moorescloud/holiday-hardware/Holiday ECO 001.pdf

ECO 001 for MooresCloud Holiday r2 PCBA

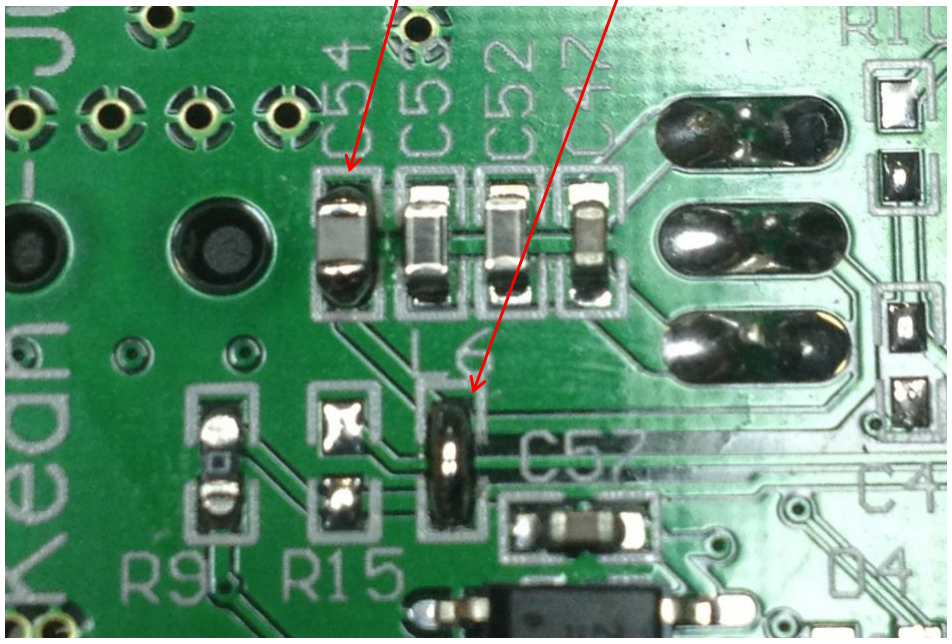
[picture p1: figure]

Prepared by Kean Electronics | Revision 1 | 1 of 2

### Kean Electronics

IT Consulting and embedded systems design
Unit 29, 29 Leighton Place, Hornsby PO Box 3316, Asquith NSW 2077 P: 02 9482 5007 M: 0414 245 326 E: kean@kean.com.au

## MooresCloud Holiday Engineering Change Order ECO 001 for Holiday r2 PCB

18th October 2013

To meet EMC radiated emissions requirements, the following three changes should be made to each Holiday Controller revision 2 PCBA

1) Populate C54 with 680pF 50V NP0 ceramic capacitor (0603 size, although 0805 fits as shown in photo below)
2) Remove L6 and short the pads with solder (or a 0R resistor, 0603 size)

PTO for third change

ECO 001 for MooresCloud Holiday r2 PCBA

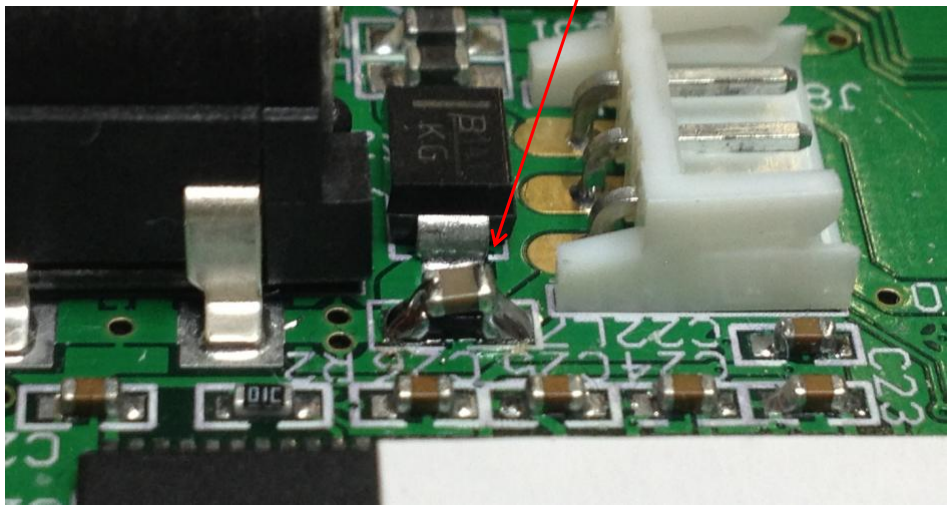
[picture p2: figure]

Prepared by Kean Electronics | Revision 1 | 2 of 2
3) Add C58 a 1uF 50V X7R ceramic capacitor (0805 size) across L7

Parts required:

C54 = Yageo CC0603JRNPO9BN681 DigiKey part: 311-1425-1-ND

C58 = Taiyo Yuden UMK212B7105KG-T DigiKey part: 587-2910-1-ND

Substitutions can be made with equivalent parts, but only on confirmation with MooresCloud technical staff.
