moorescloud/holiday-hardware/Holiday ECO 002.pdf

ECO 002 for MooresCloud Globe r2b PCBA

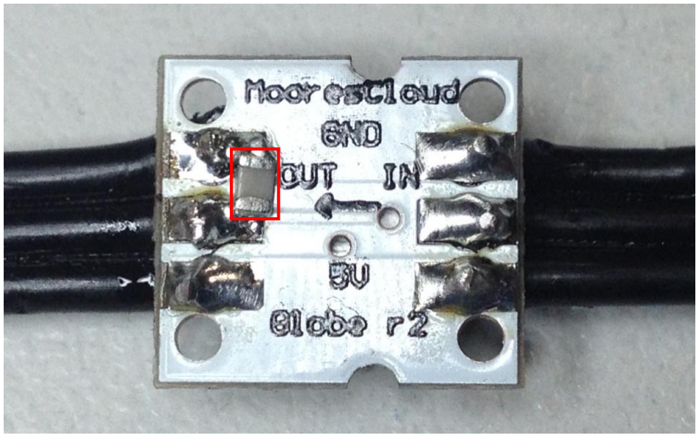
[picture p3: figure]

Prepared by Kean Electronics | Revision 1 | 1 of 2

### Kean Electronics

IT Consulting and embedded systems design
Unit 29, 29 Leighton Place, Hornsby PO Box 3316, Asquith NSW 2077 P: 02 9482 5007 M: 0414 245 326 E: kean@kean.com.au

## MooresCloud Holiday Engineering Change Order ECO 002 for Globe r2b PCBA

18th October 2013

To meet EMC radiated emissions requirements, the following change should be made to each Globe PCBA in a Holiday LED string:

1) Add C2 a 470pF 50V NP0/C0G ceramic capacitor (0805 size, 2.0x1.25mm, 0.8mm thick) between GND and DOUT solder pads on the bottom side of the PCB. The capacitor should be kept flat to ensure the PCBA still fits within the globe housing

(sufficient clearance is available). It can be mounted close to the PCB edge, or close to the OUT label.

Recommended position:

ECO 002 for MooresCloud Globe r2b PCBA

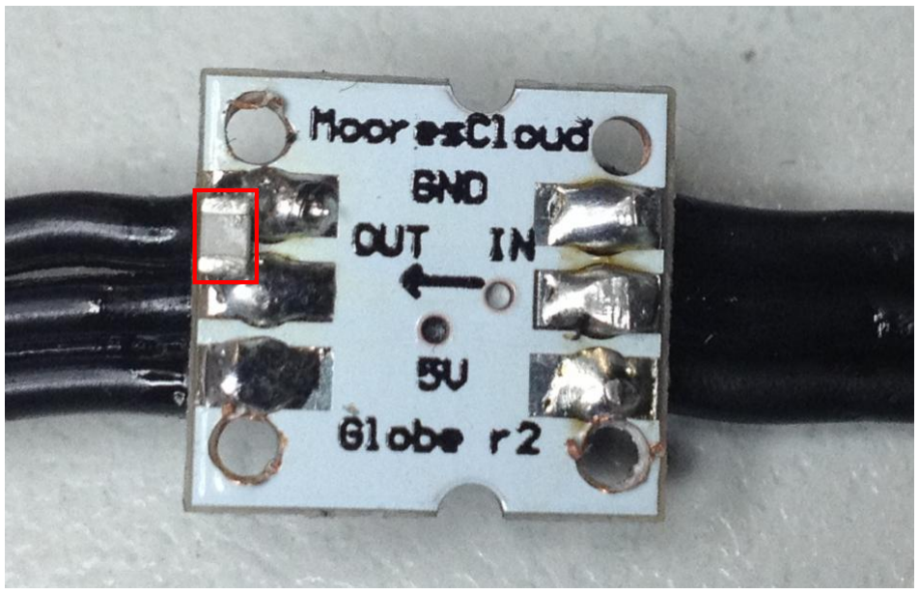
[picture p4: figure]

Prepared by Kean Electronics | Revision 1 | 2 of 2

Alternate position:

Parts required:

C2 = AVX 08055A471JAT2A DigiKey: 478-1324-2-ND

Substitutions can be made with equivalent parts, but only on confirmation with MooresCloud technical staff.
