moorescloud/holiday-hardware/Holiday r2 Schematic.PDF

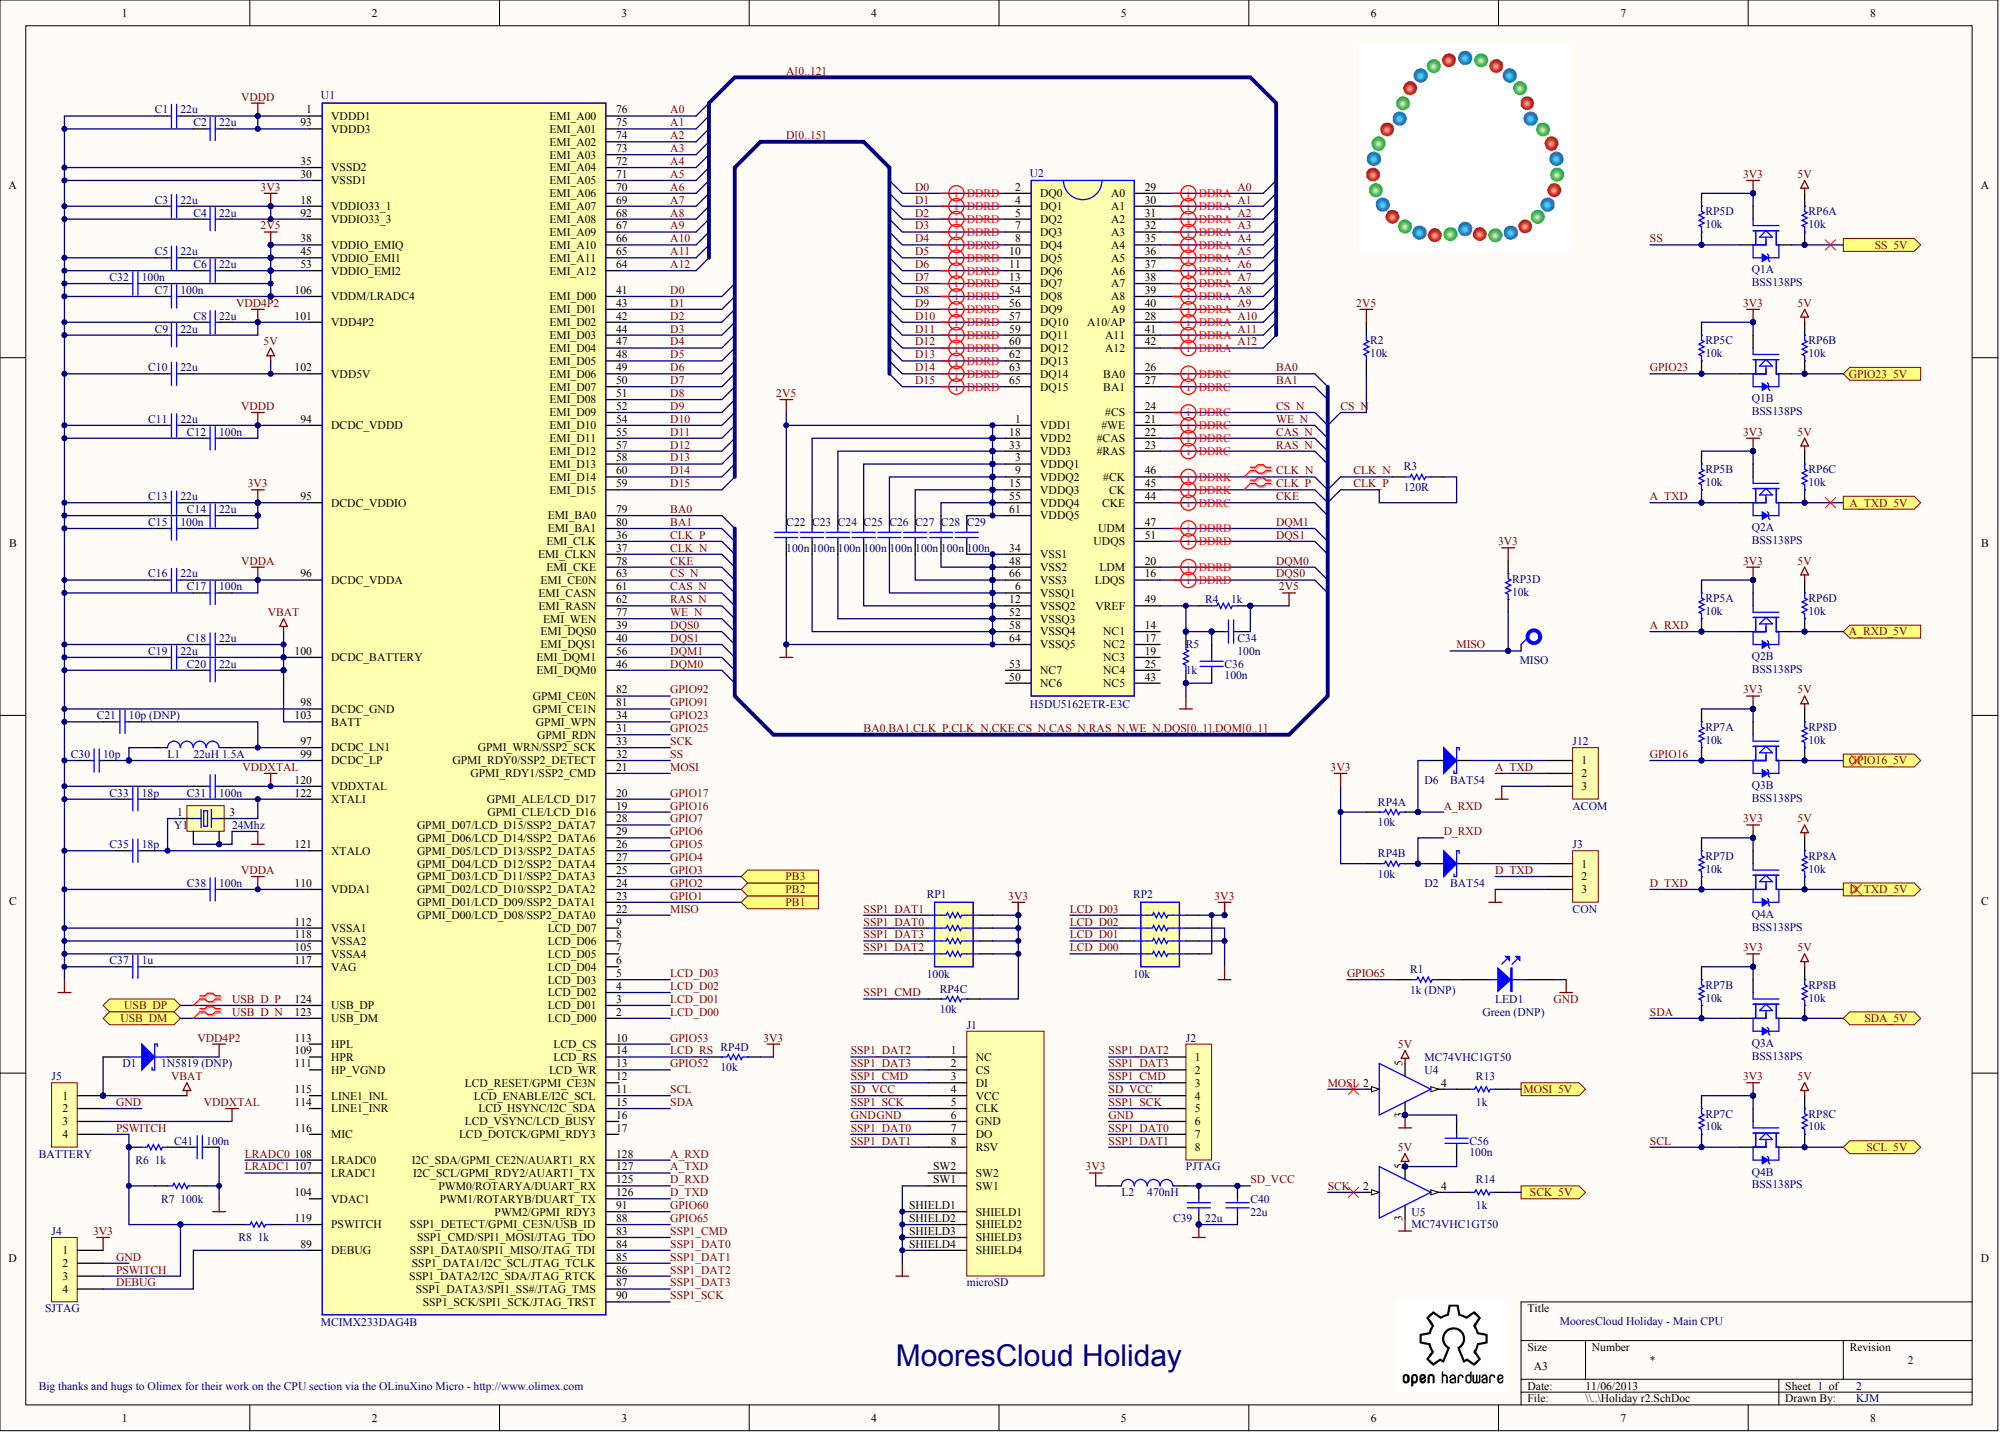
[picture p26: page 1]

i DDRD i DDRD i DDRD i DDRD i DDRD i DDRD i DDRD i DDRD i DDRD i DDRD i DDRD i DDRD i DDRD i DDRD i DDRD

i DDRA i DDRK i DDRK
i DDRA i DDRA i DDRA i DDRA i DDRA i DDRA i DDRA i DDRA i DDRA i DDRA i DDRA i DDRA i DDRD i DDRD i DDRD i DDRD

i DDRC i DDRC i DDRC i DDRC i DDRC i DDRC i DDRC

VDDQ3 15 | CLK_P
VDDQ4 55

VSS2 48
VSS3 66

VSSQ2 12

VSSQ4 58

SHIELD1
SHIELD2
SHIELD3

MooresCloud Holiday - Main CPU

Big thanks and hugs to Olimex for their work on the CPU section via the OLinuXino Micro - http://w

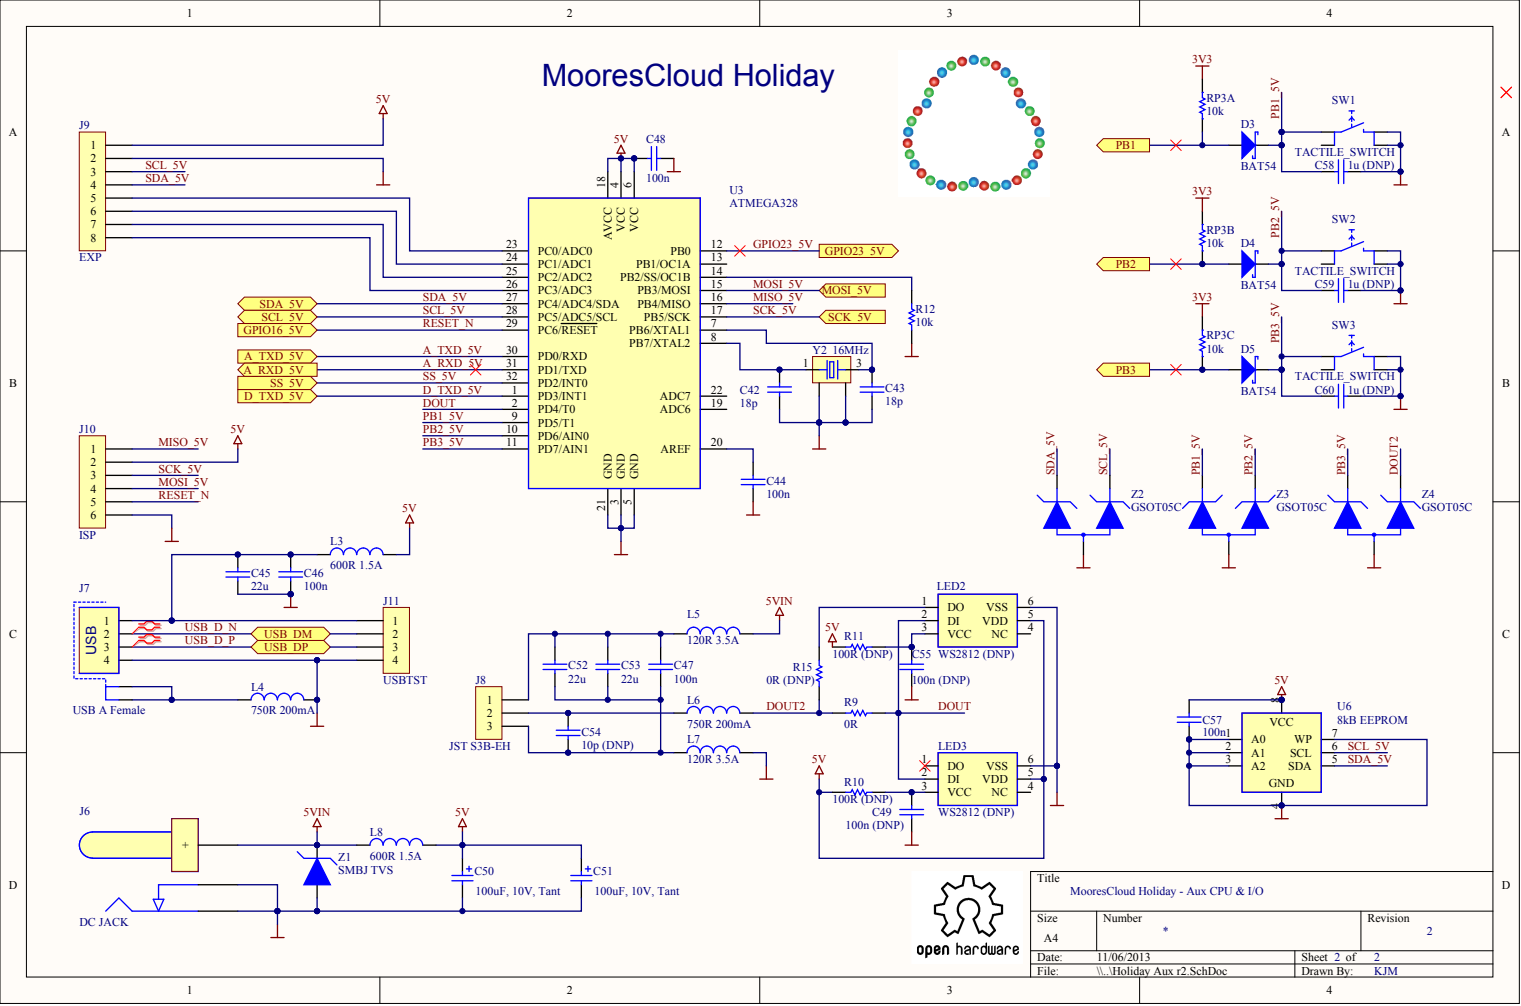
[picture p27: page 2]

PC2/ADC2 25
PC3/ADC3 26 | MOSI_5V

PD0/RXD 30 | 8

Y2 16MHz 1

MooresCloud Holiday - Aux CPU & I/O
