moorescloud/holiday-hardware/Holiday r1.pdf

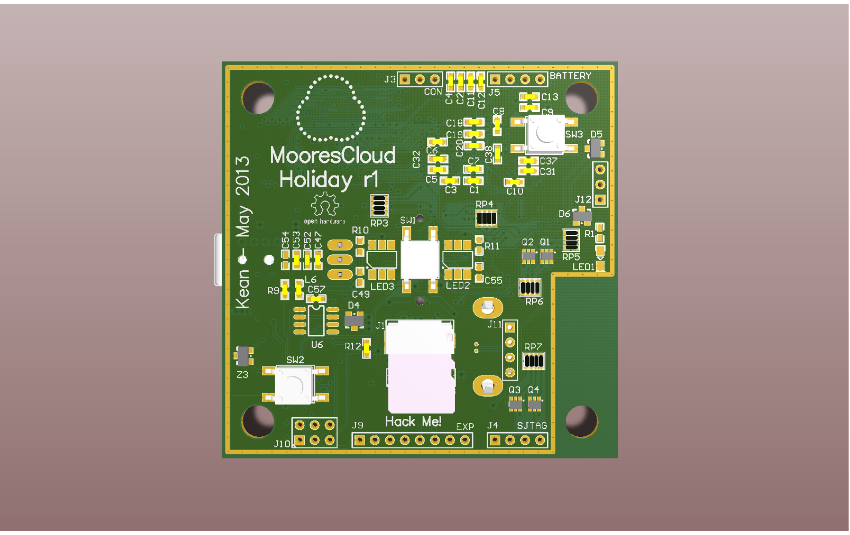
[picture p28: page 1]

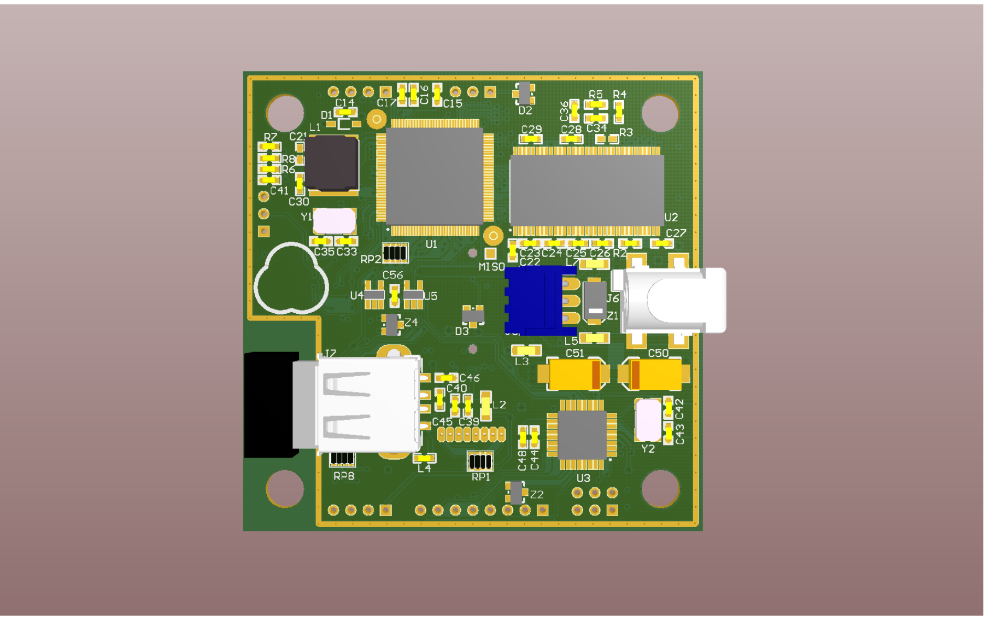
[picture p29: page 2]

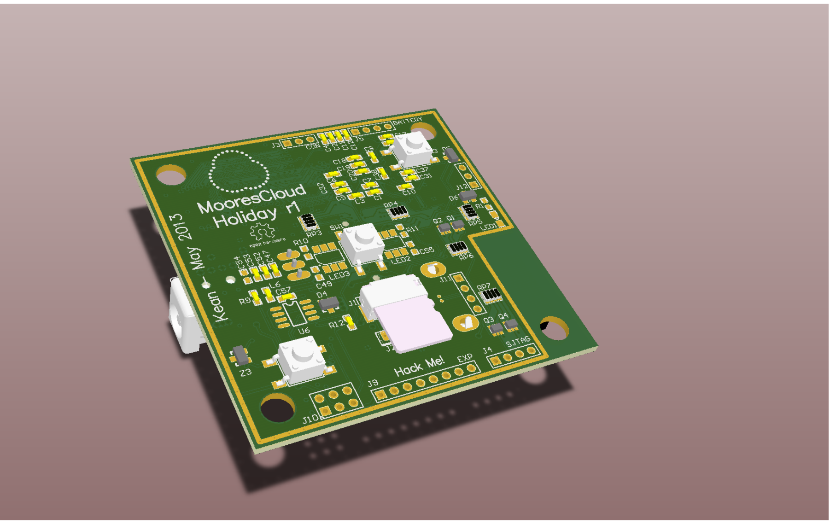
[picture p30: page 3]

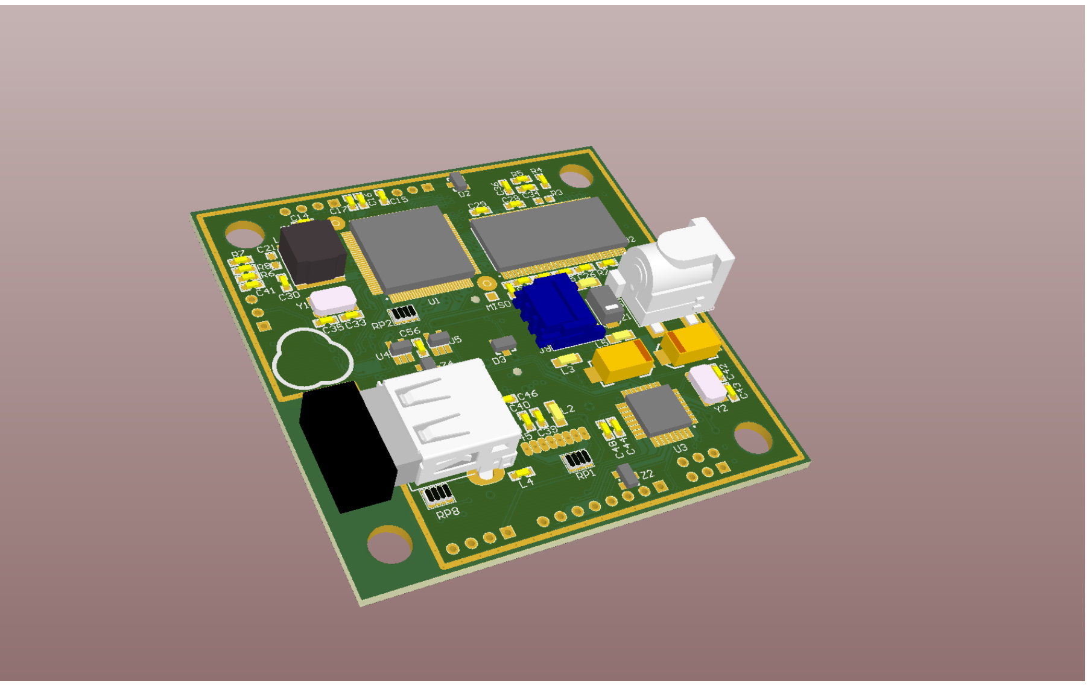
[picture p31: page 4]

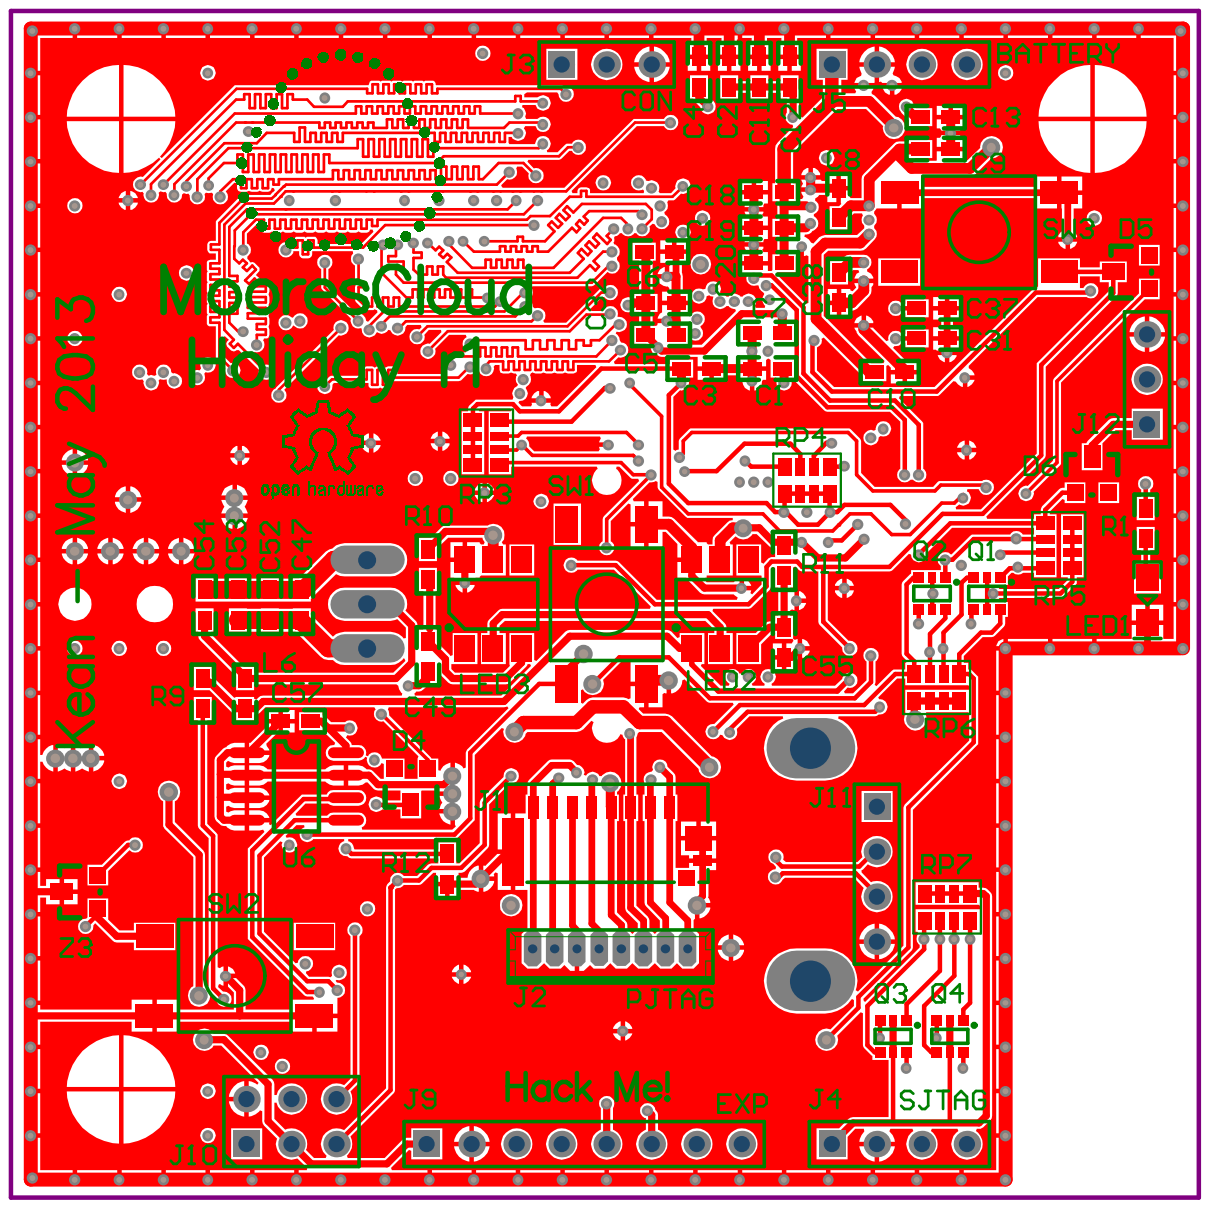
[picture p32: page 5]

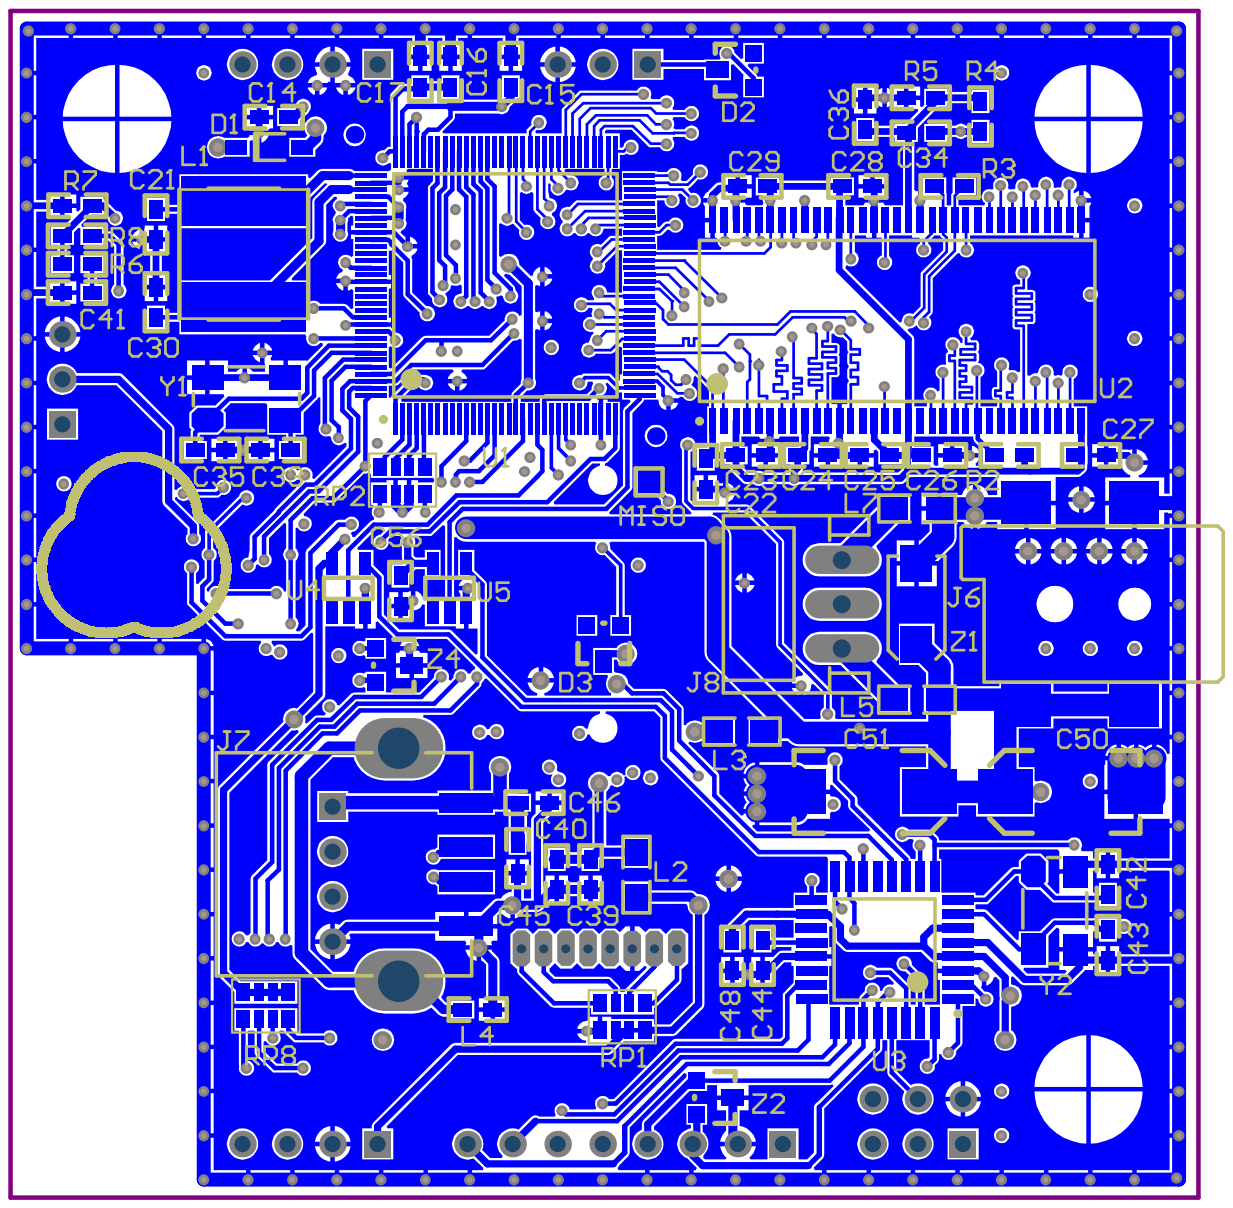
[picture p33: page 6]

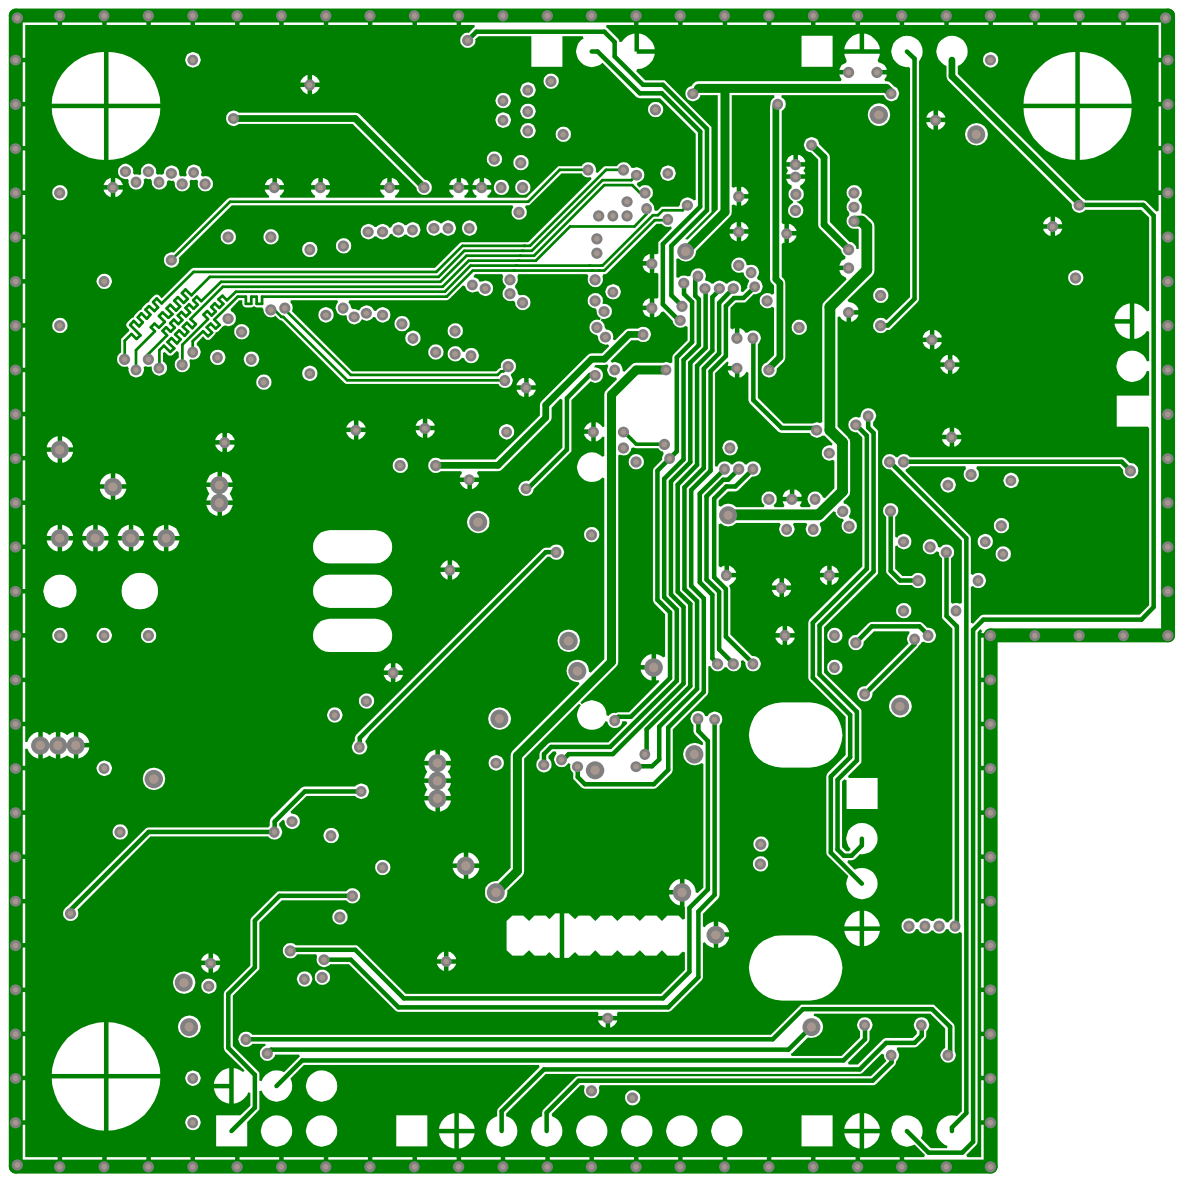
[picture p34: page 7]

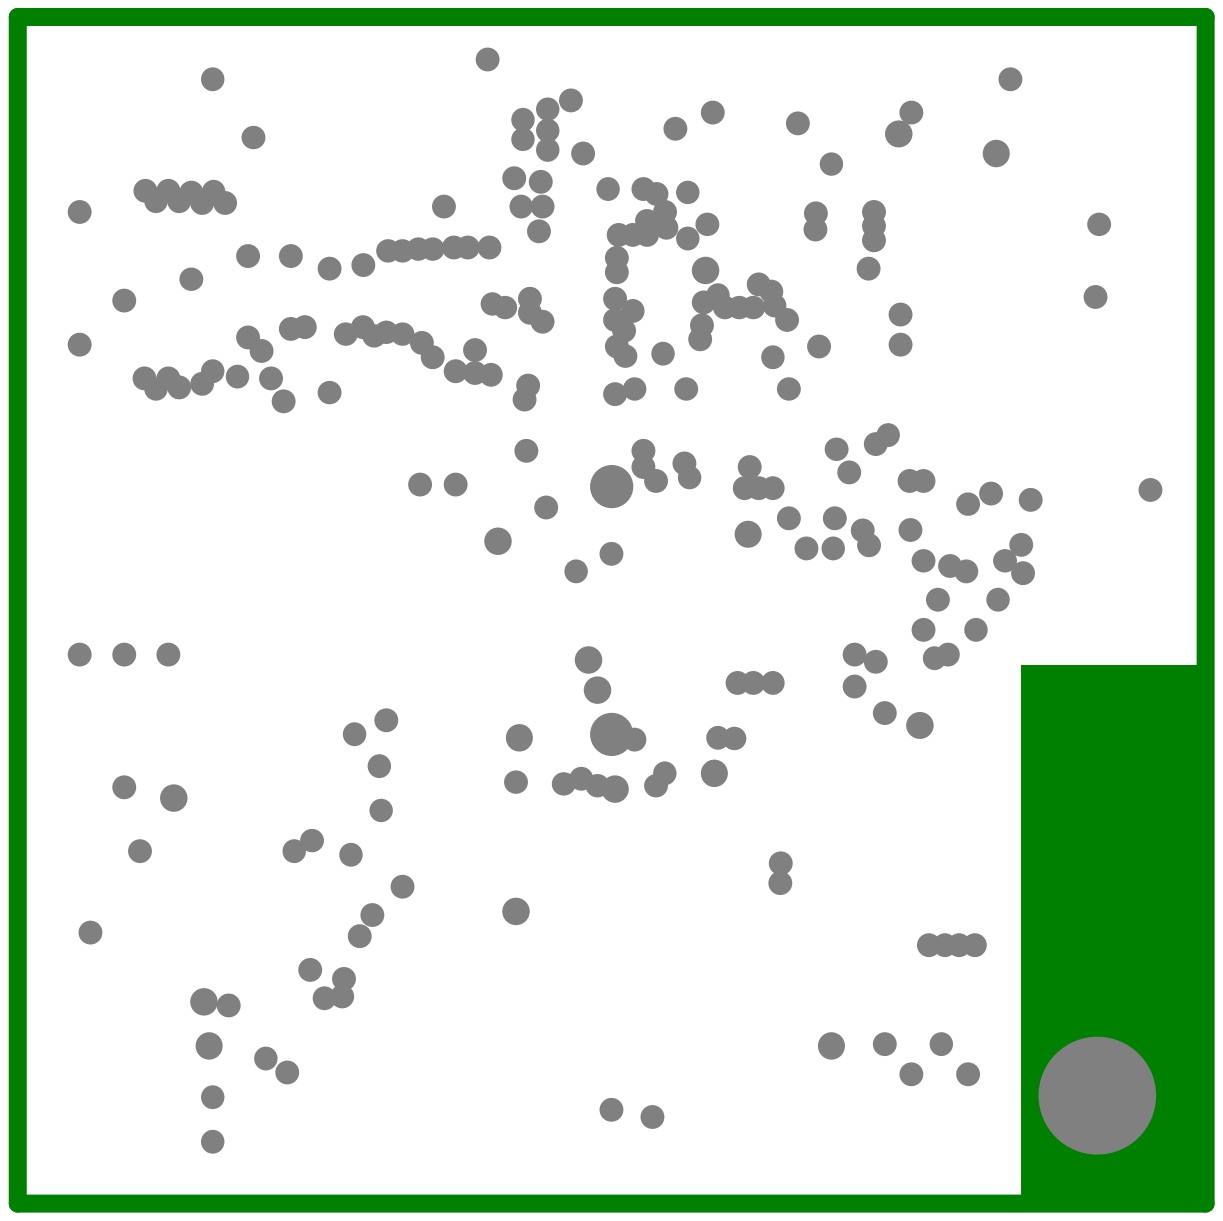
[picture p35: page 8]

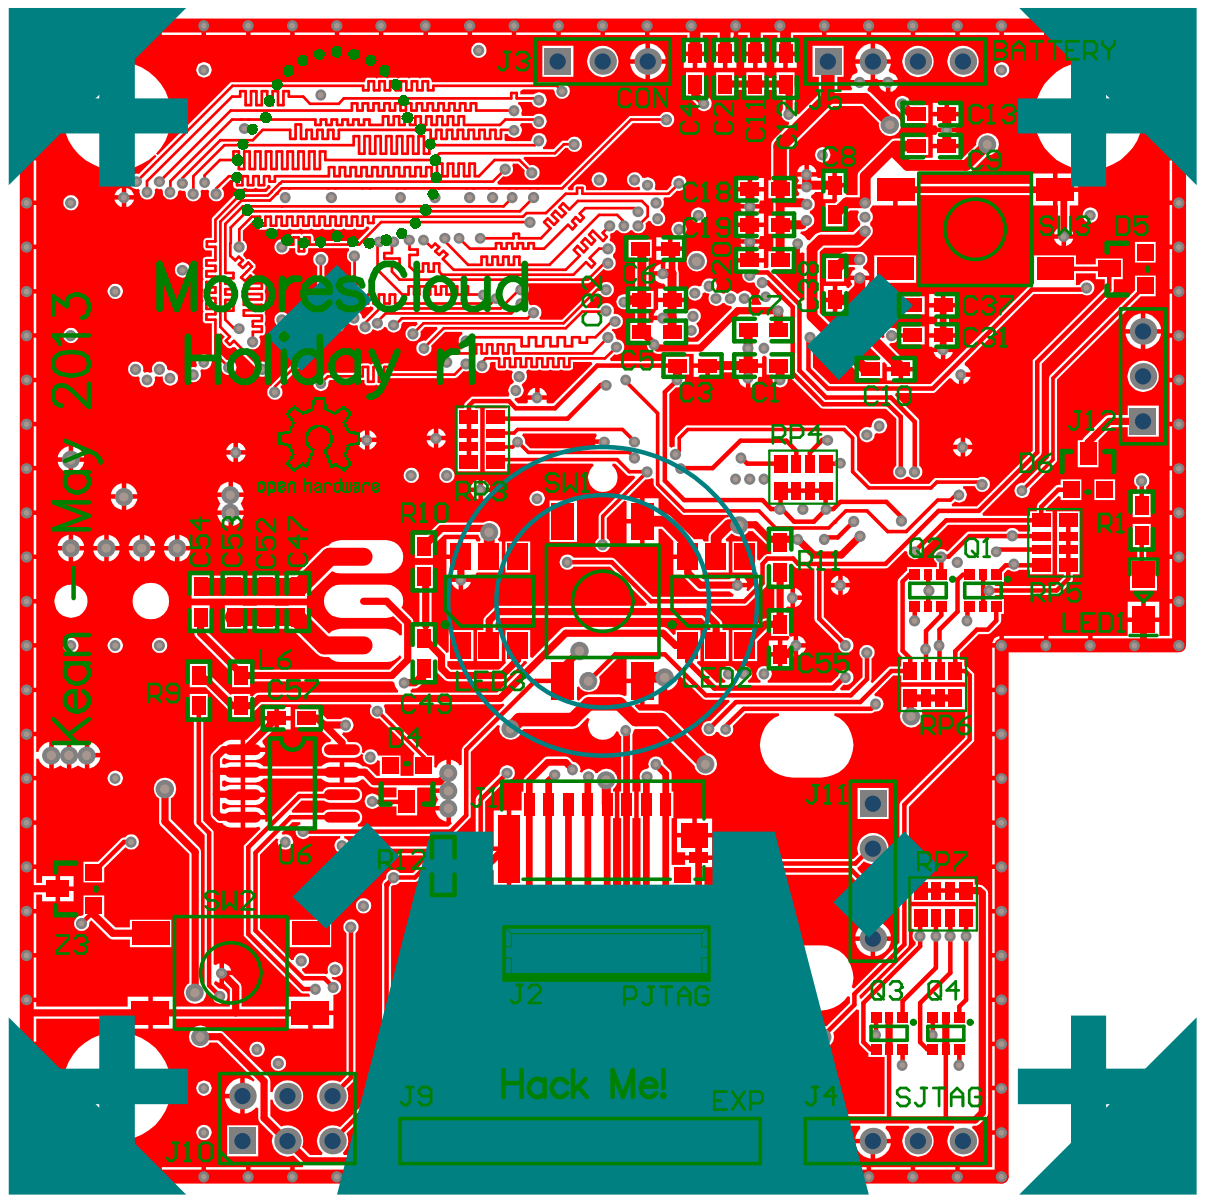
[picture p36: page 9]

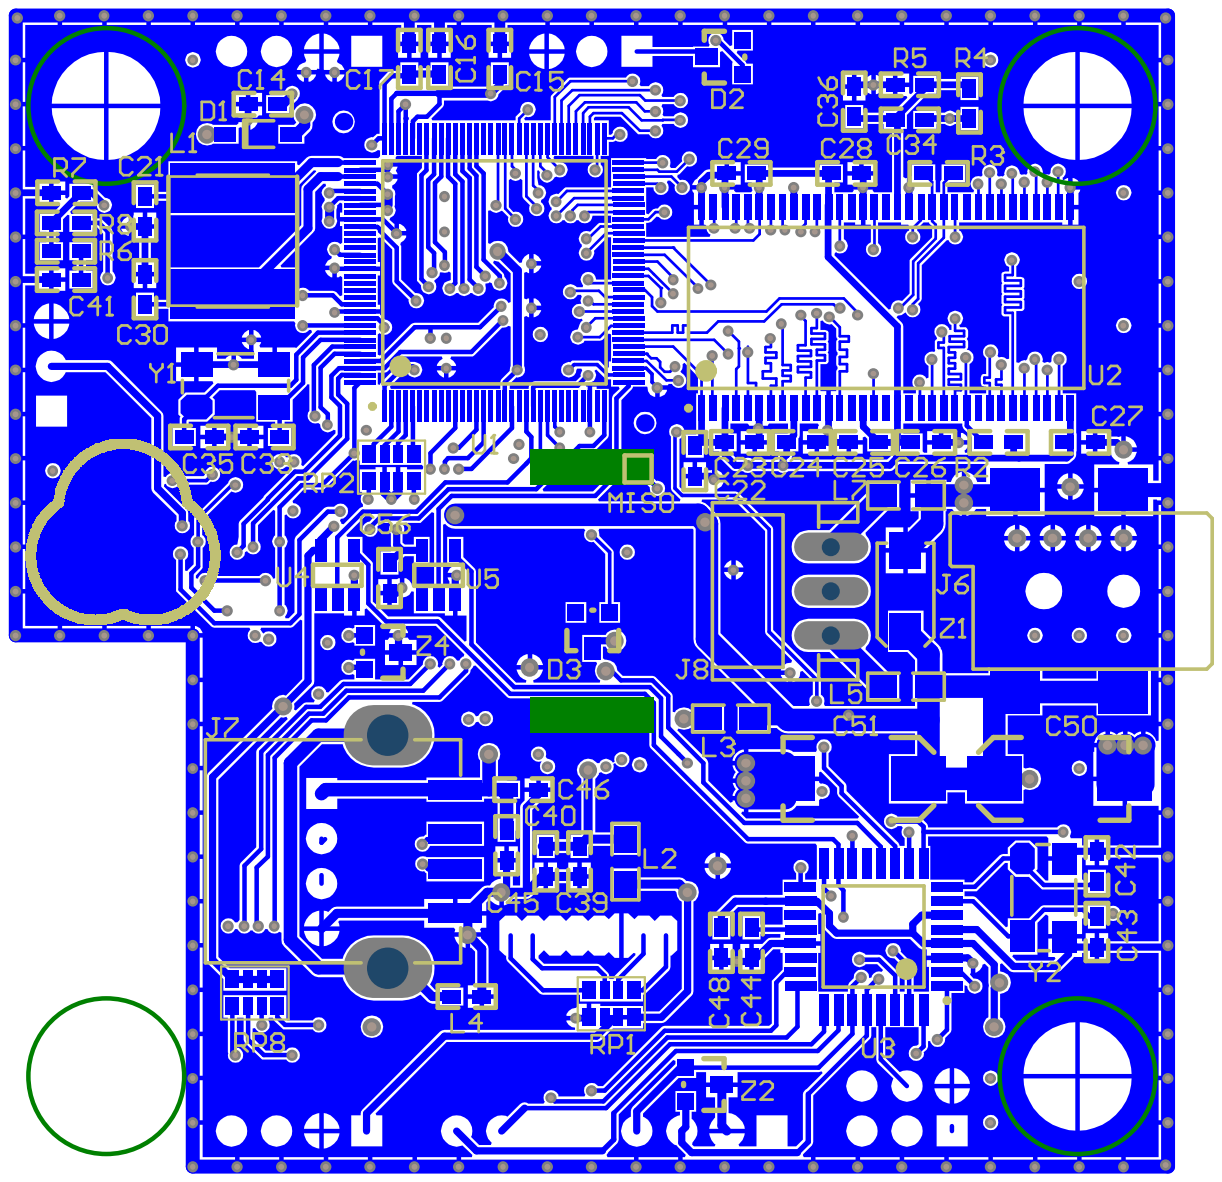
[picture p37: page 10]

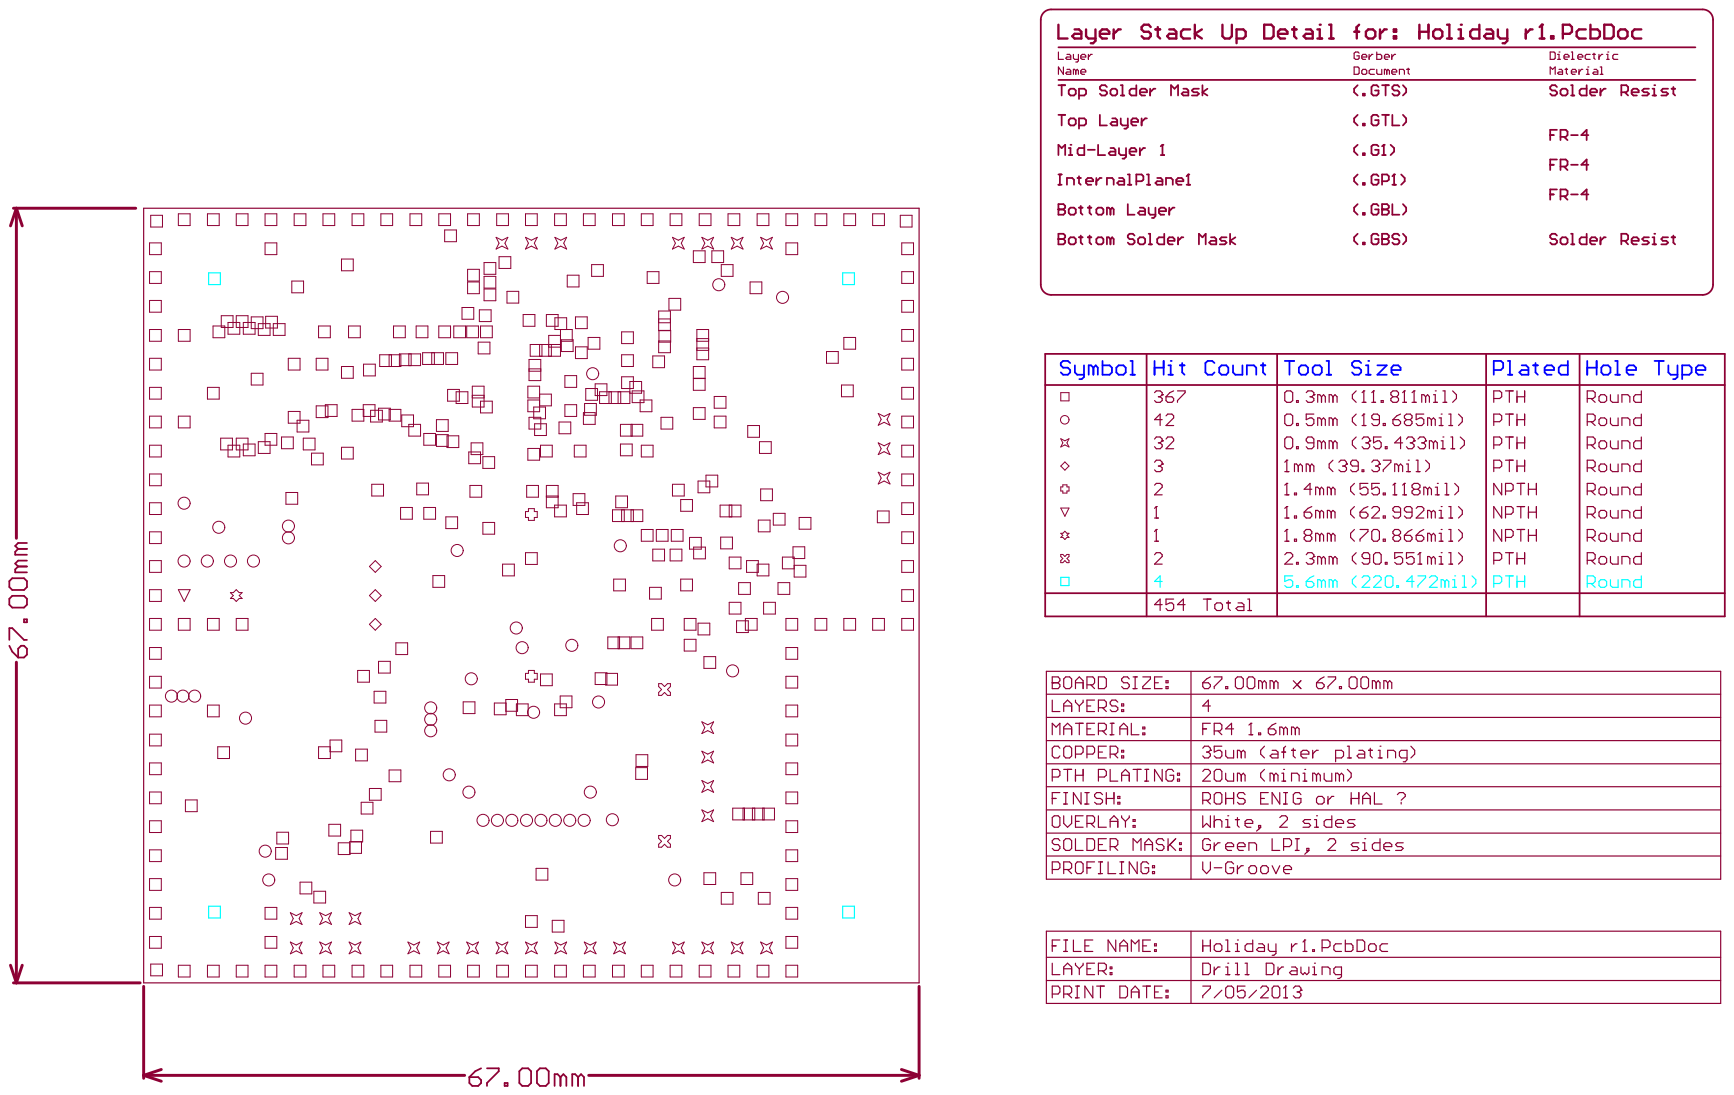
[picture p38: page 11]
