moorescloud/holiday-hardware/MooresGlobe r1 Panel.PDF

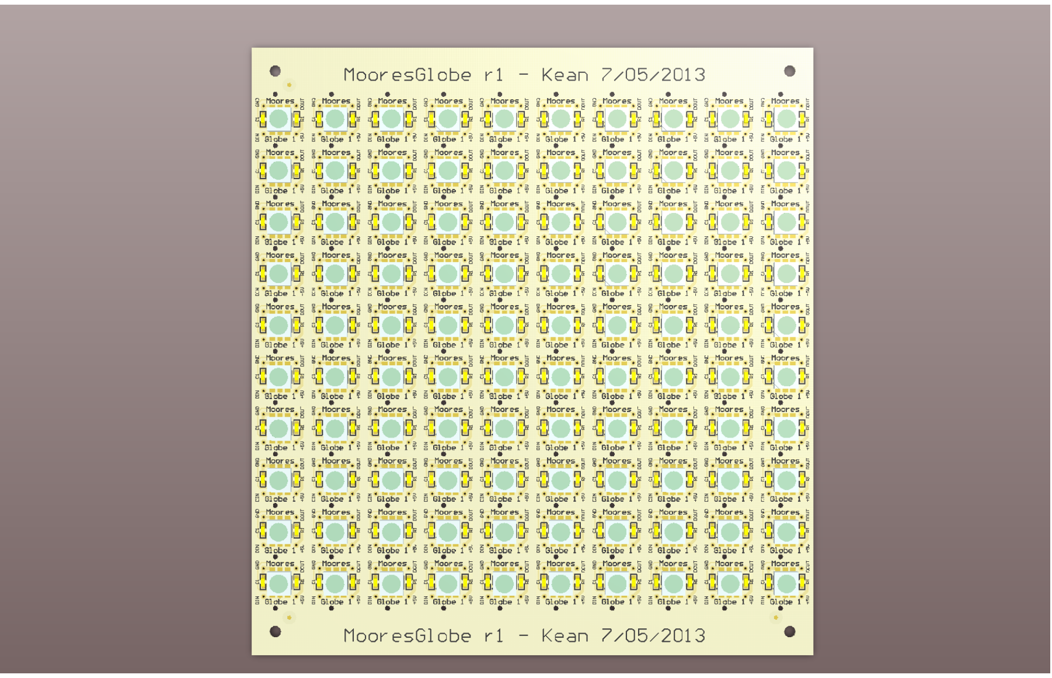
[picture p39: page 1]

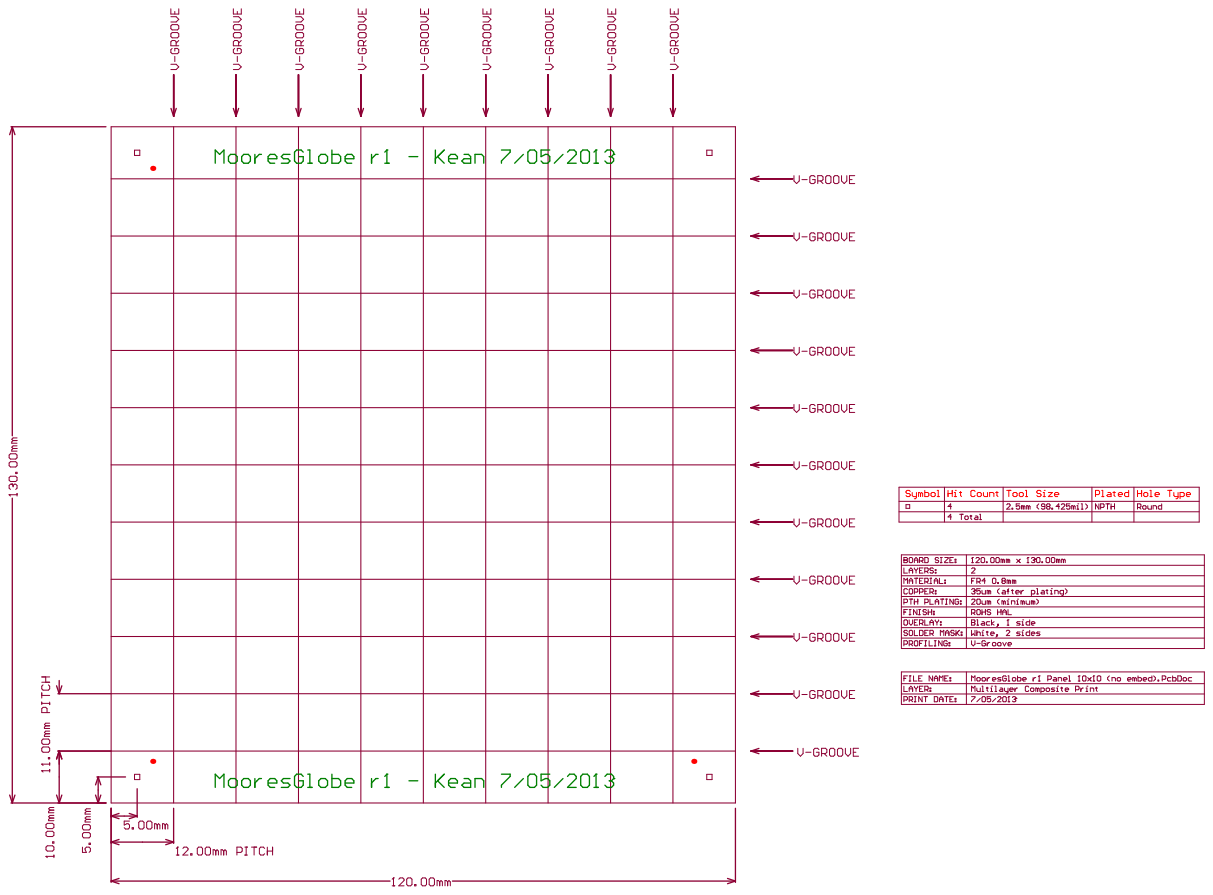
[picture p40: page 2]
