moorescloud/holiday-hardware/MooresGlobe r1.PDF

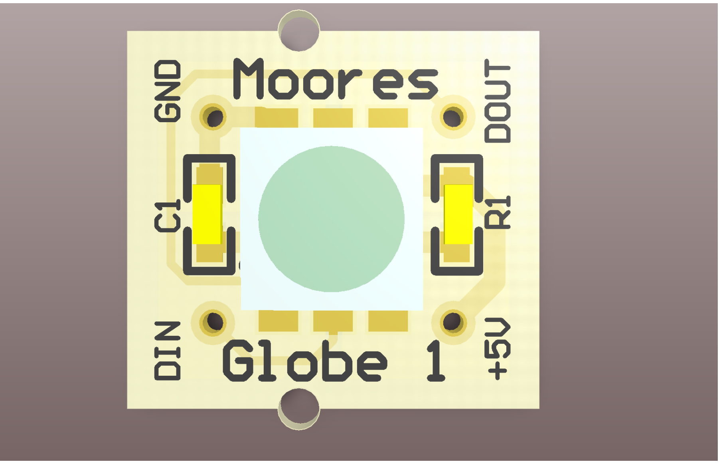
[picture p41: page 1]

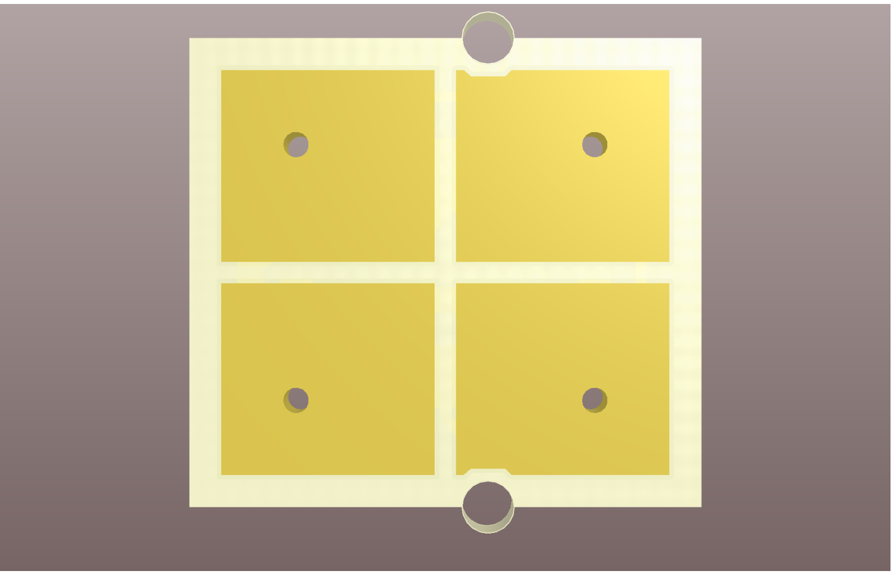
[picture p42: page 2]

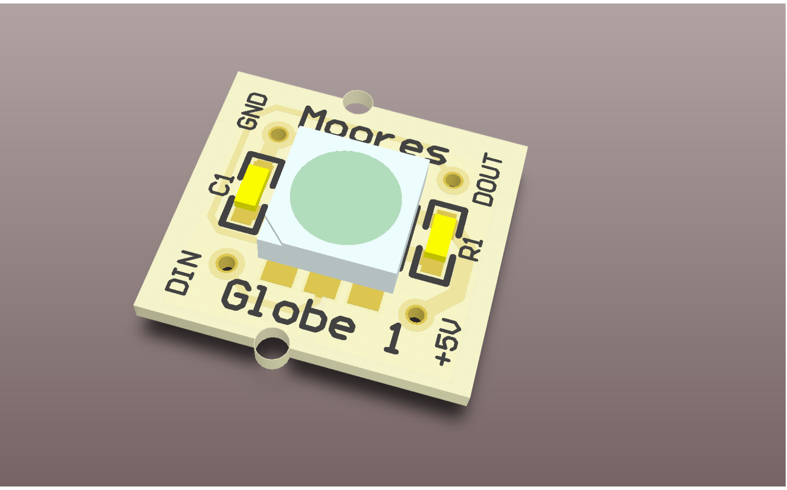
[picture p43: page 3]

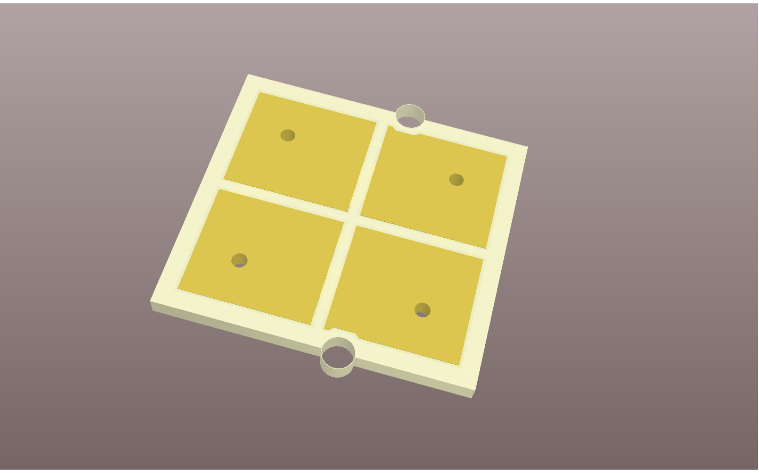
[picture p44: page 4]

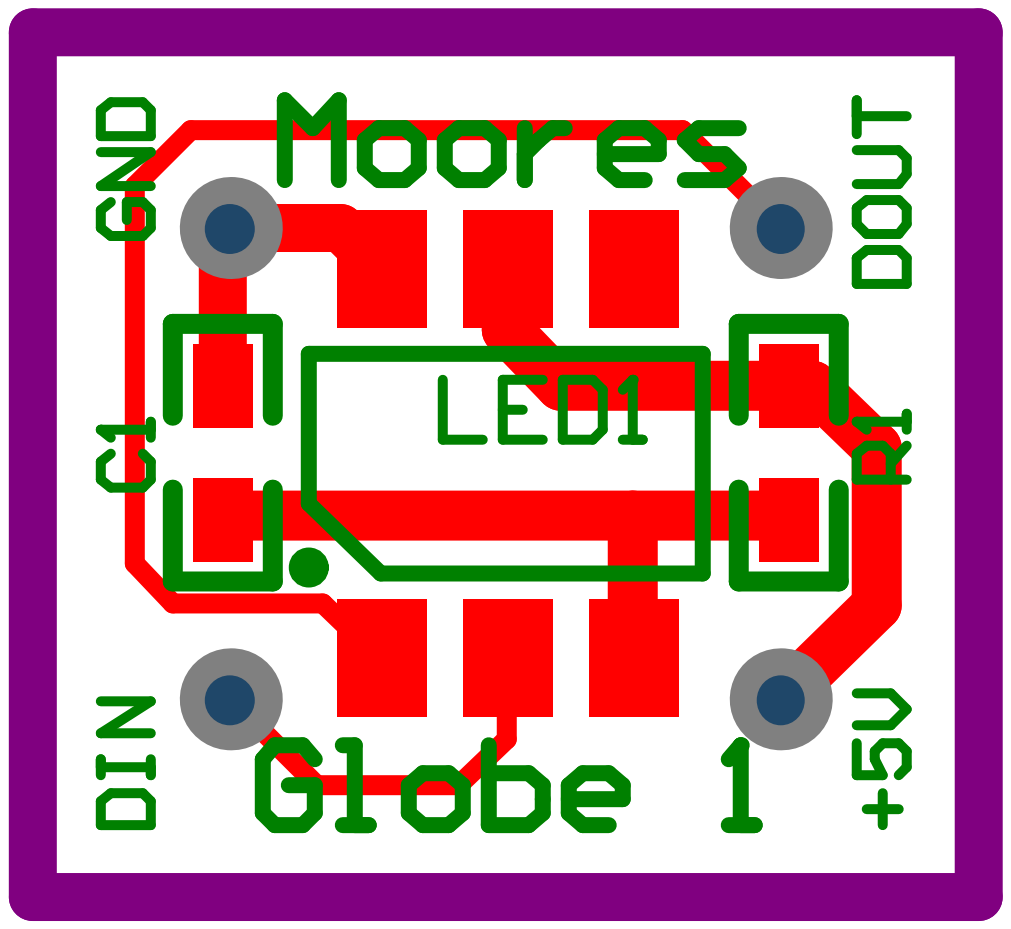
[picture p45: page 5]

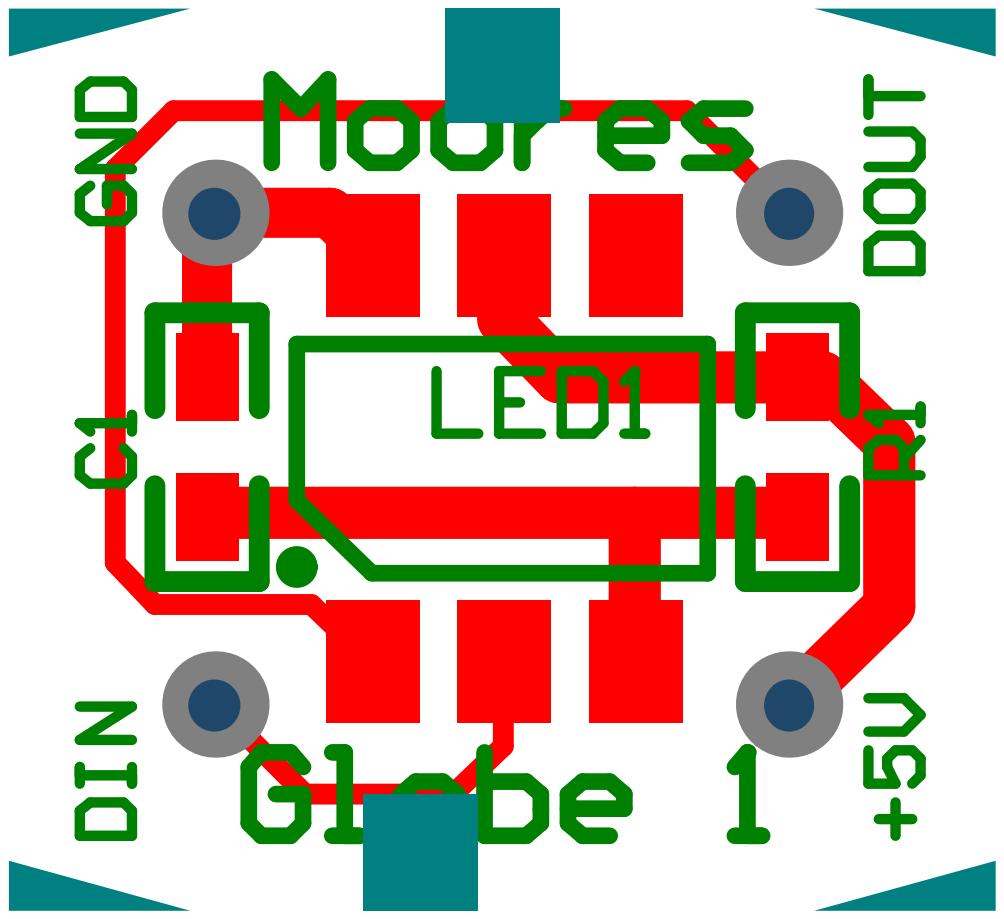
[picture p46: page 7]

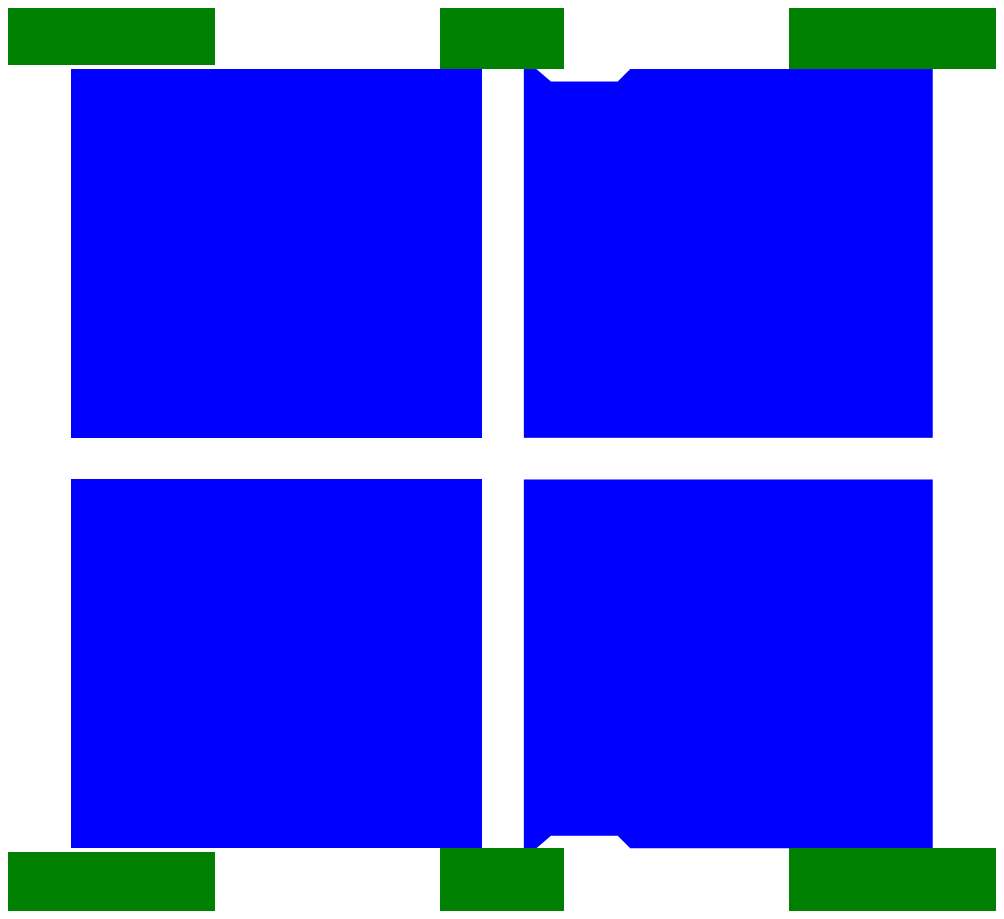
[picture p47: page 8]

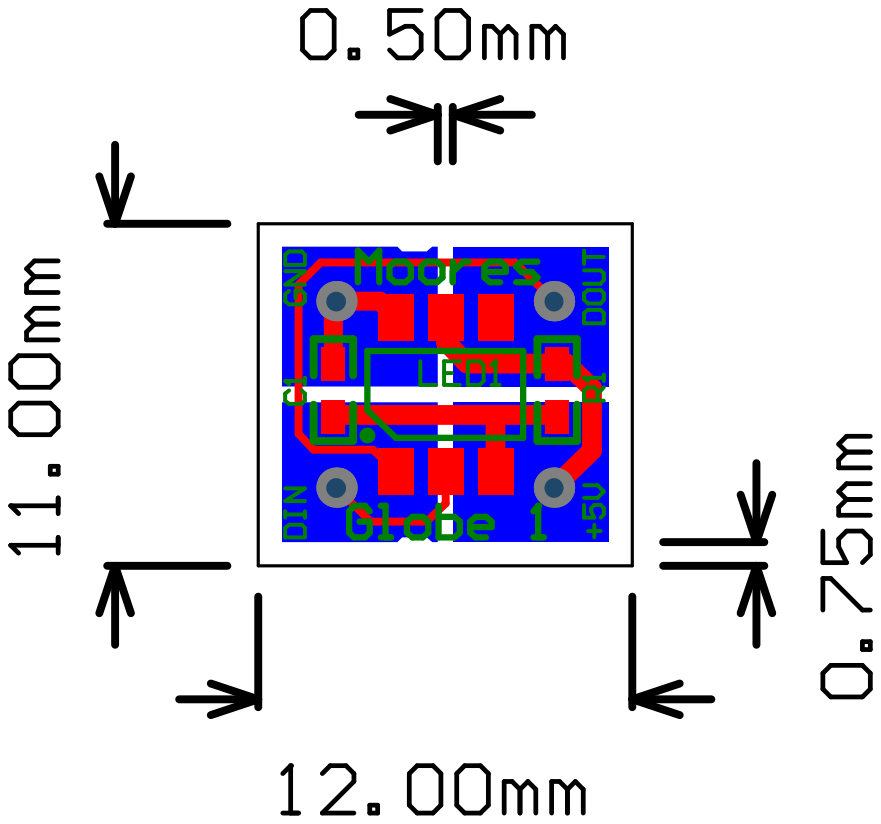
[picture p48: page 9]

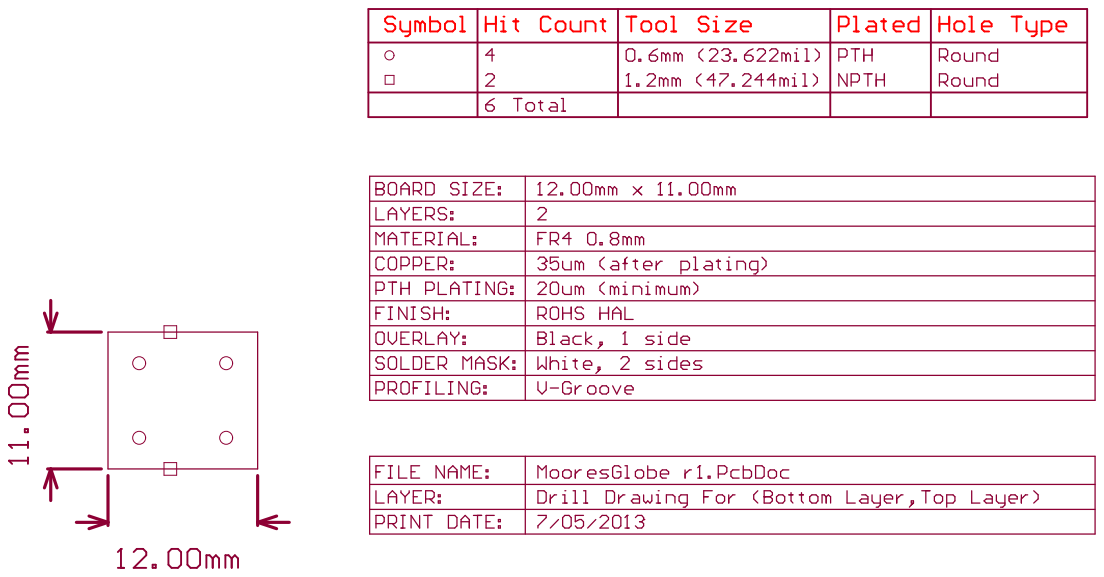
[picture p49: page 10]
