moorescloud/holiday-hardware/MooresGlobe r1S Panel.PDF

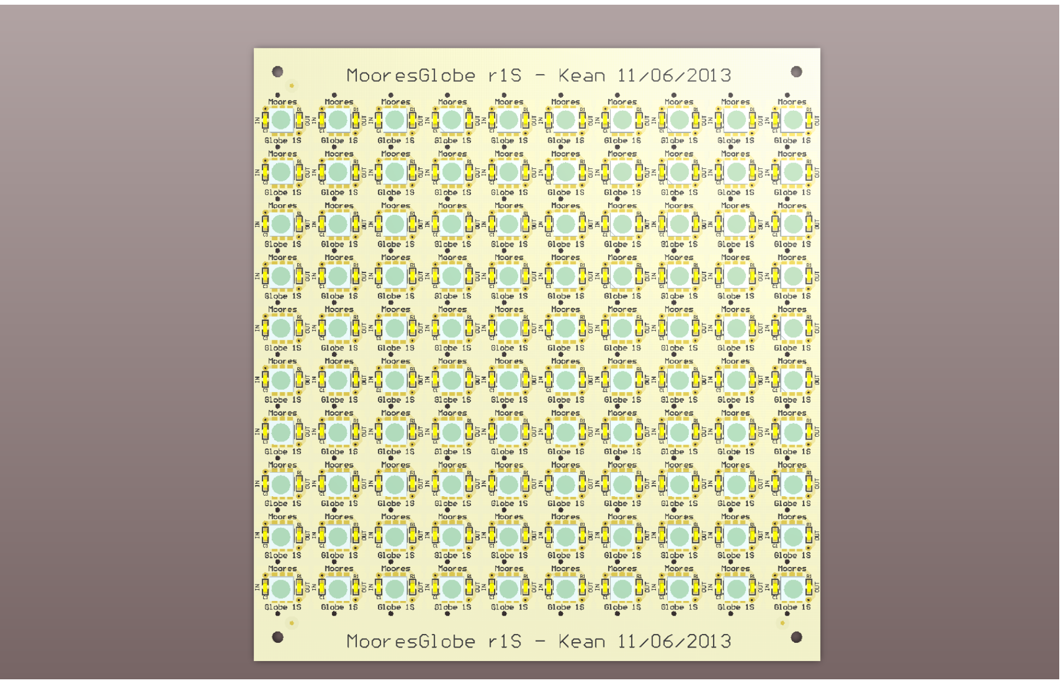
[picture p50: page 1]

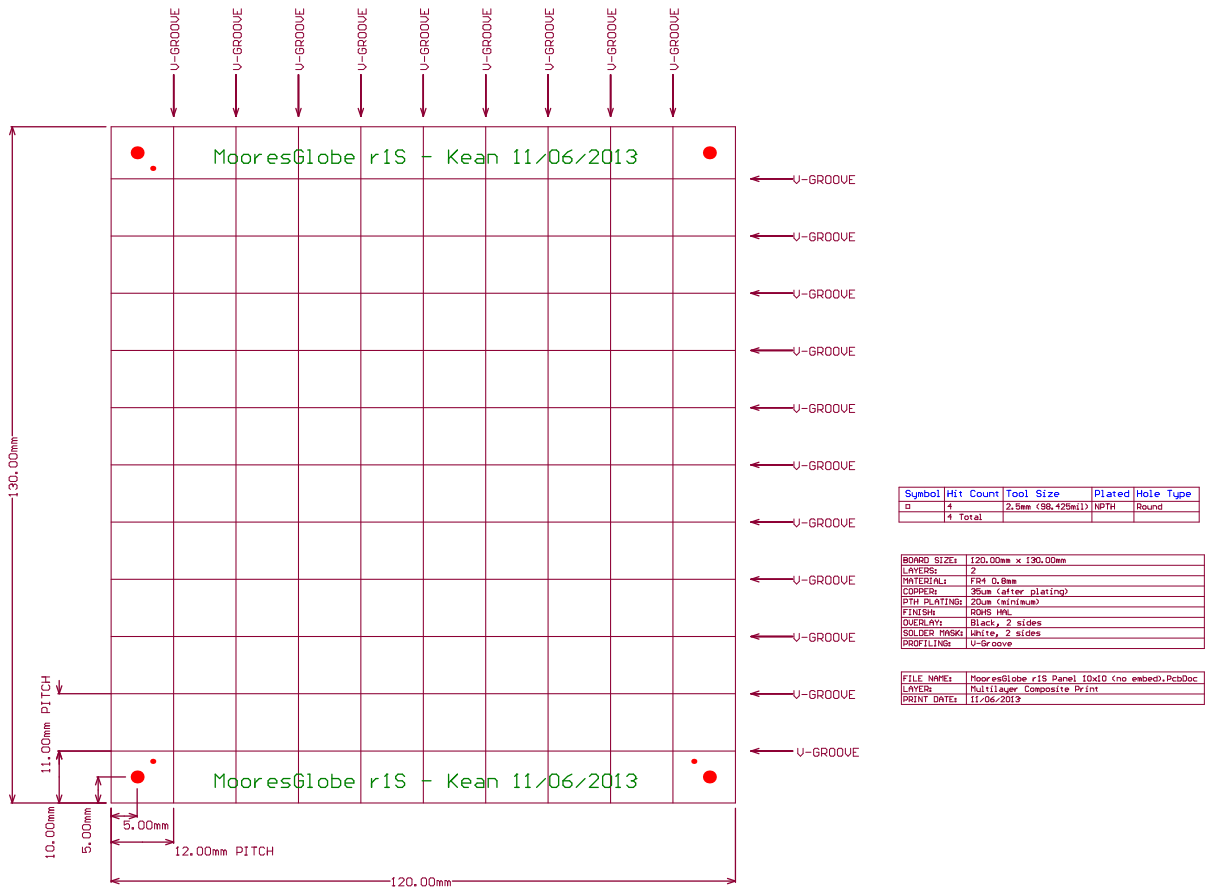
[picture p51: page 2]
