moorescloud/holiday-hardware/MooresGlobe r2 Panel.PDF

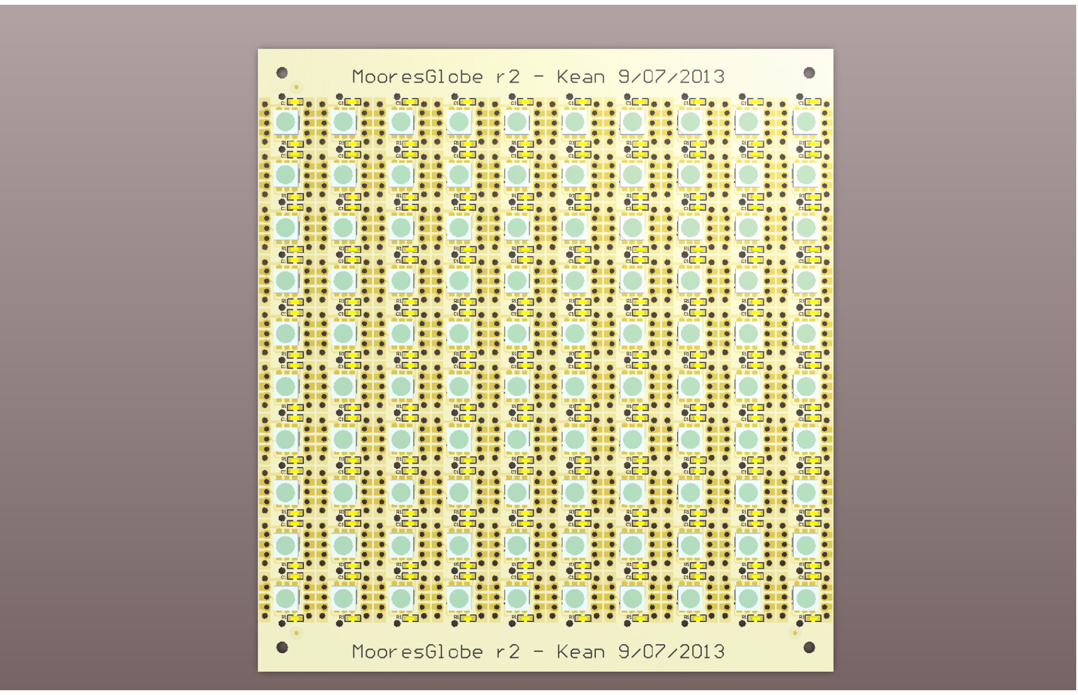
[picture p62: page 1]

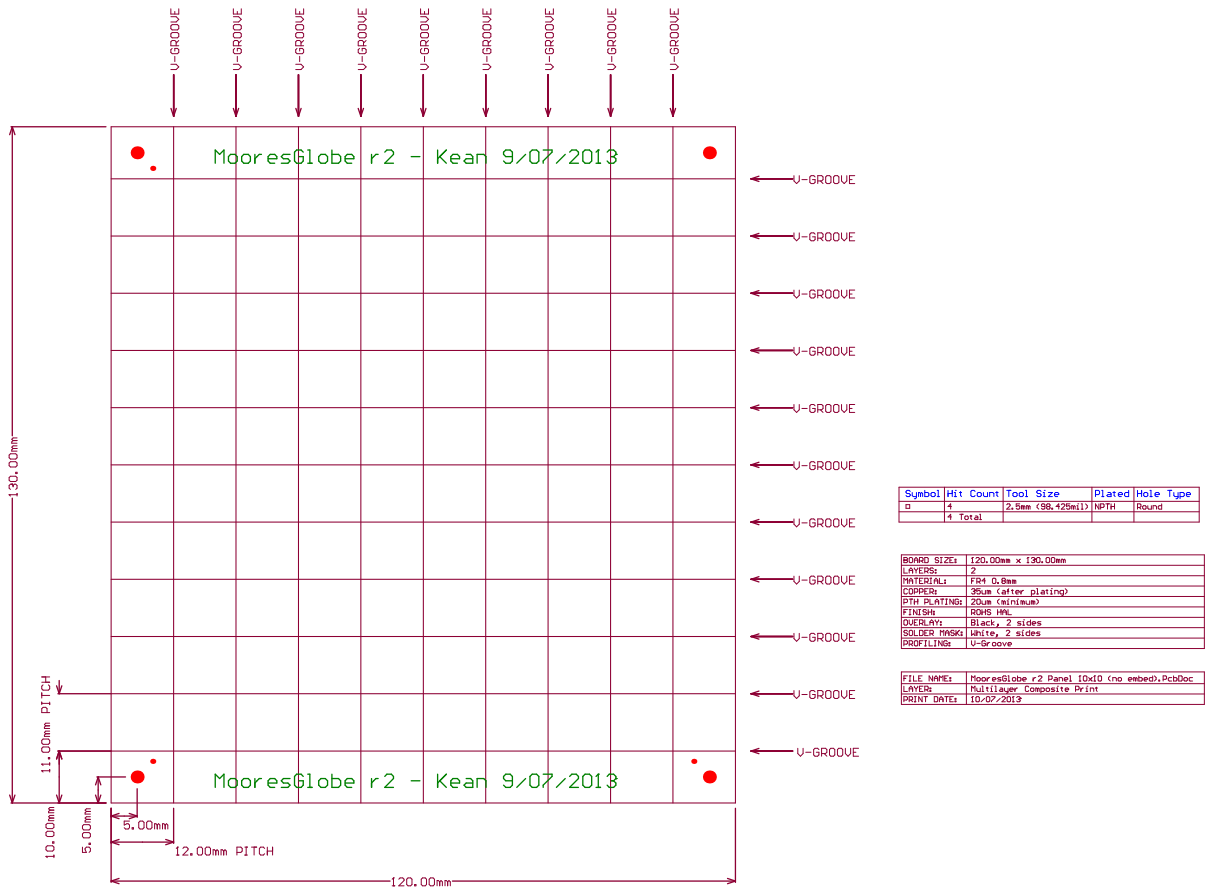
[picture p63: page 2]
