moorescloud/holiday-hardware/MooresGlobe r2.PDF

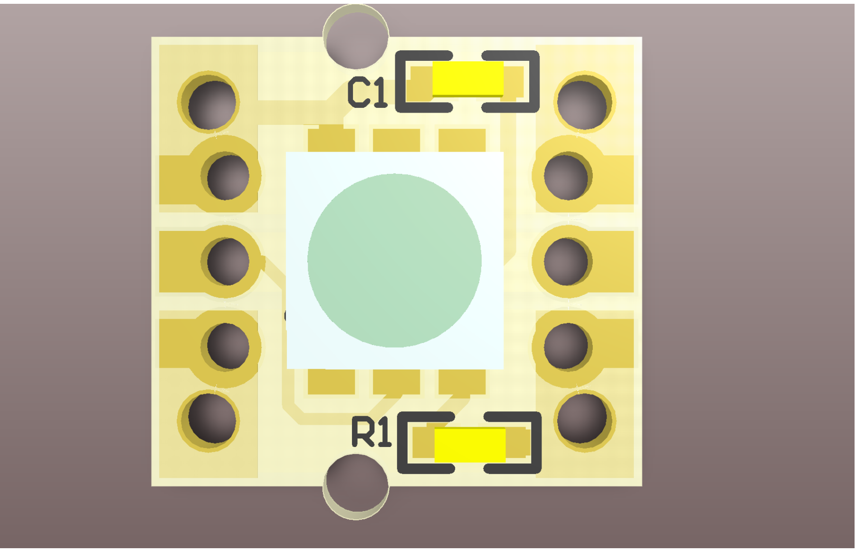
[picture p64: page 1]

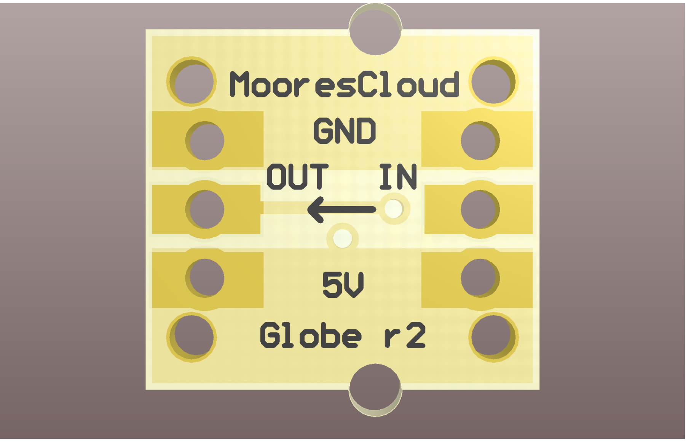
[picture p65: page 2]

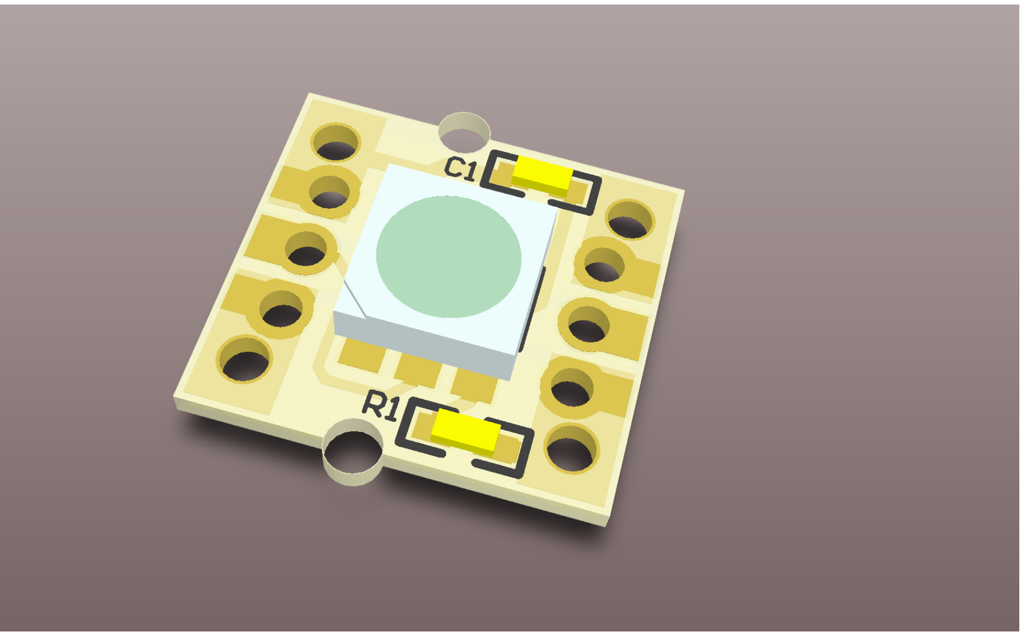
[picture p66: page 3]

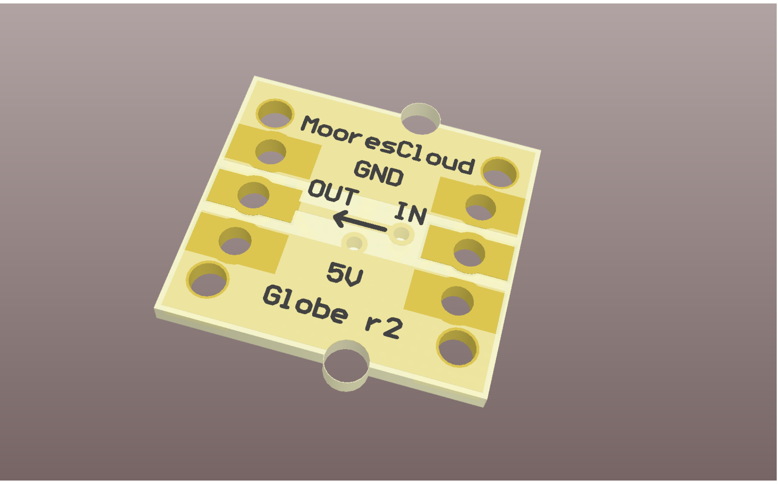
[picture p67: page 4]

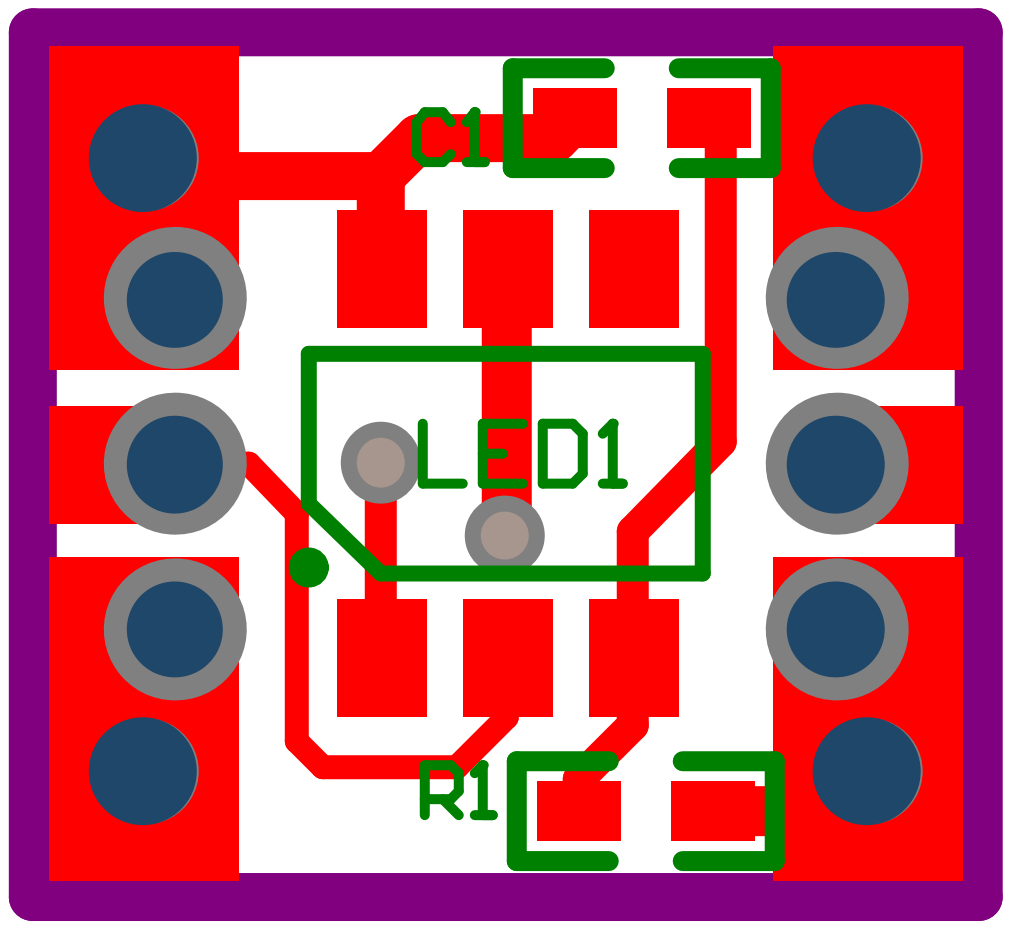
[picture p68: page 5]

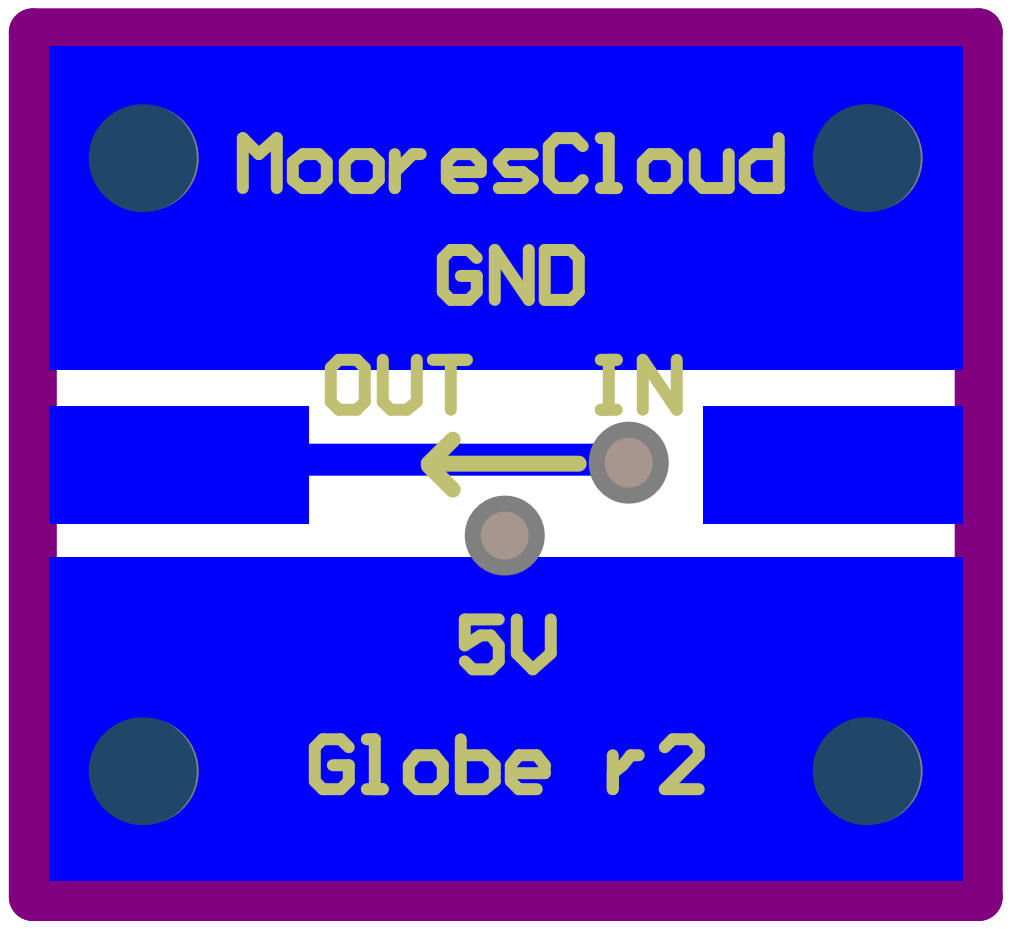
[picture p69: page 6]

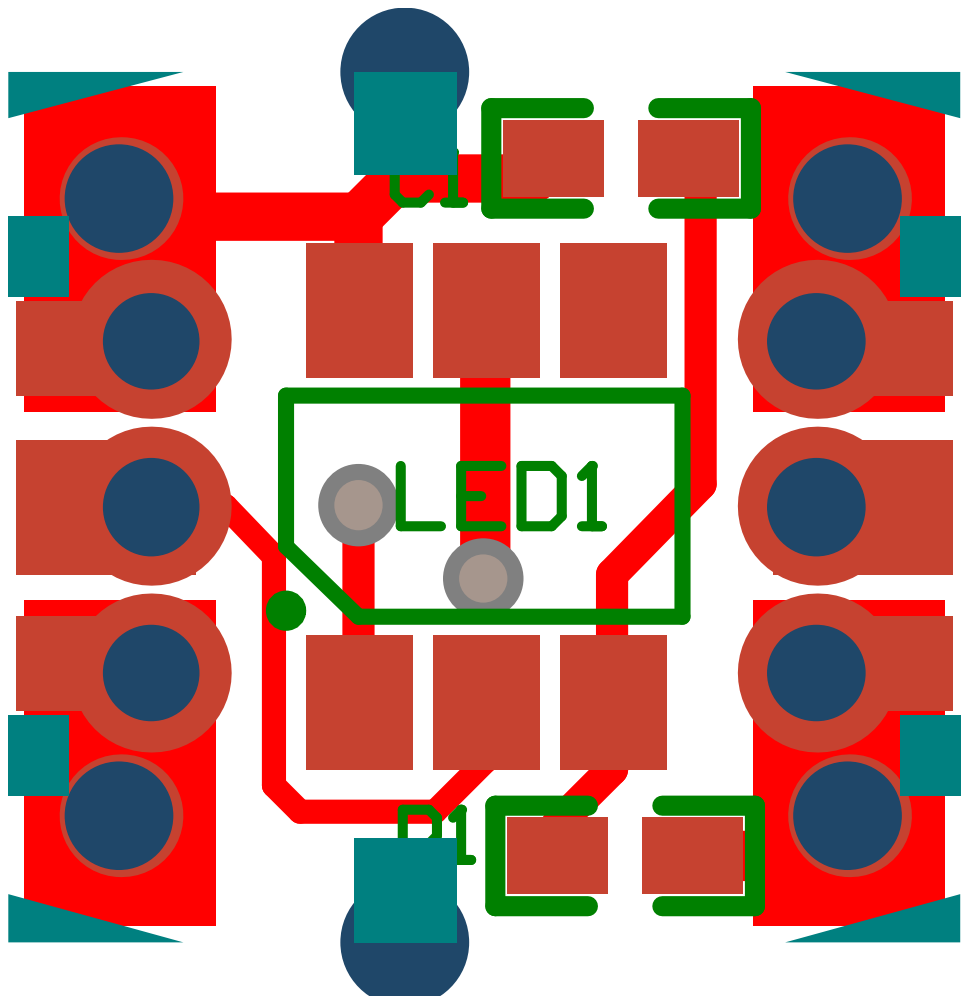
[picture p70: page 7]

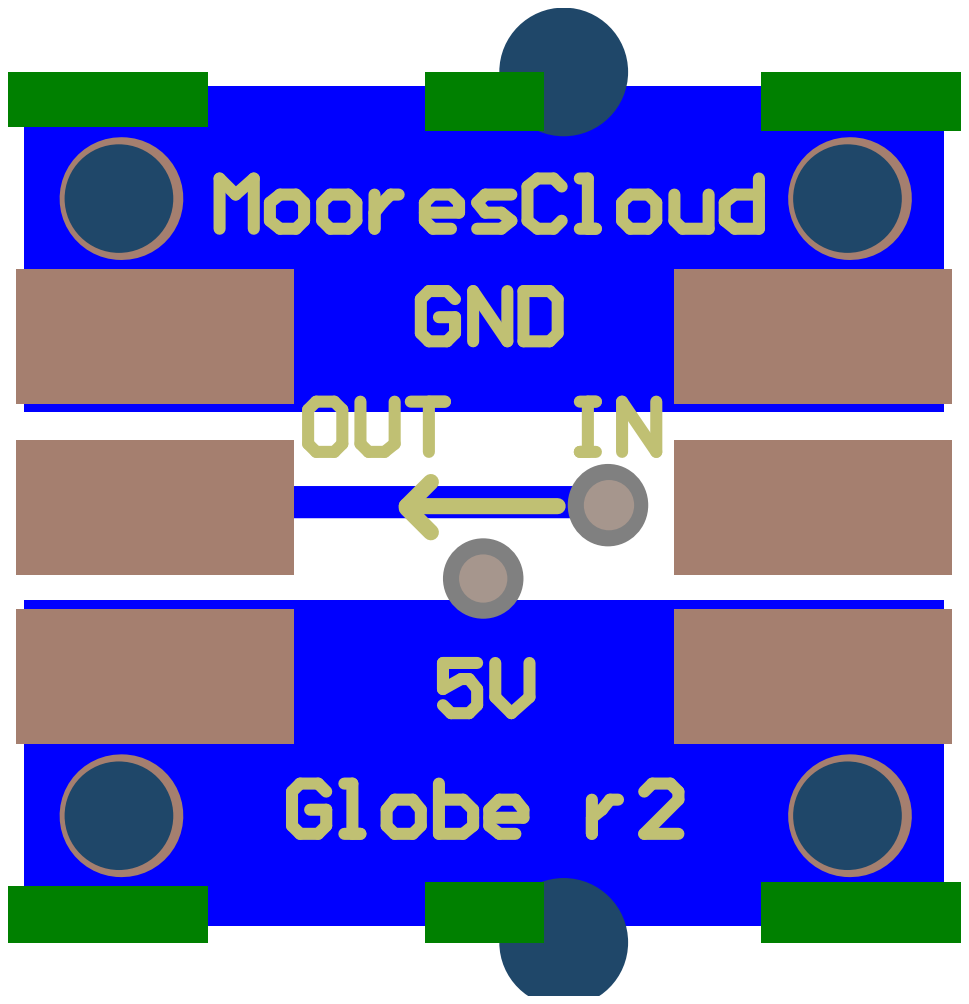
[picture p71: page 8]

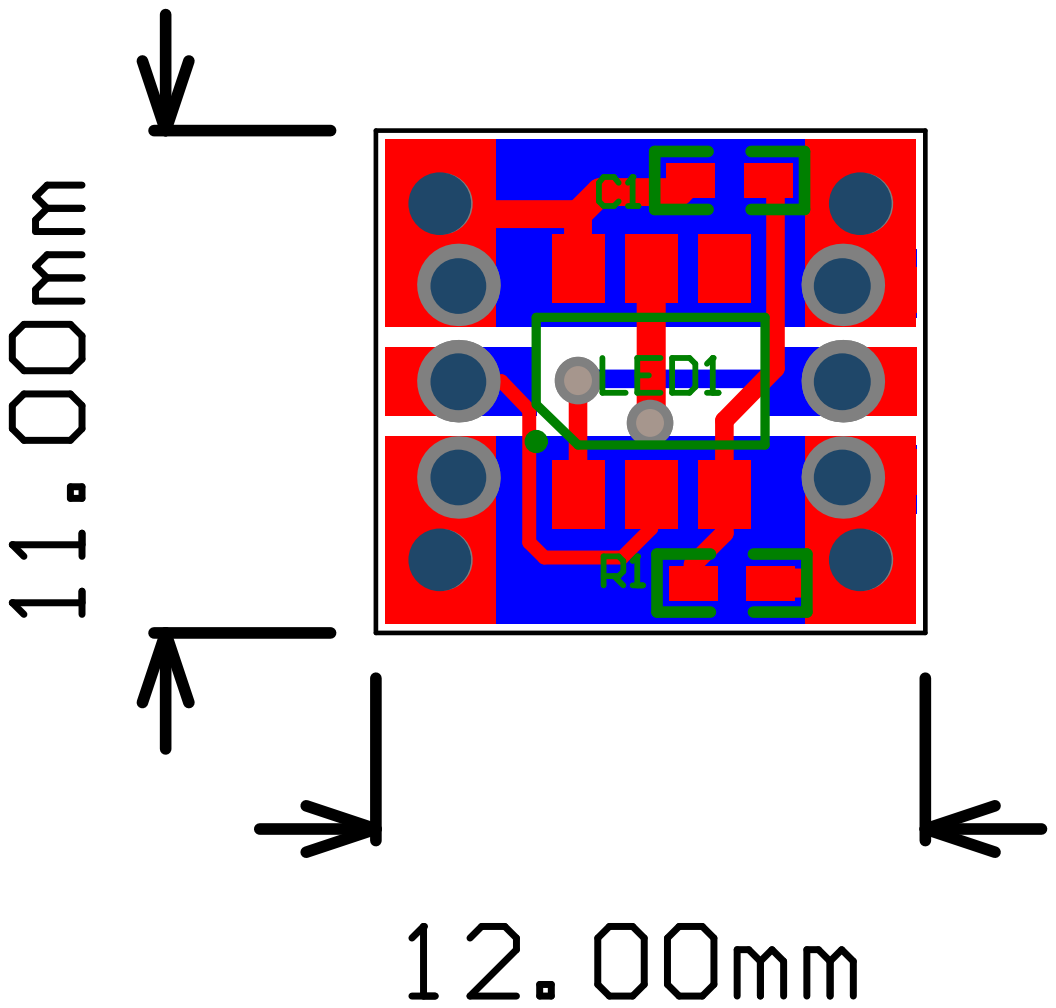
[picture p72: page 9]

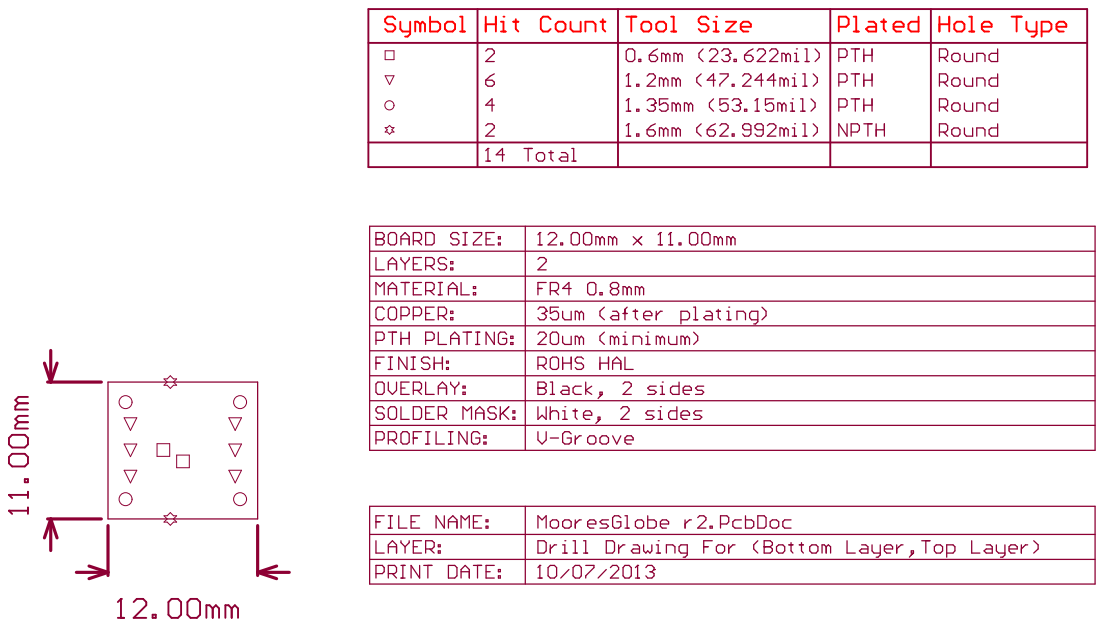
[picture p73: page 10]
