moorescloud/holiday-hardware/MooresGlobe r2a Panel.PDF

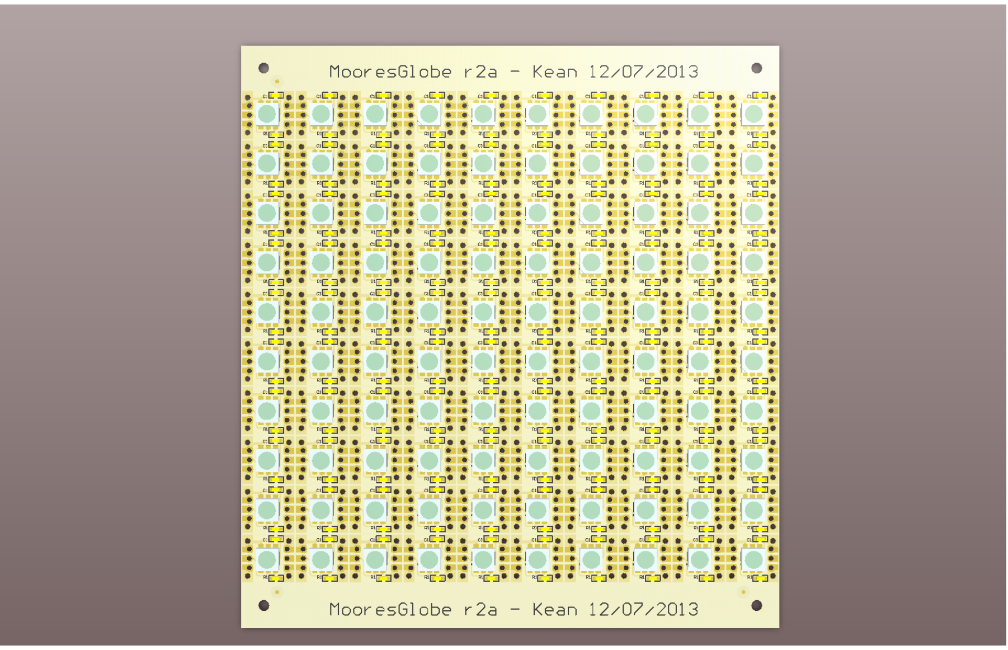
[picture p74: page 1]

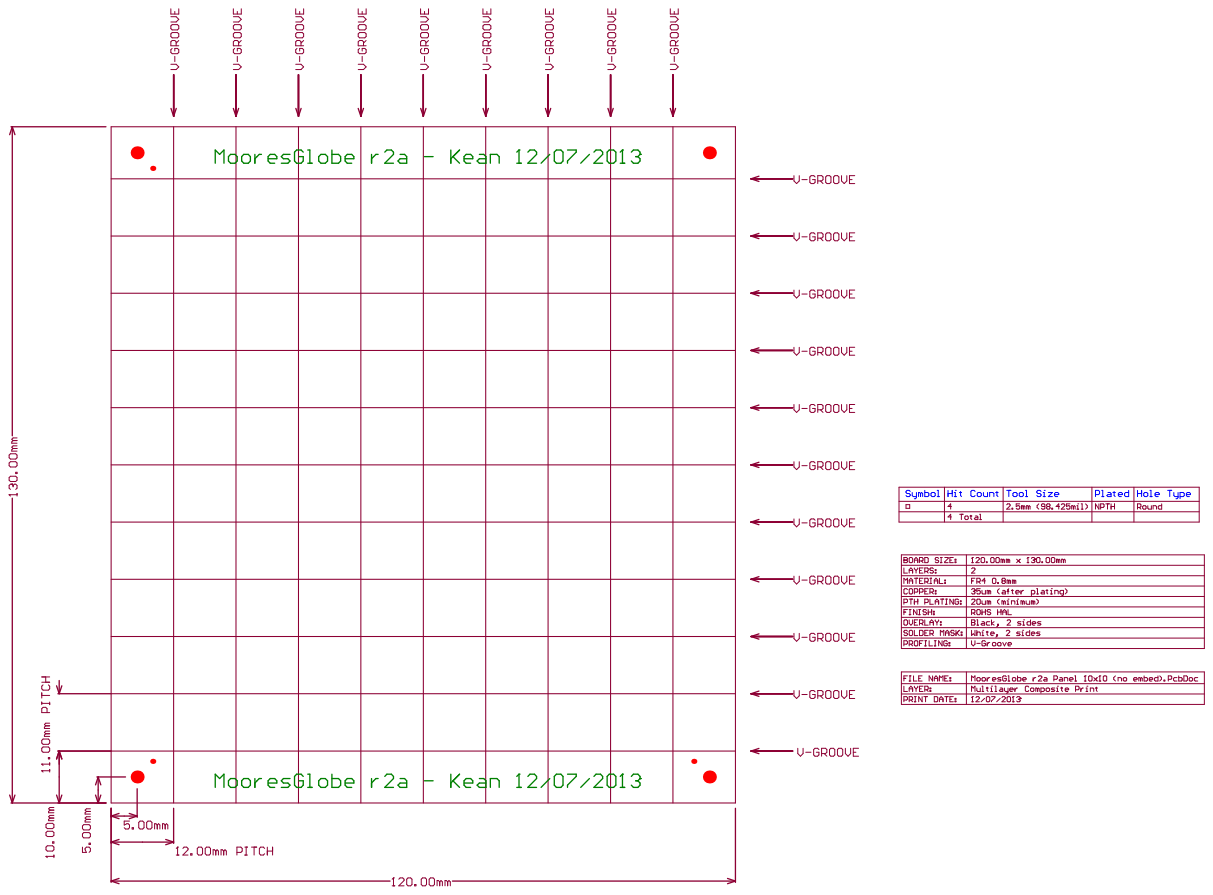
[picture p75: page 2]
