moorescloud/holiday-hardware/MooresGlobe r2a.PDF

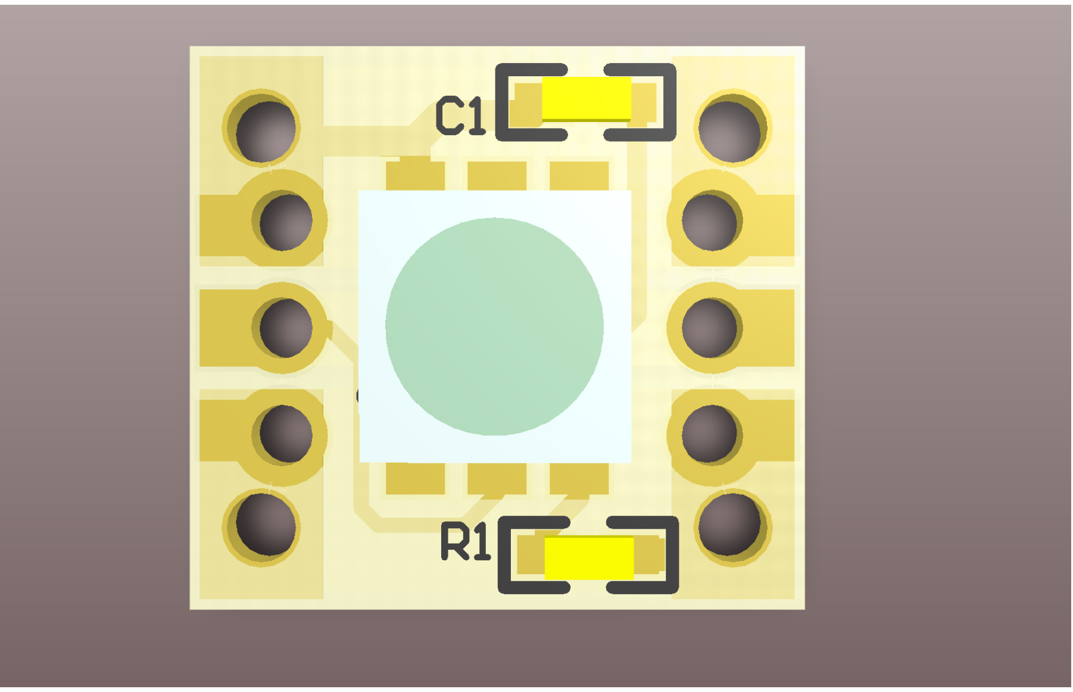
[picture p76: page 1]

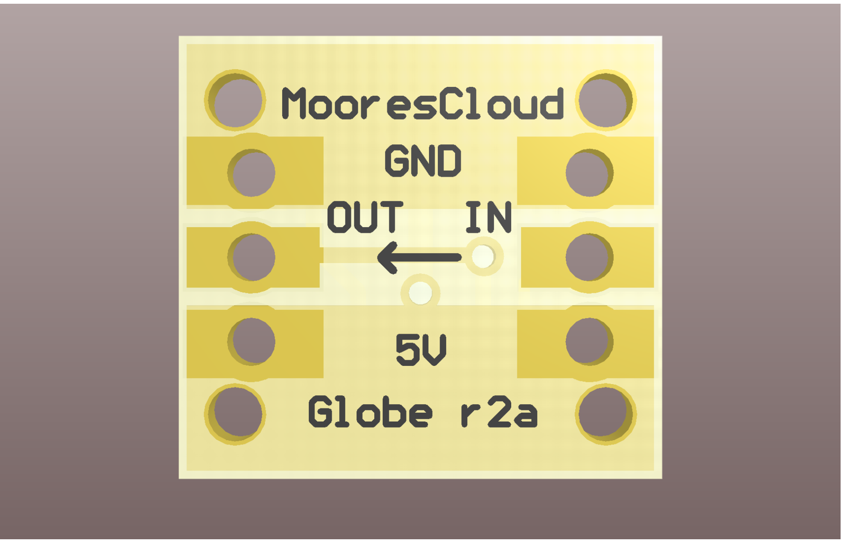
[picture p77: page 2]

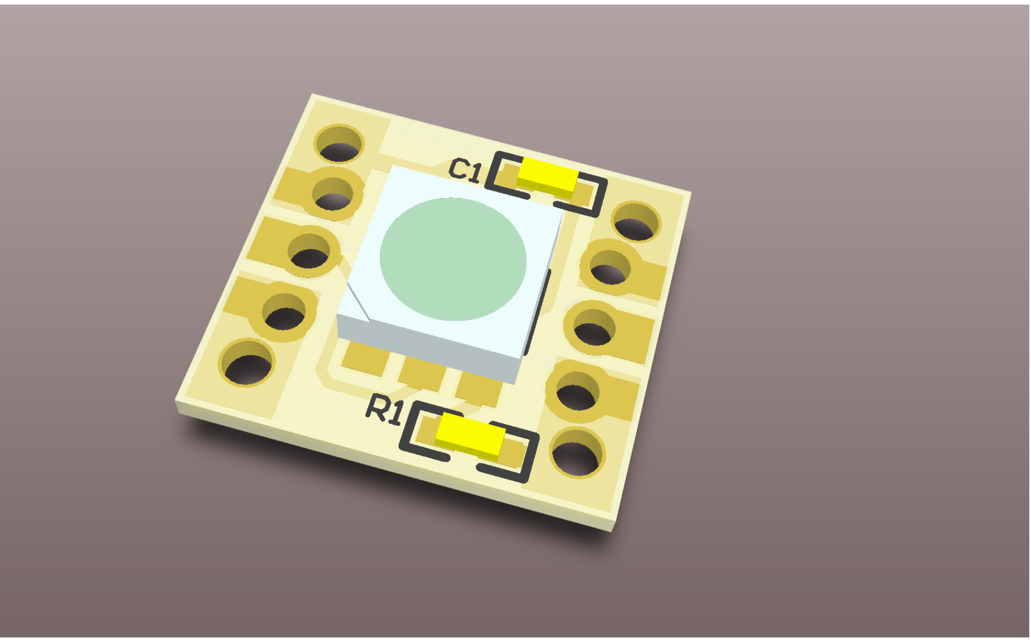
[picture p78: page 3]

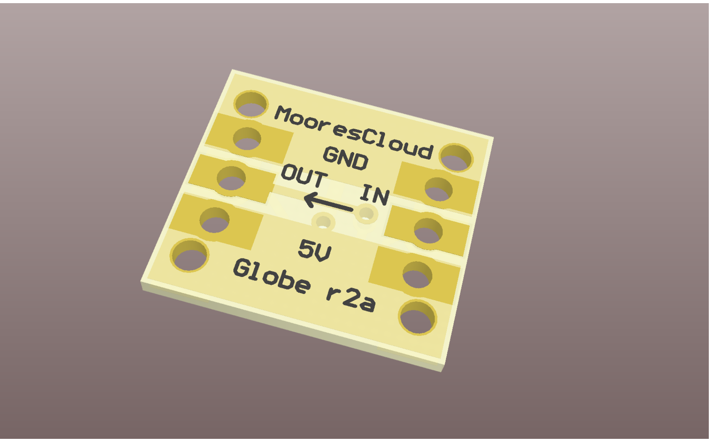
[picture p79: page 4]


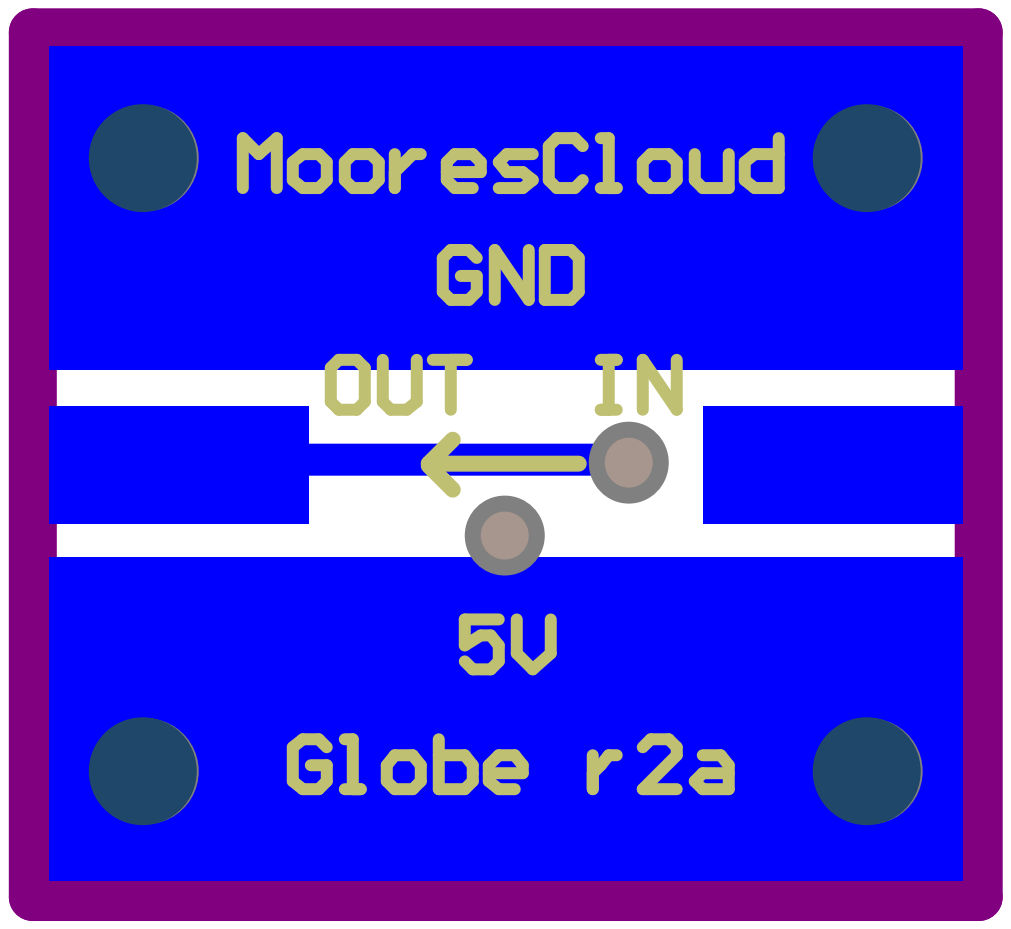
[picture p80: page 6]

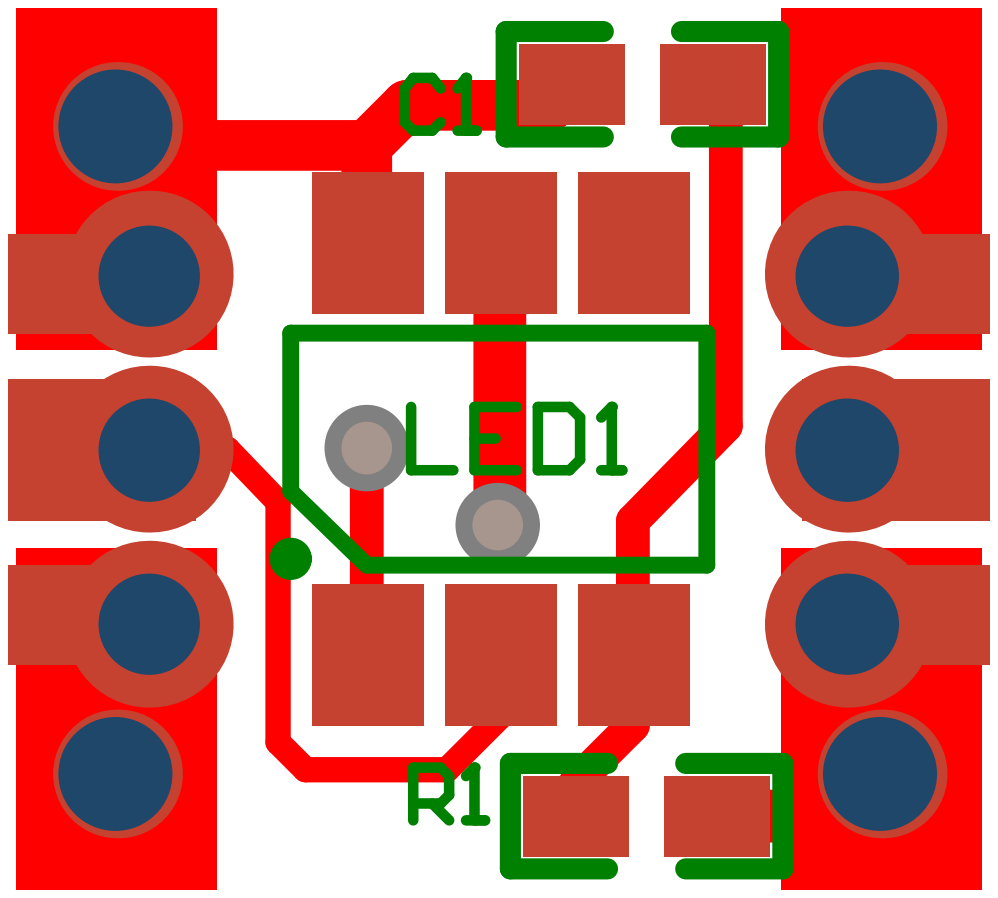
[picture p81: page 7]

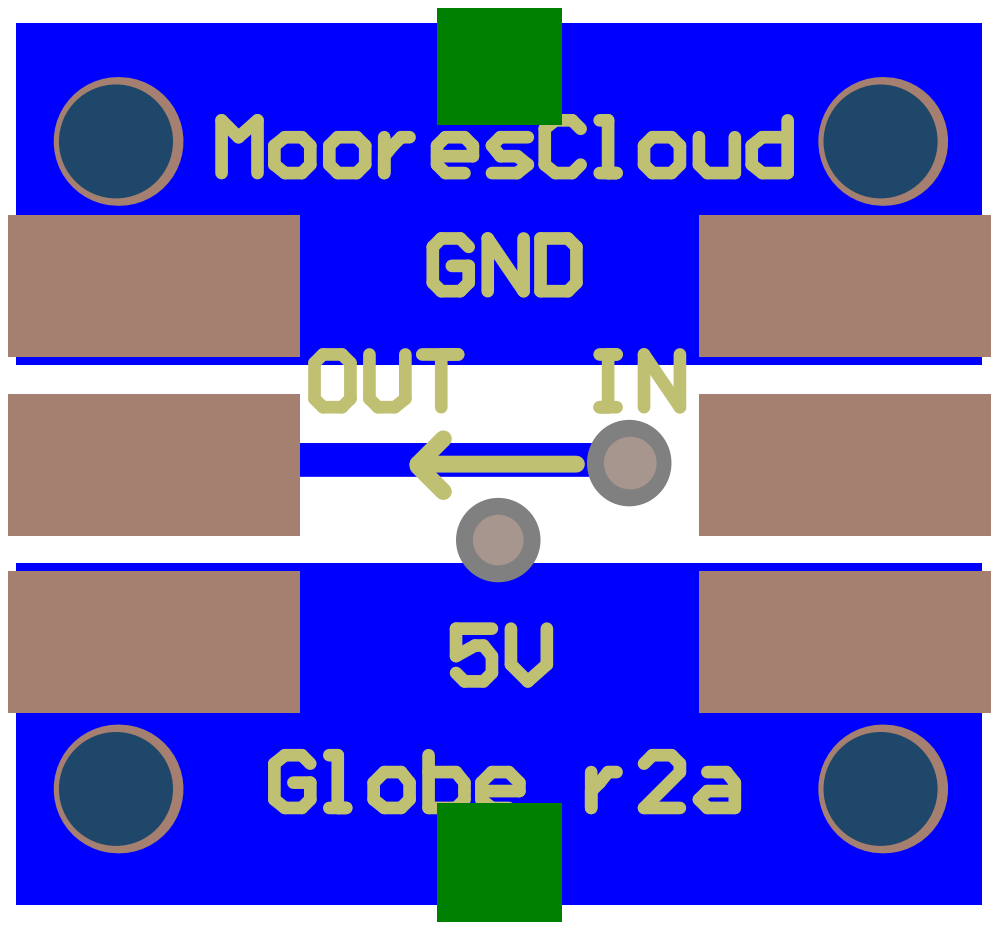
[picture p82: page 8]


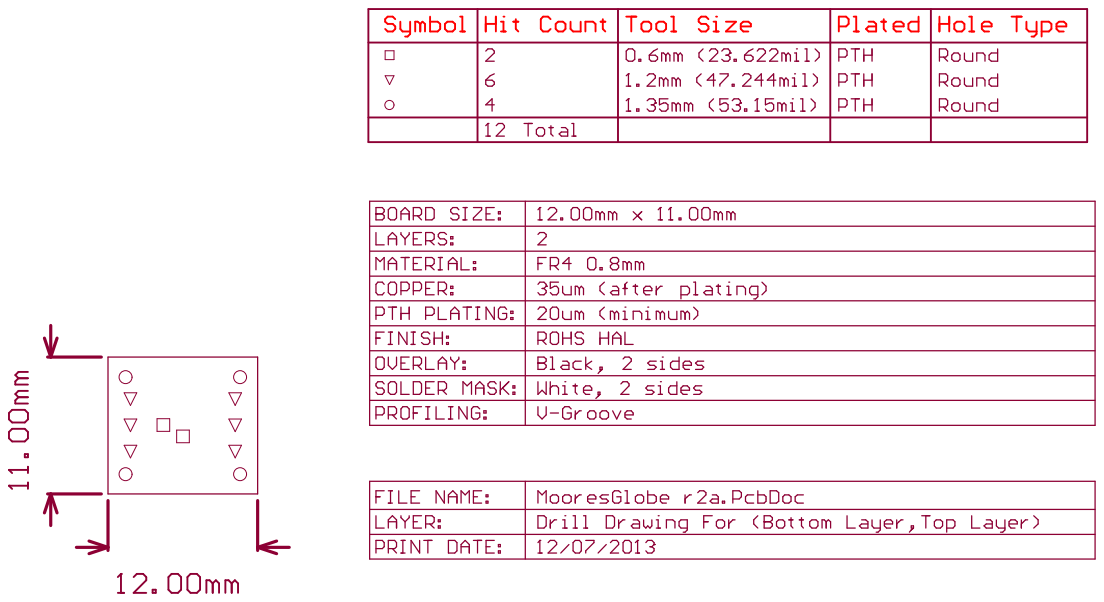
[picture p83: page 10]
