moorescloud/holiday-hardware/MooresGlobe r2b Panel.PDF

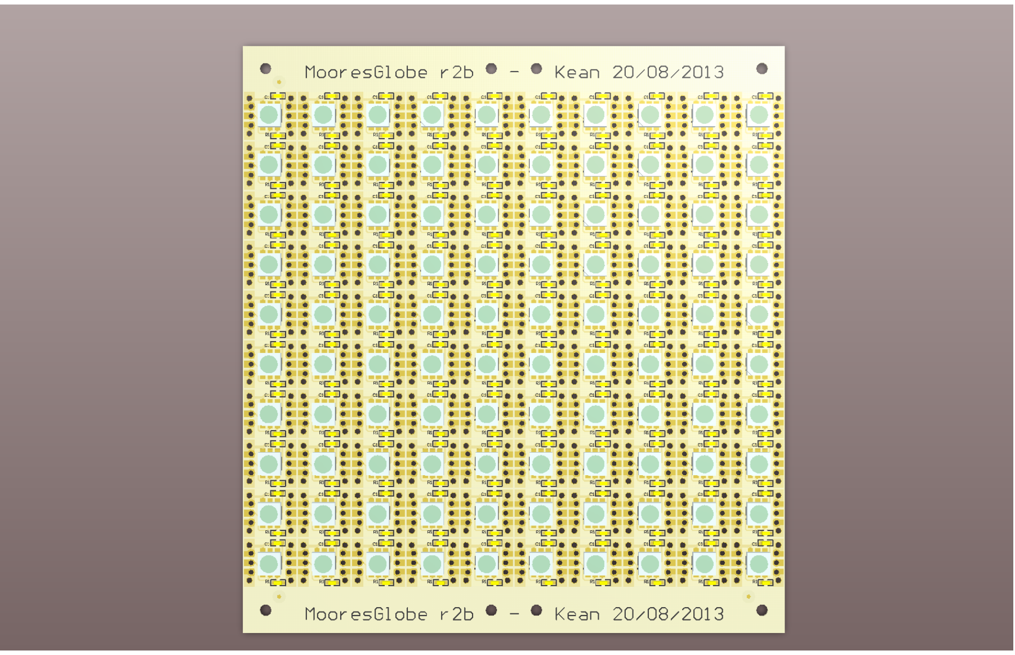
[picture p84: page 1]

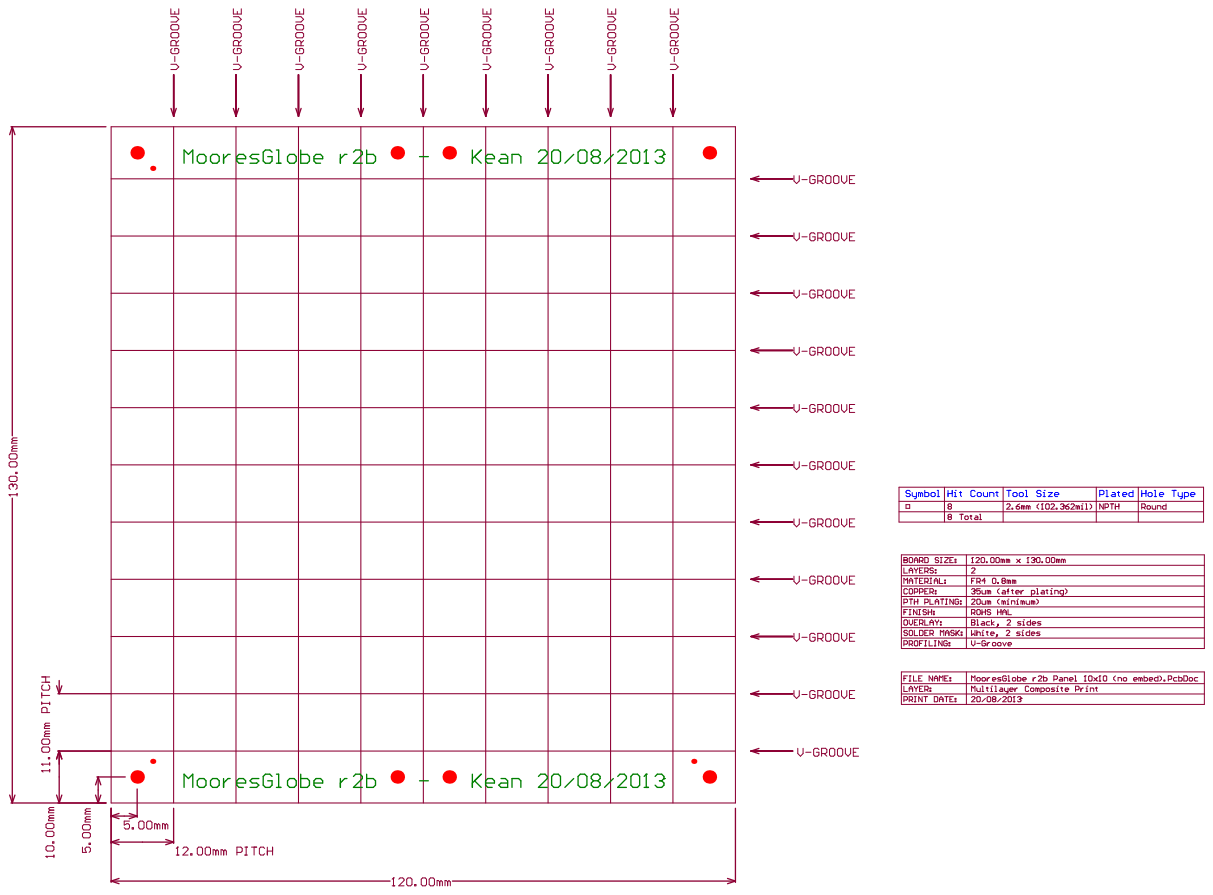
[picture p85: page 2]
