moorescloud/holiday-hardware/MooresGlobe r2b.PDF

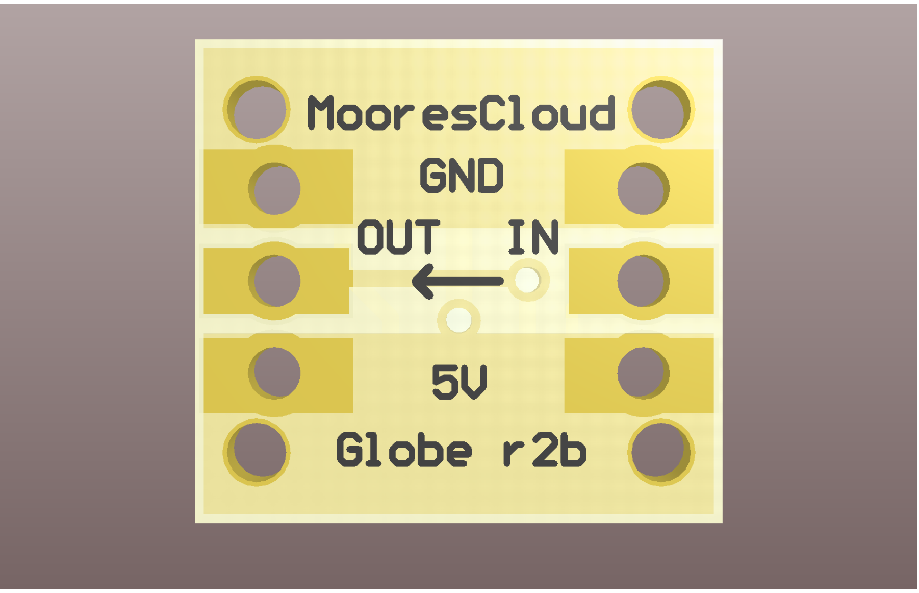
[picture p86: page 2]


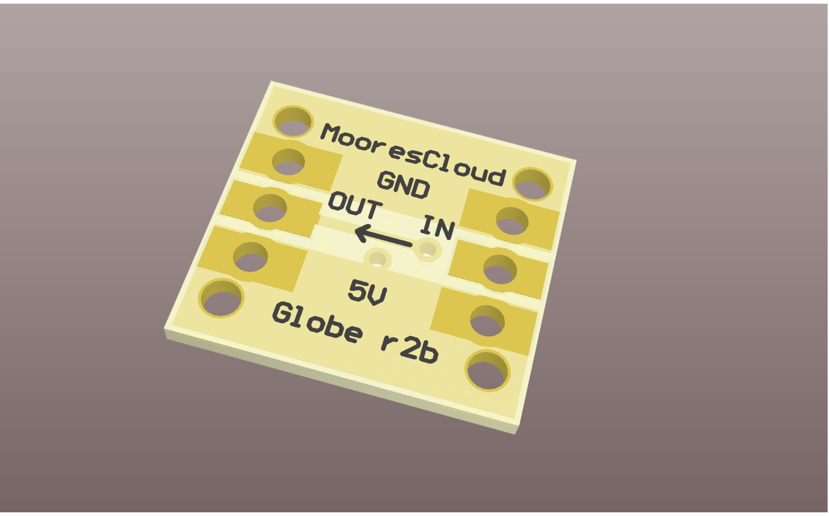
[picture p87: page 4]


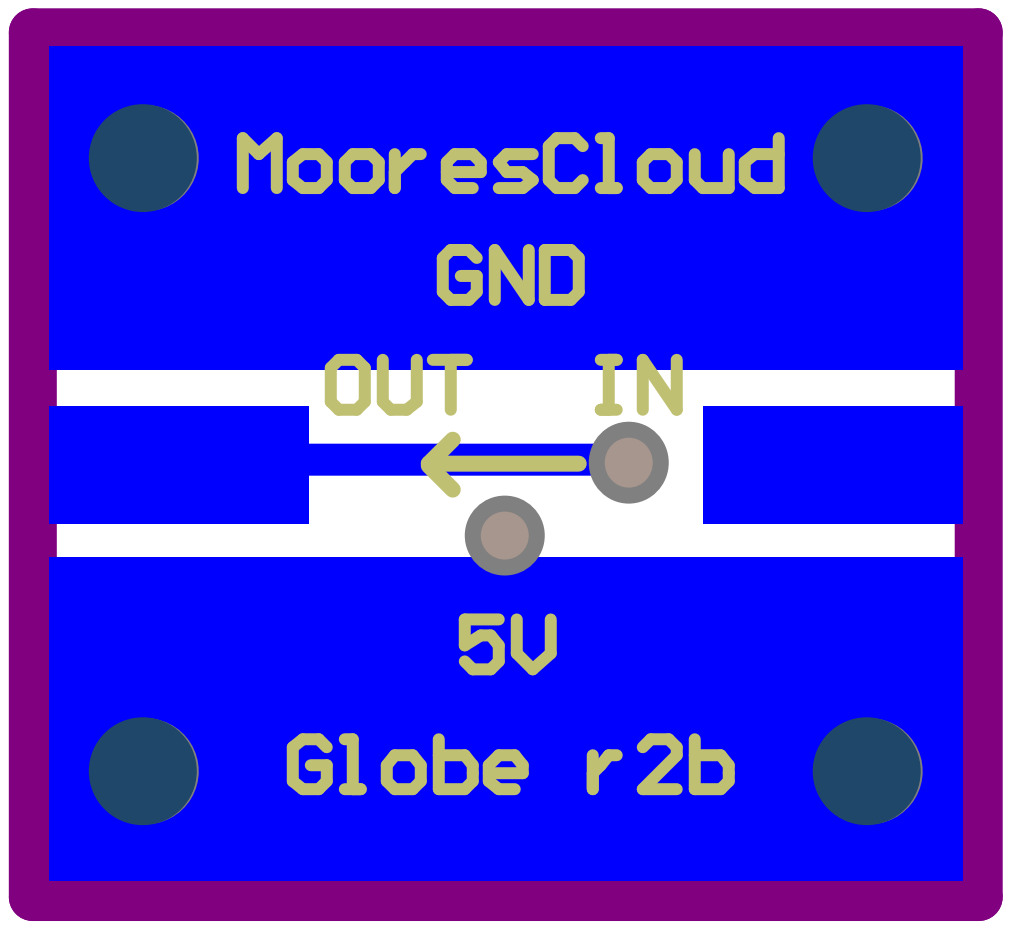
[picture p88: page 6]


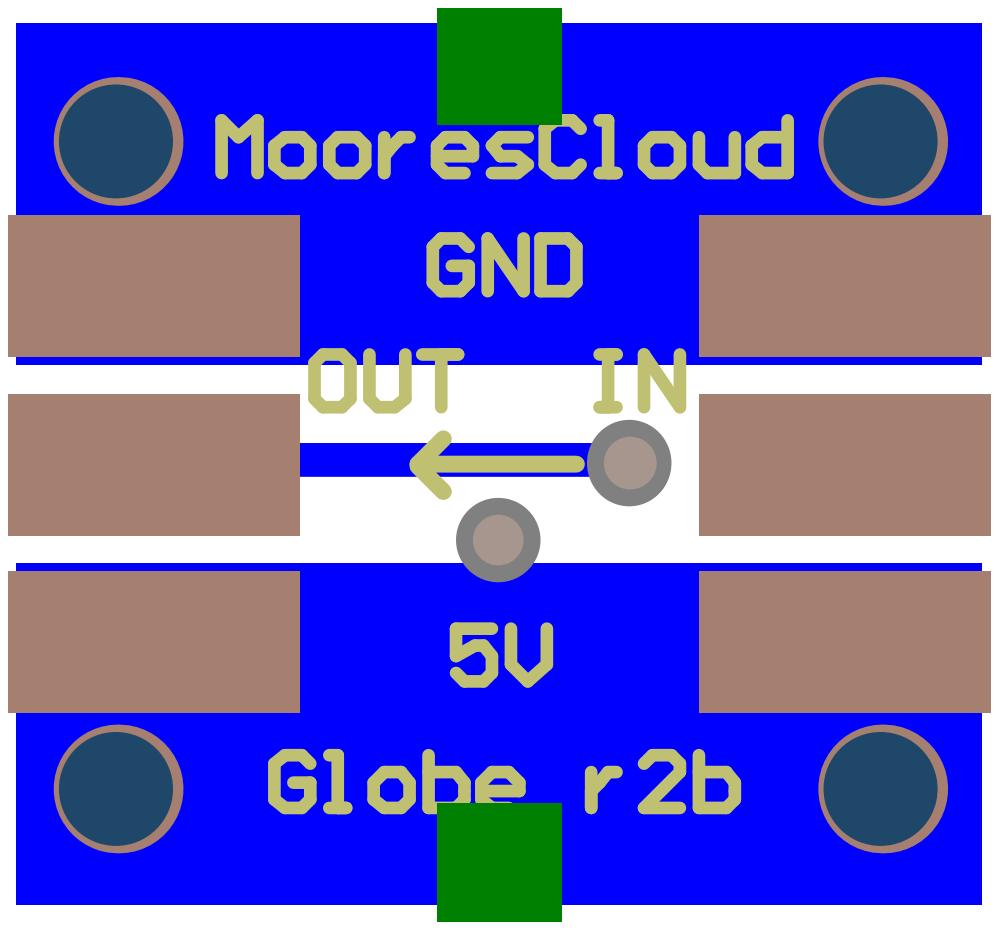
[picture p89: page 8]


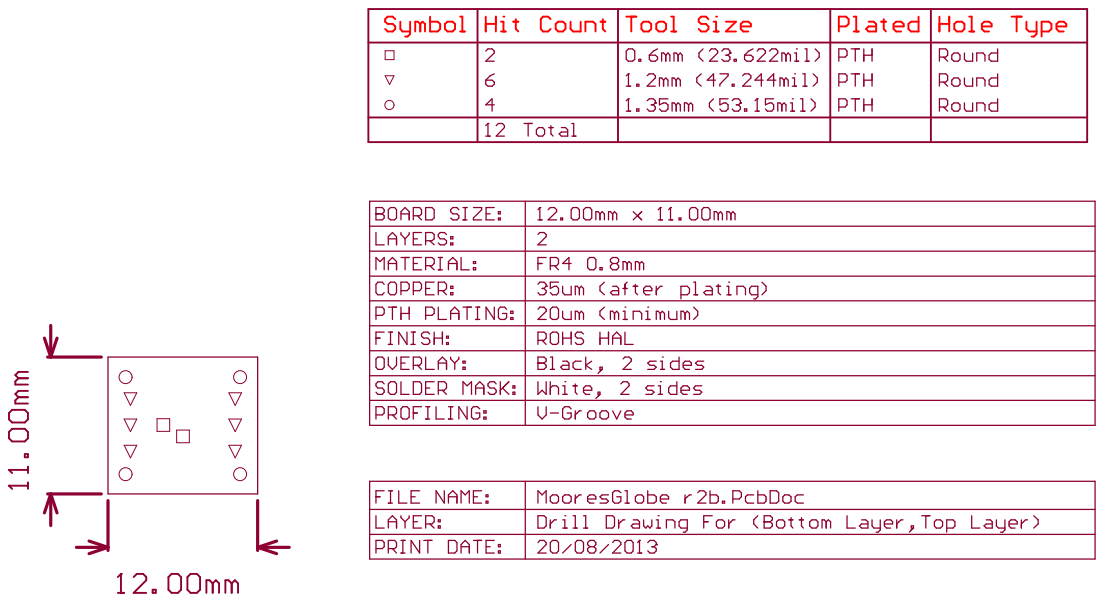
[picture p90: page 10]
