moorescloud/holiday-hardware/MooresGlobe r3 Panel.PDF

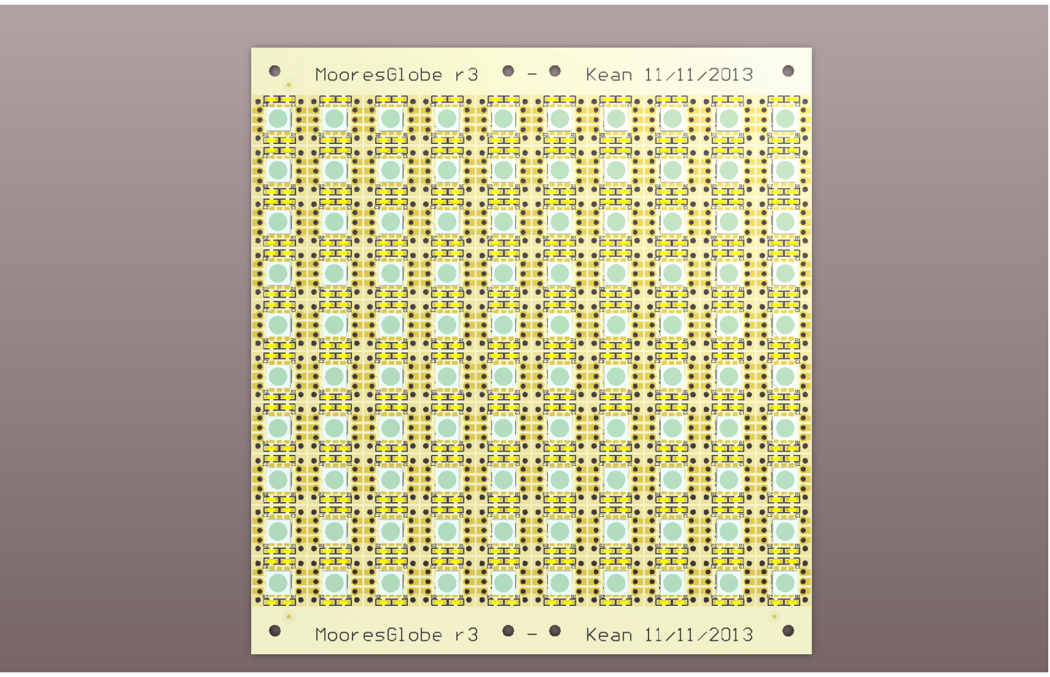
[picture p91: page 1]

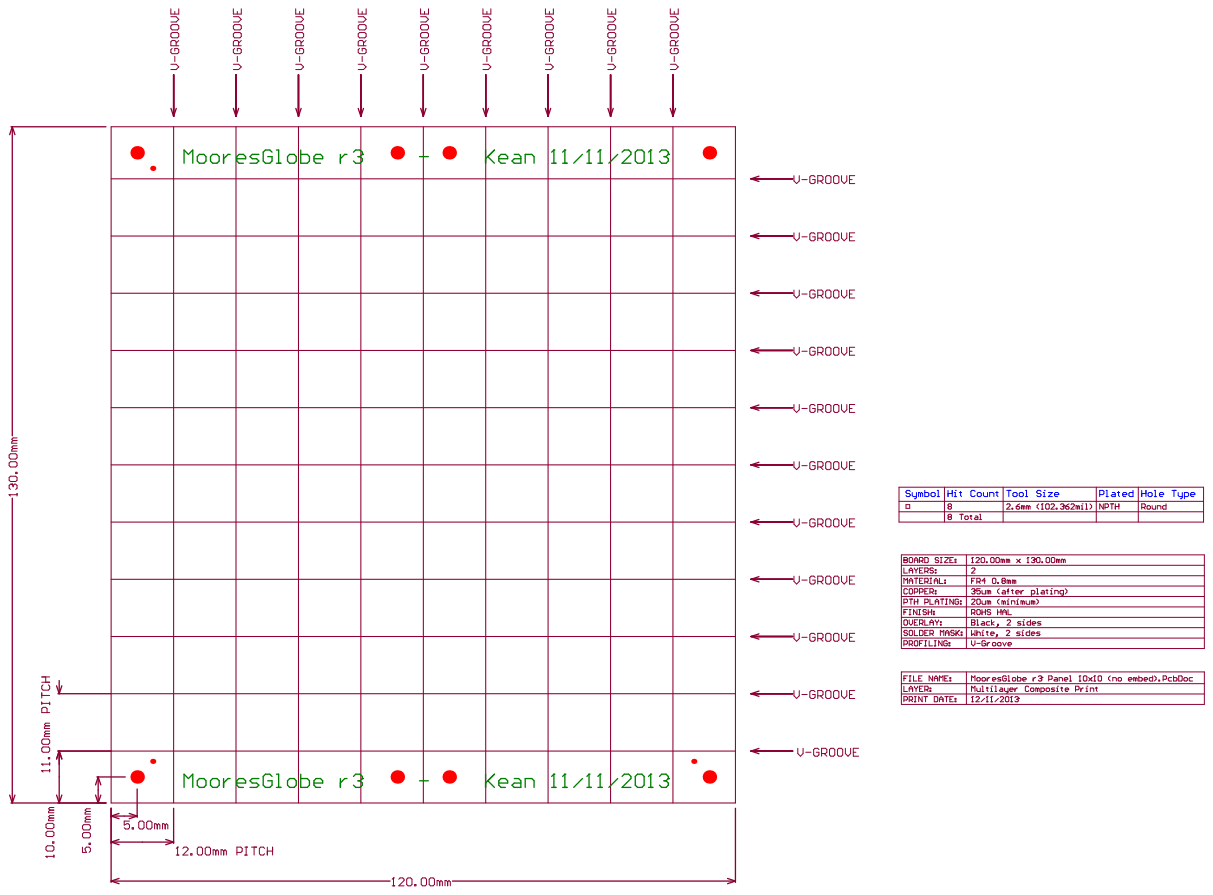
[picture p92: page 2]
