moorescloud/holiday-hardware/MooresGlobe r3.PDF

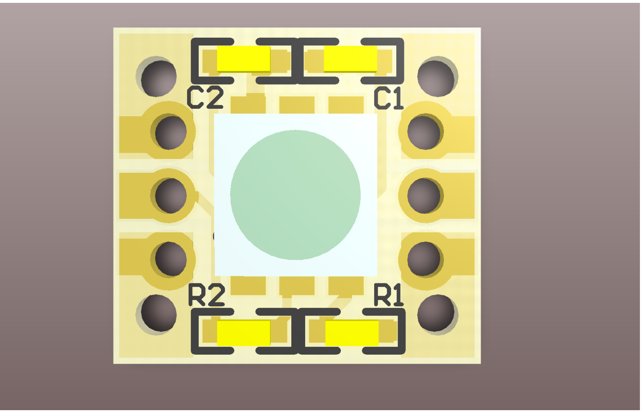
[picture p93: page 1]

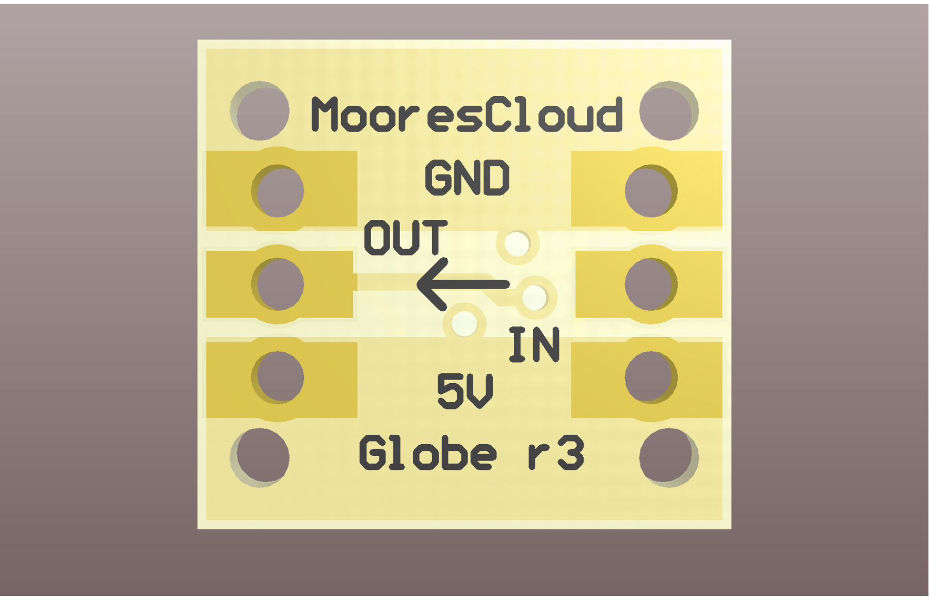
[picture p94: page 2]

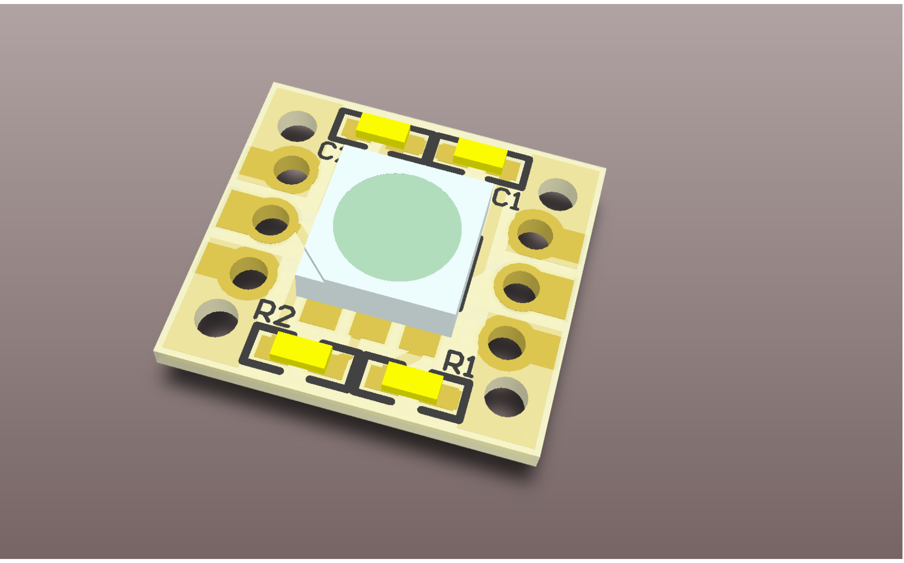
[picture p95: page 3]

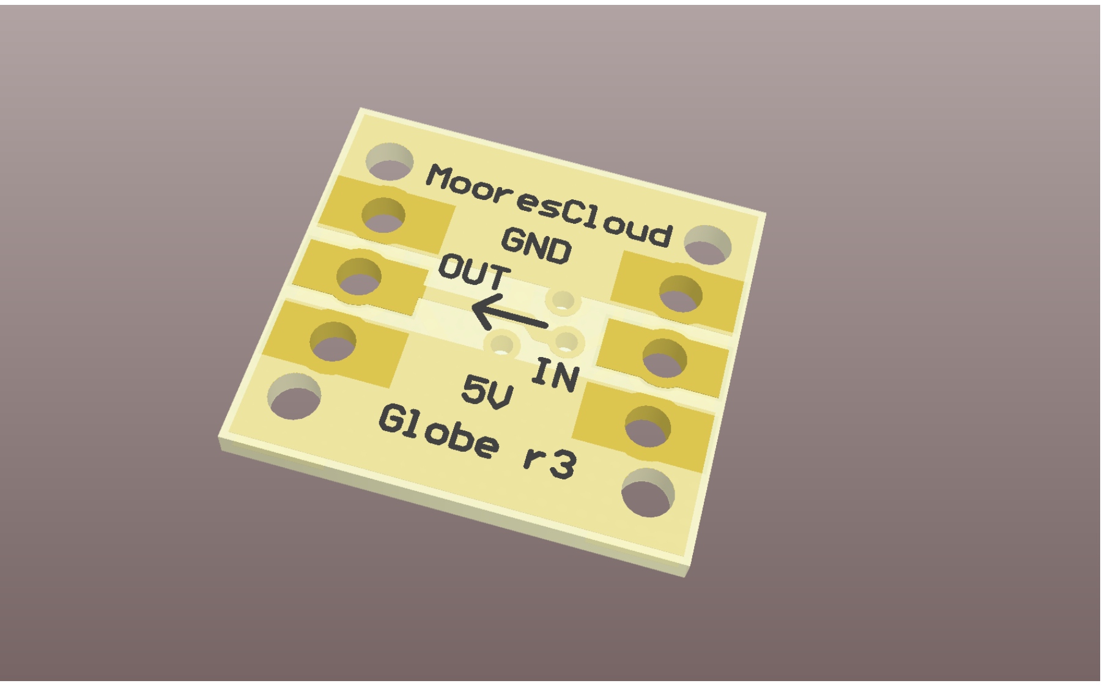
[picture p96: page 4]

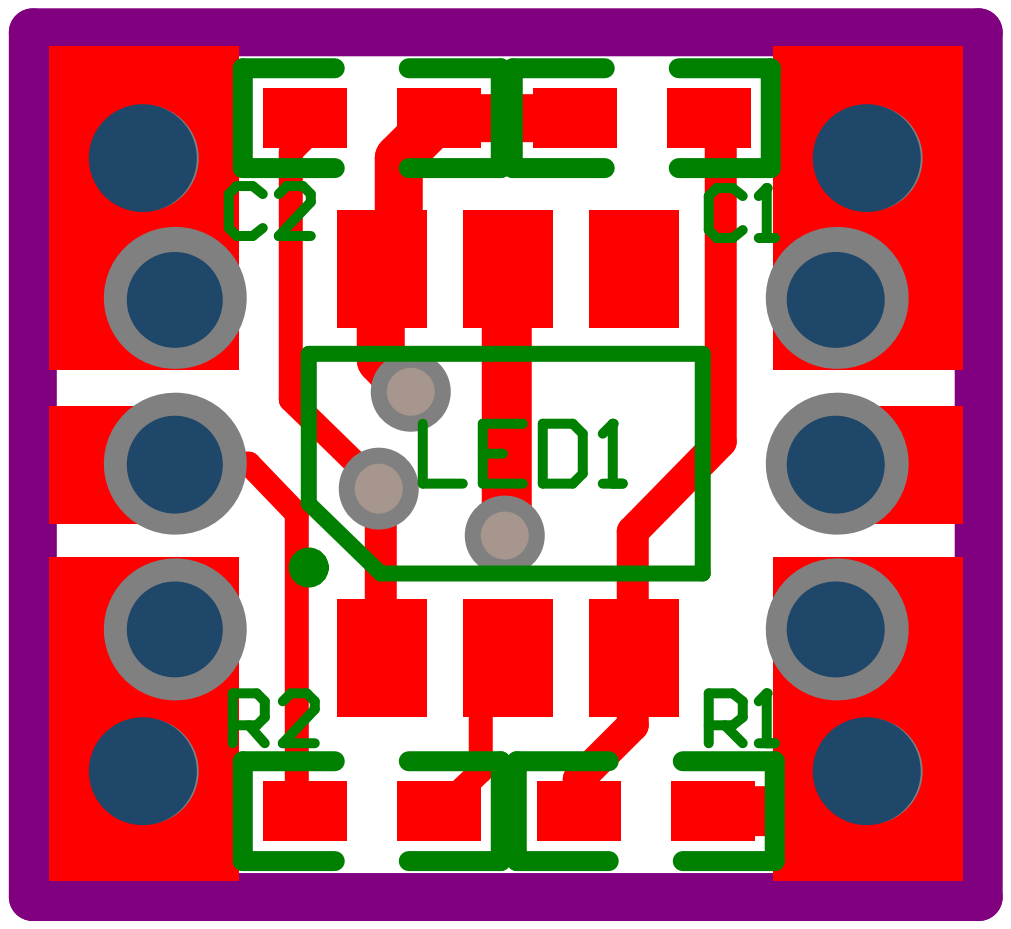
[picture p97: page 5]

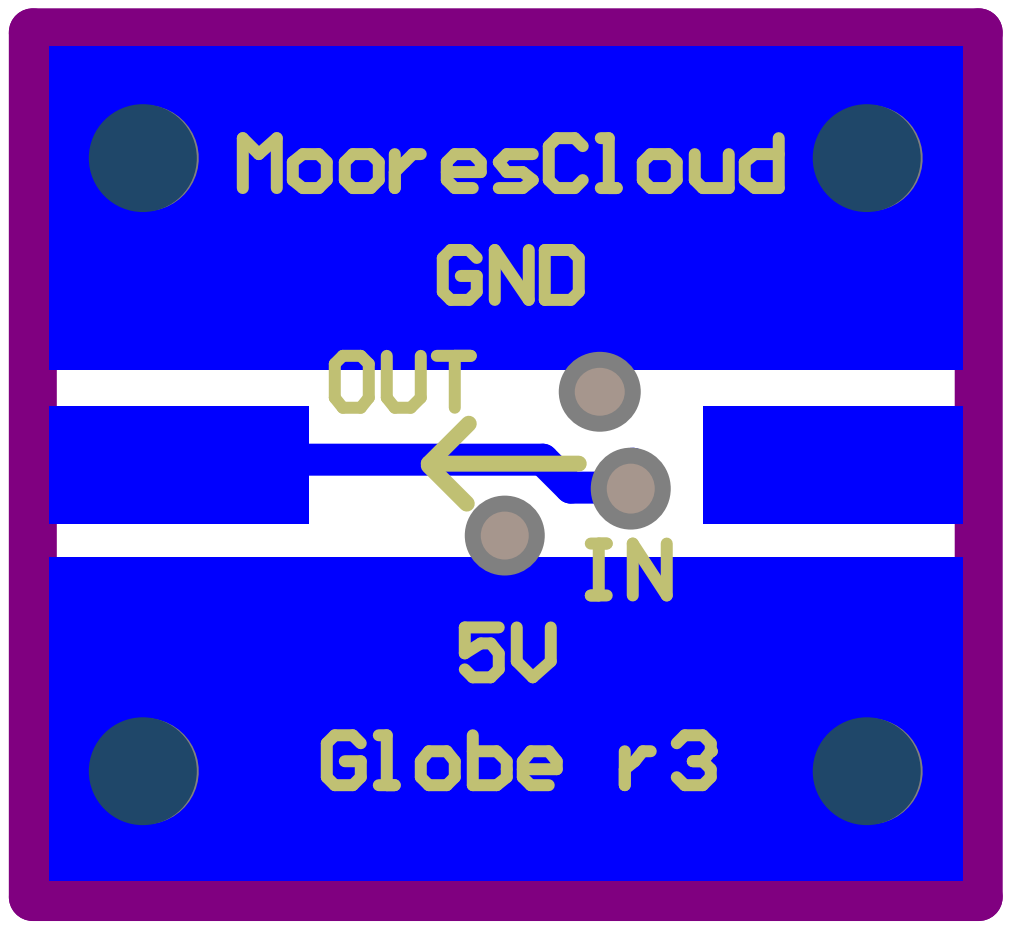
[picture p98: page 6]

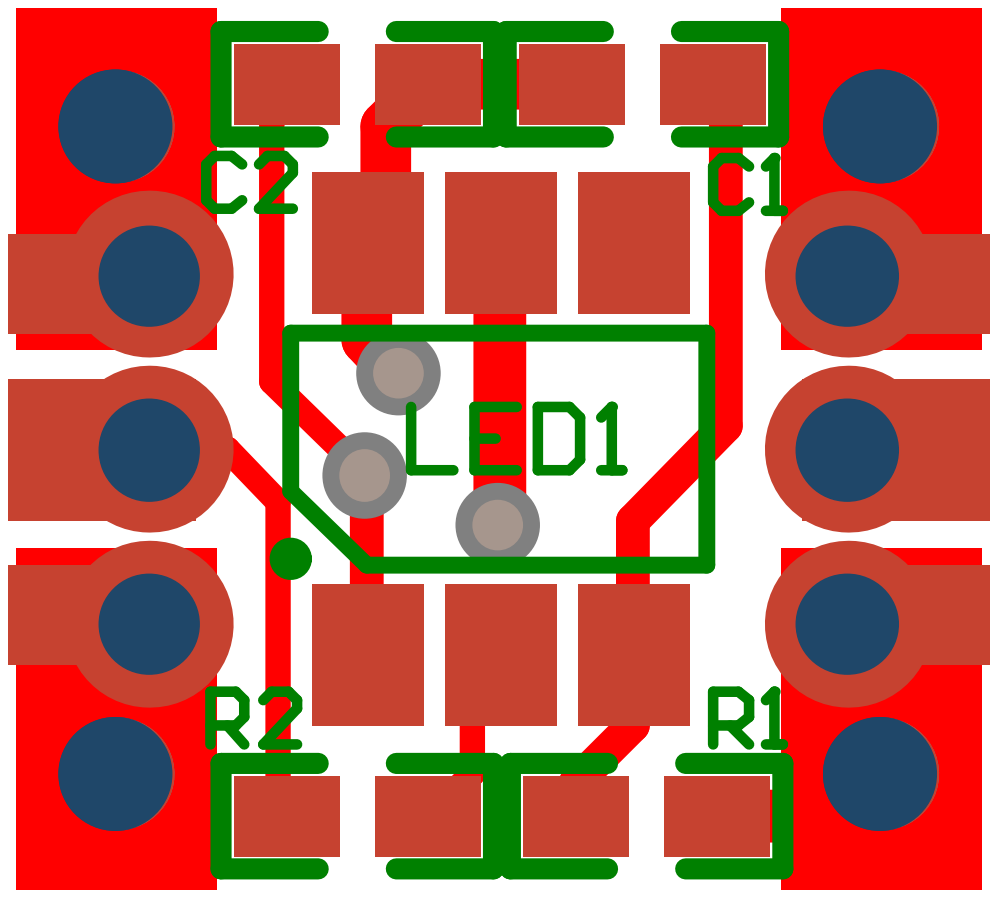
[picture p99: page 7]

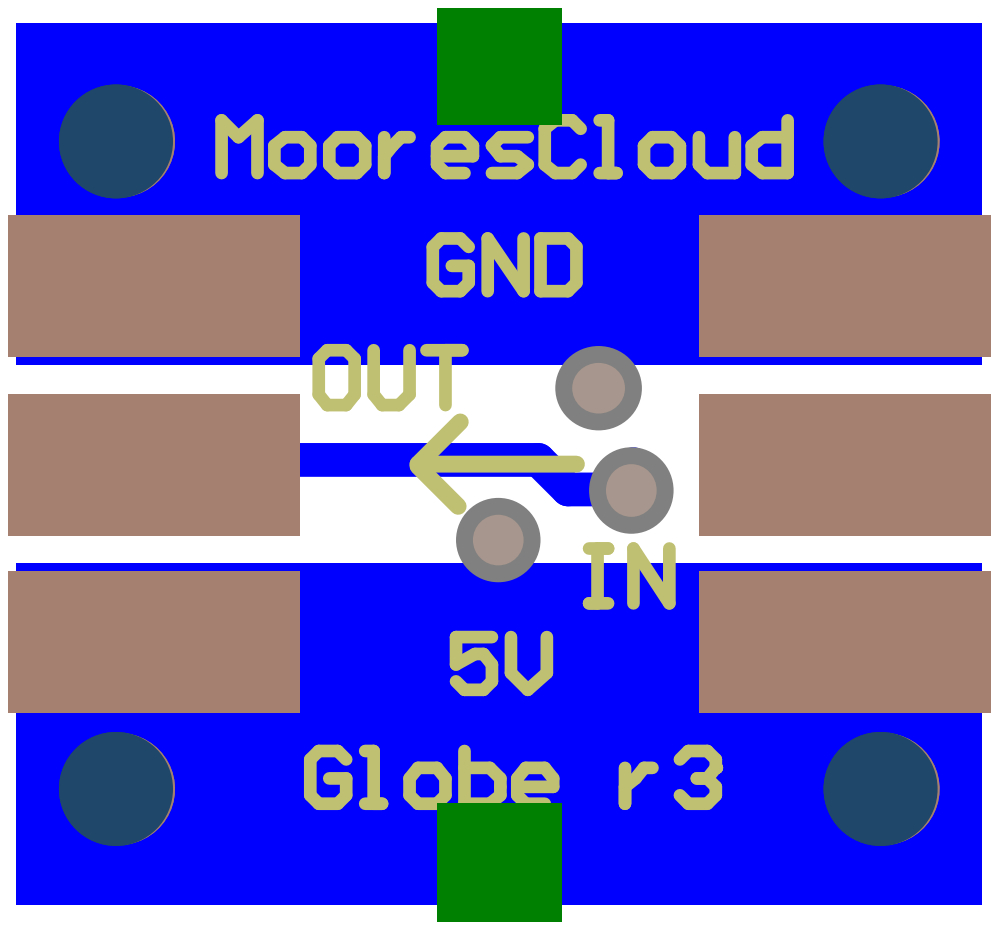
[picture p100: page 8]

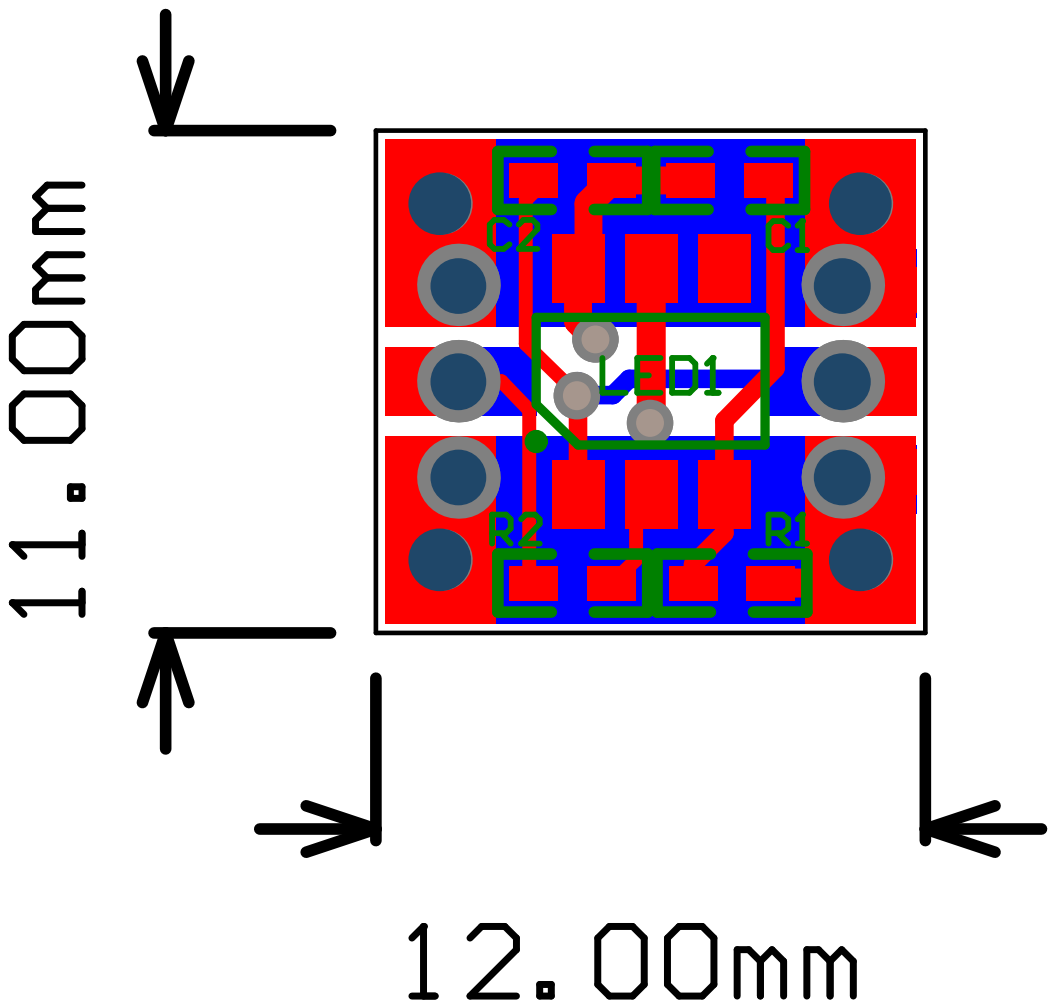
[picture p101: page 9]

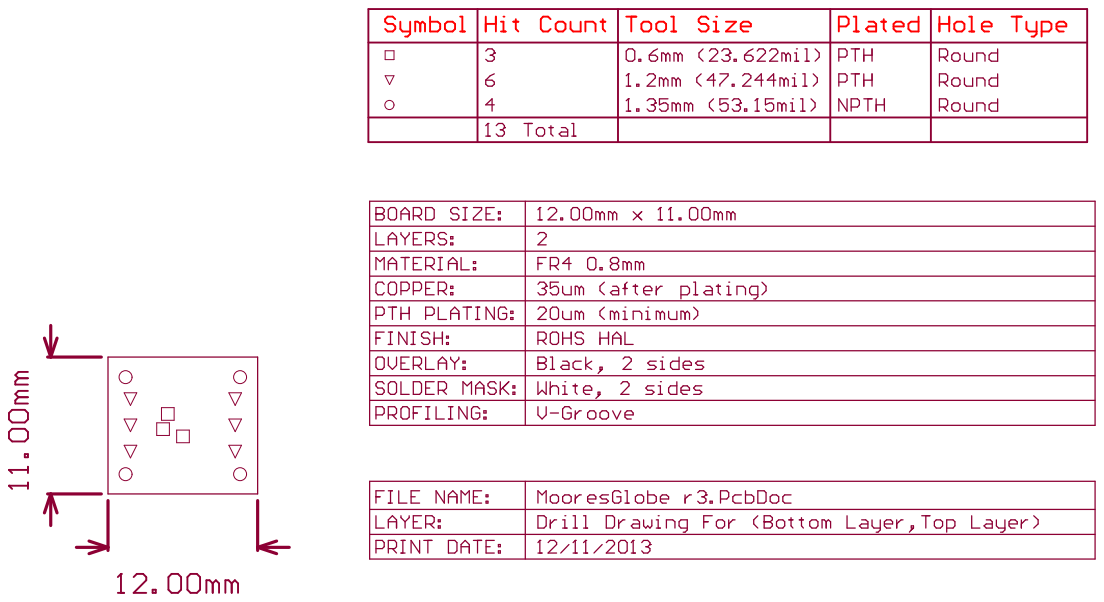
[picture p102: page 10]
