moorescloud/holiday-hardware/MooresGlobe r4 Panel.PDF

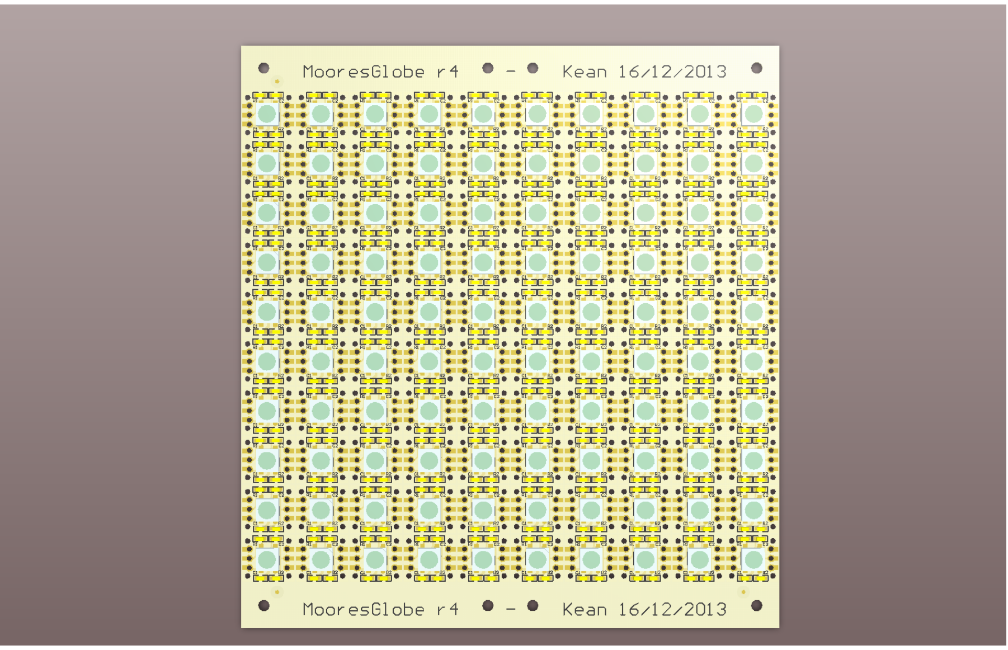
[picture p103: page 1]

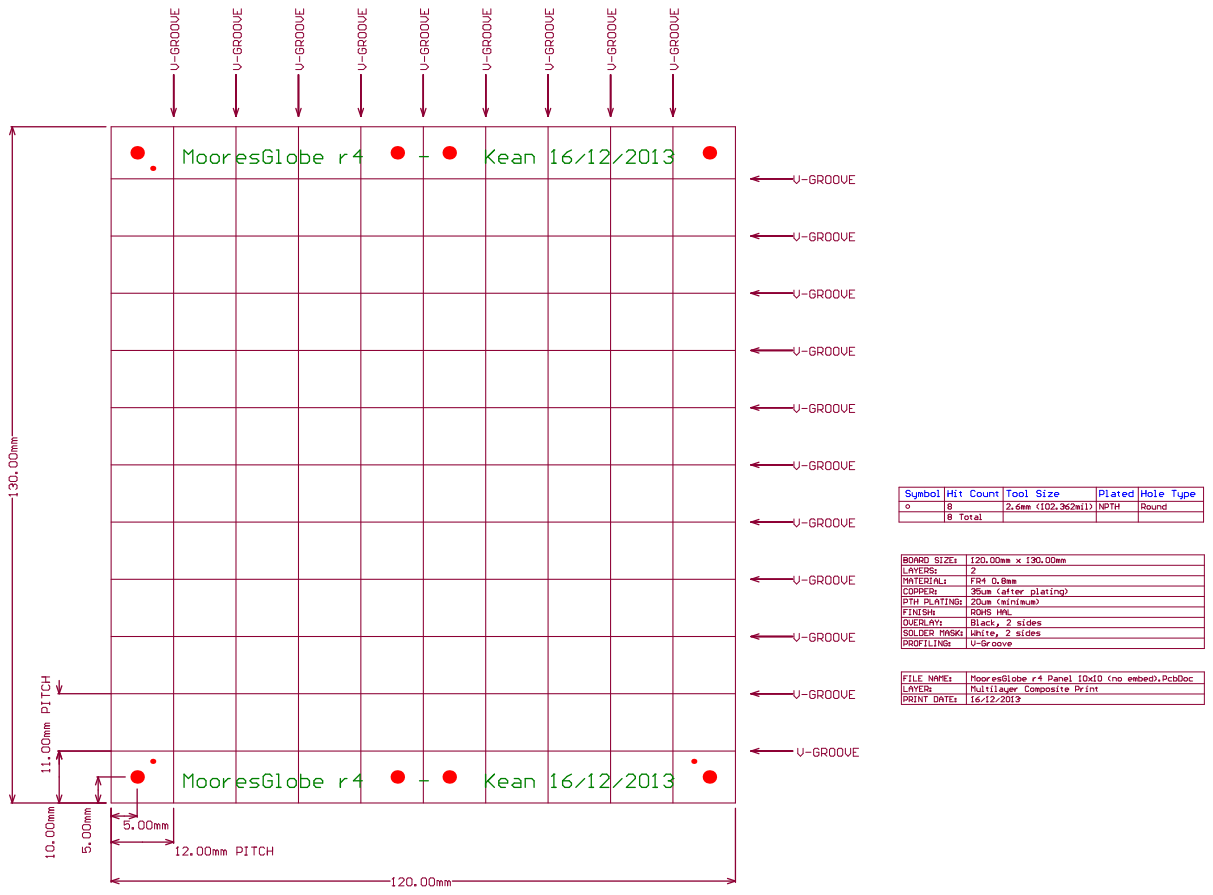
[picture p104: page 2]
