moorescloud/holiday-hardware/MooresGlobe r4.PDF

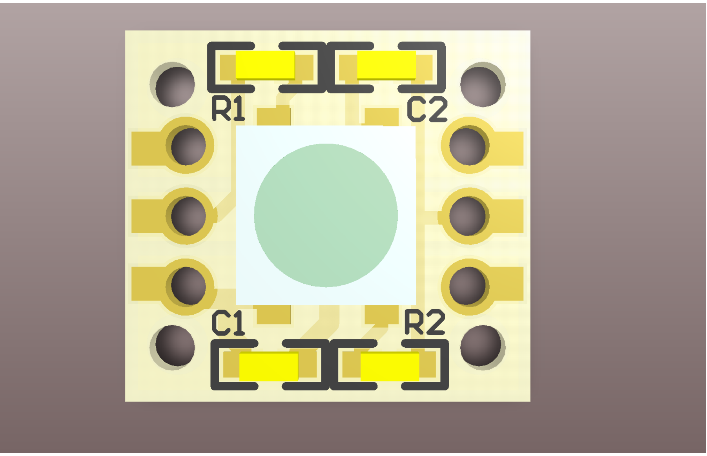
[picture p105: page 1]

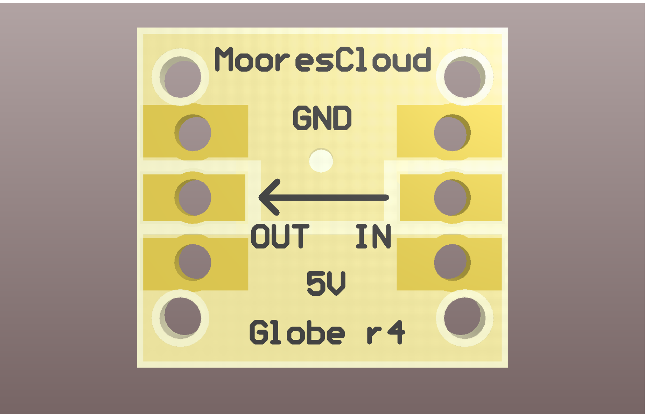
[picture p106: page 2]

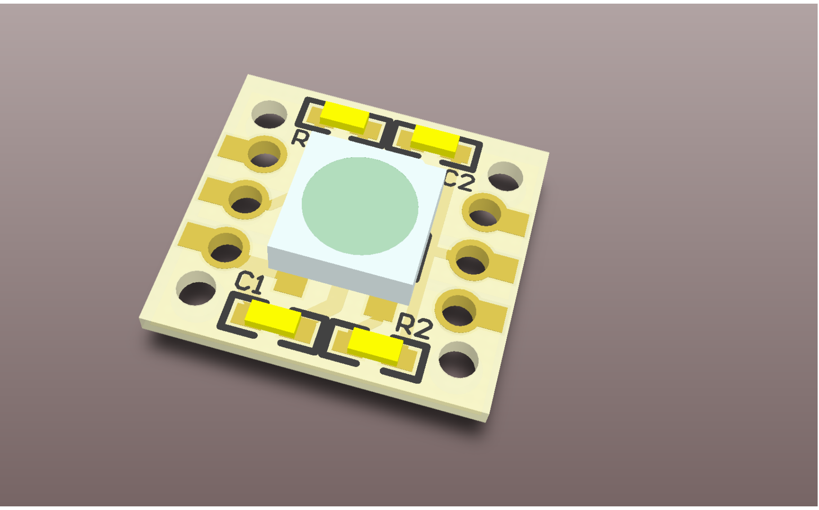
[picture p107: page 3]

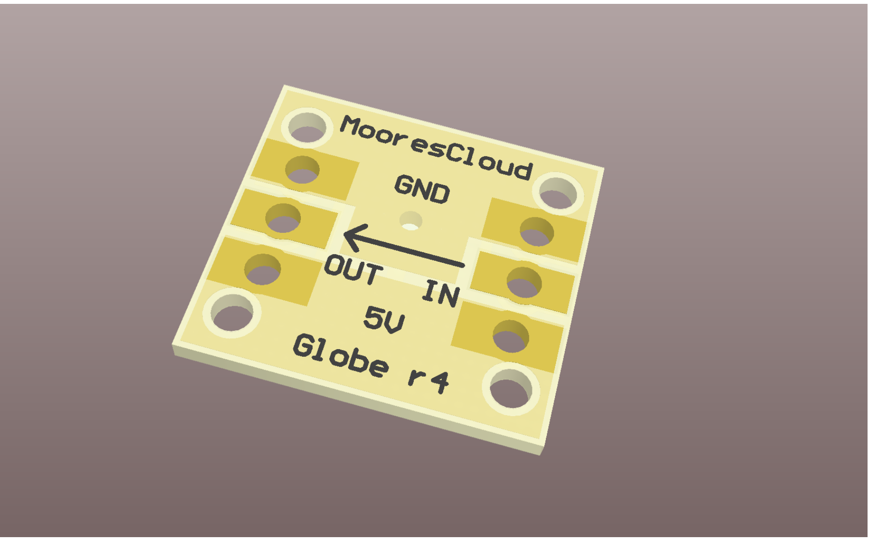
[picture p108: page 4]

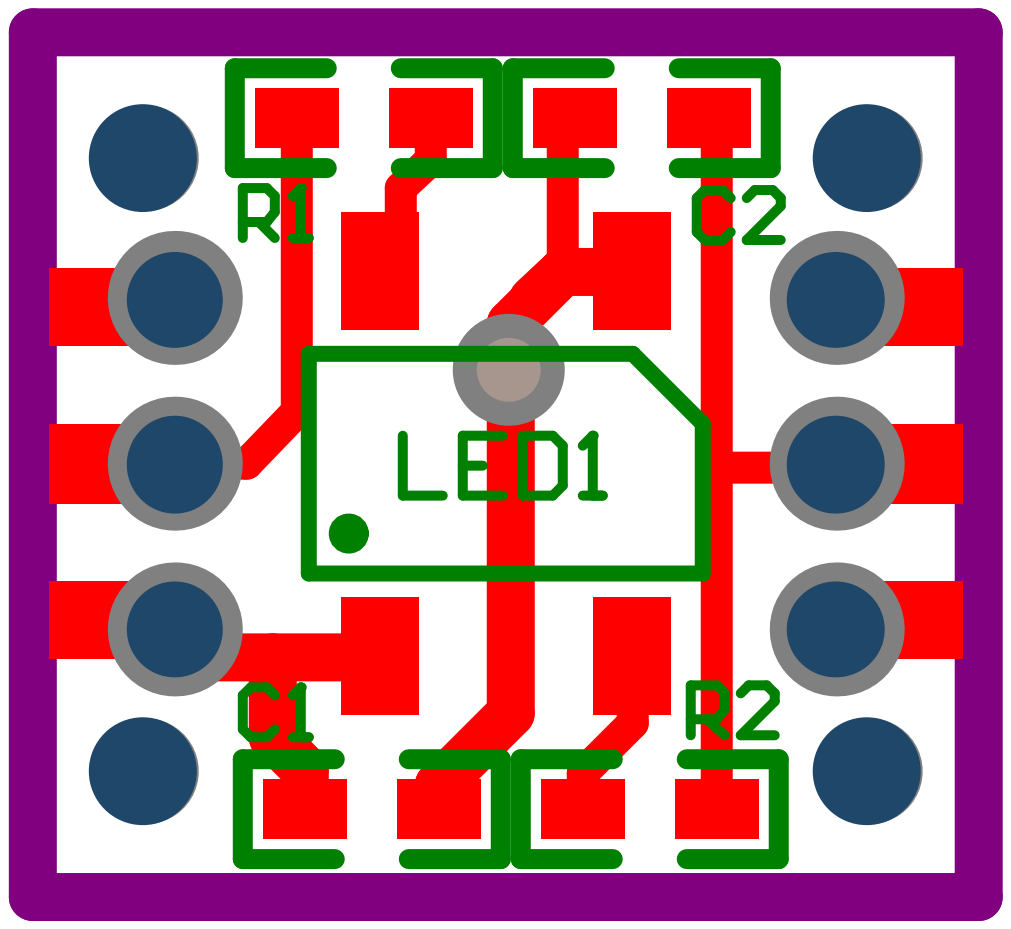
[picture p109: page 5]

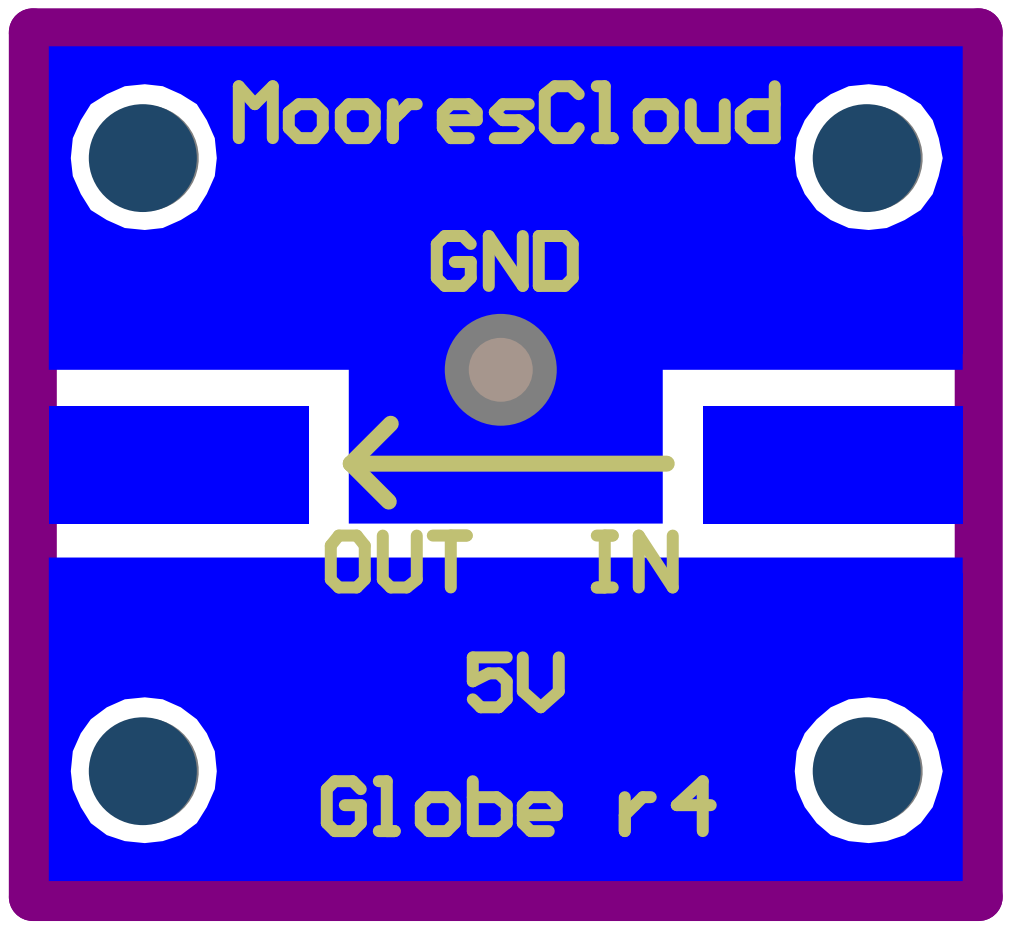
[picture p110: page 6]

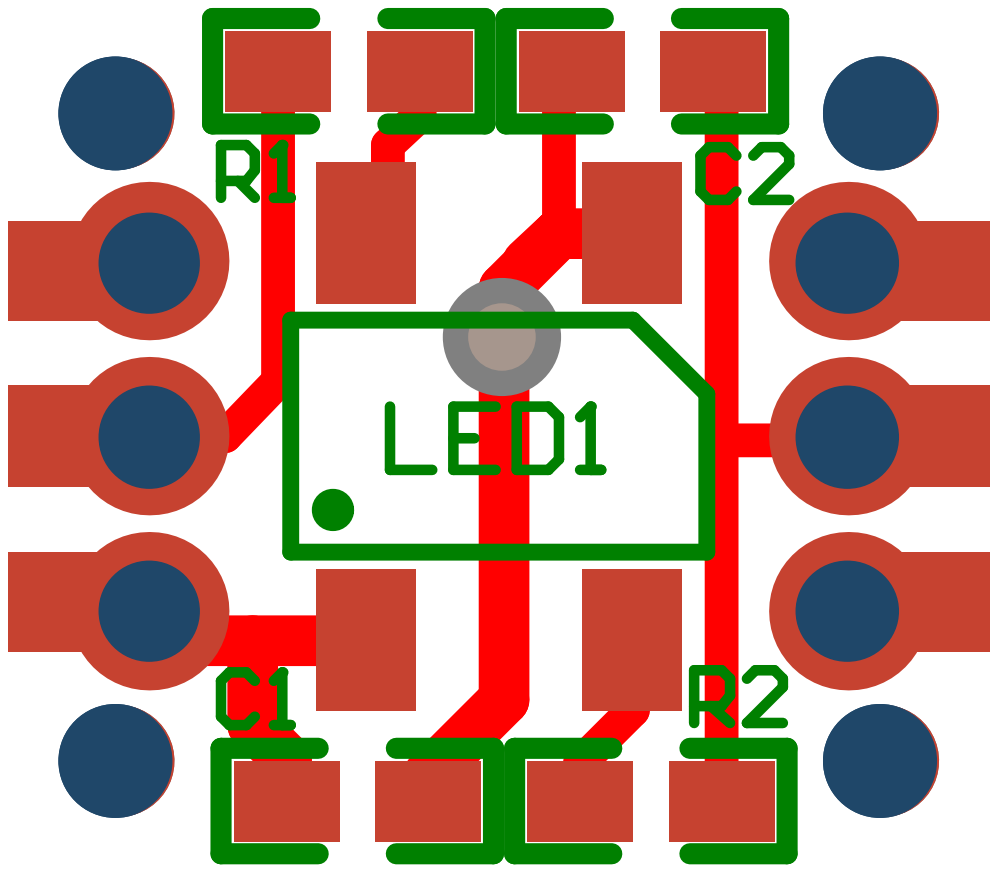
[picture p111: page 7]

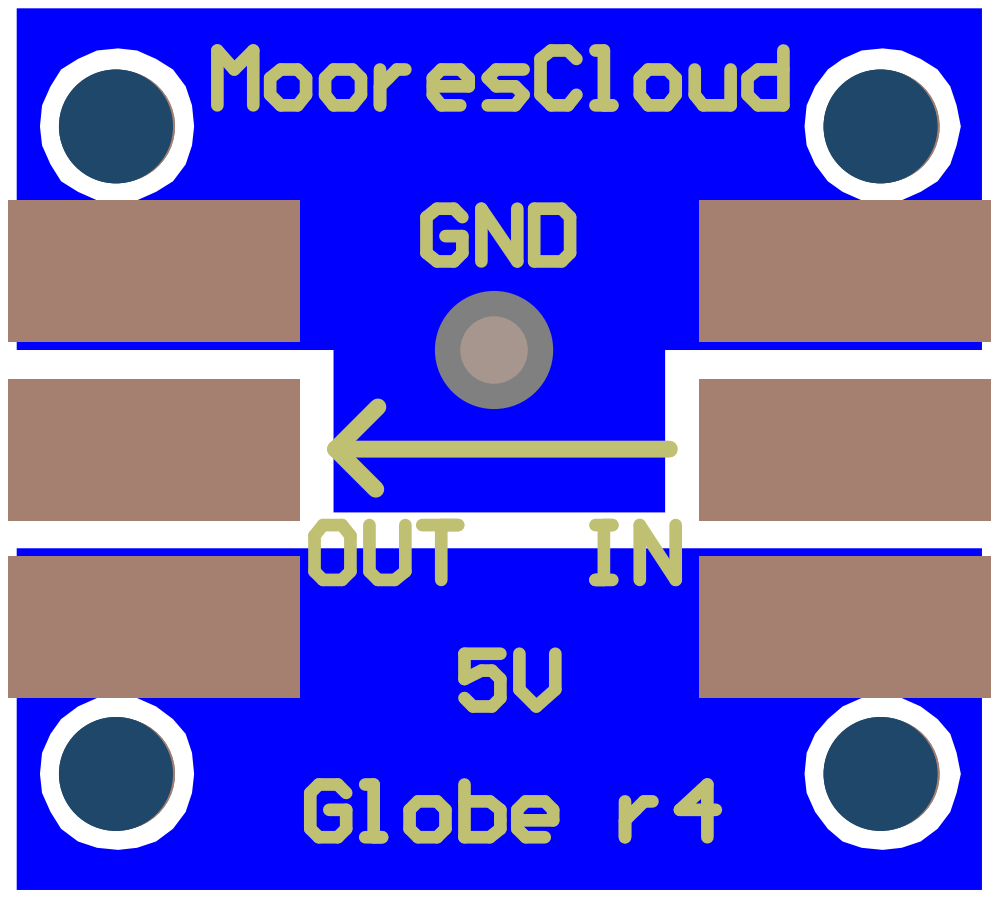
[picture p112: page 8]

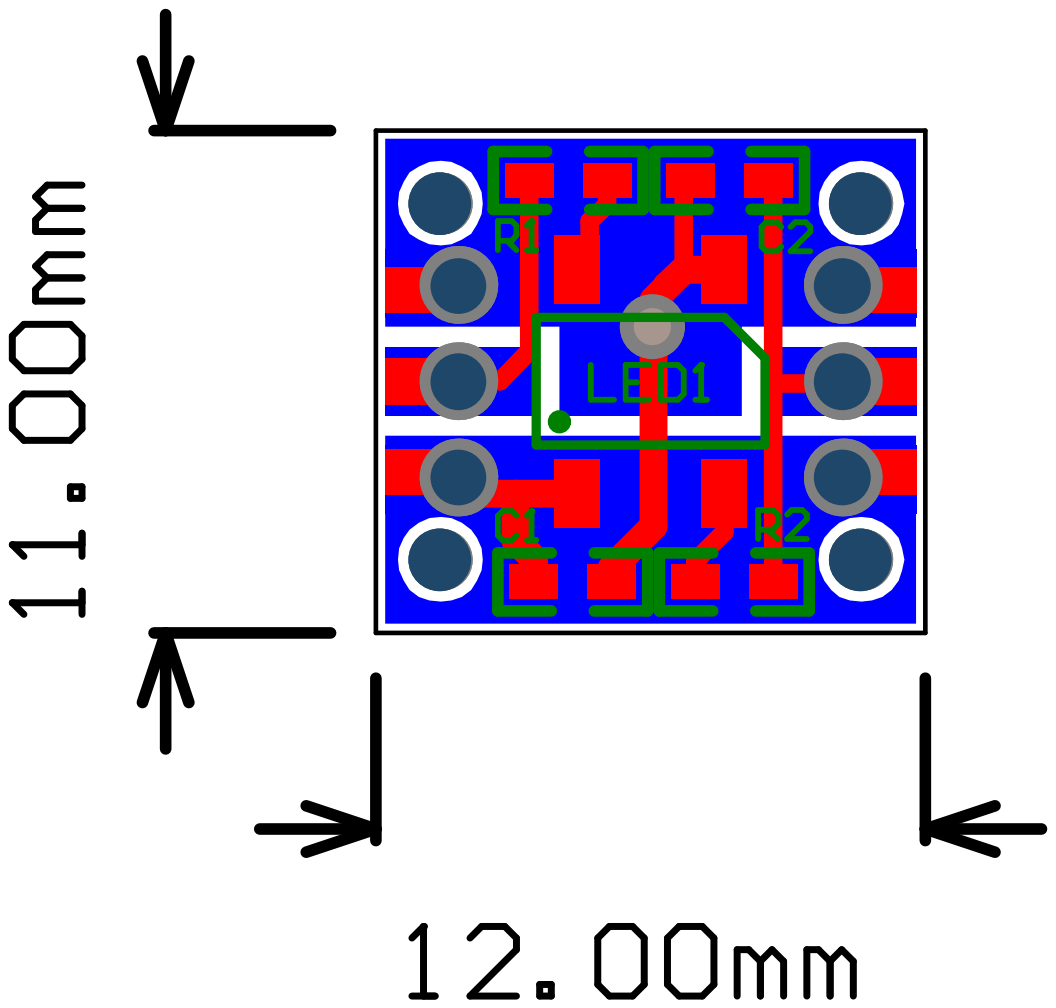
[picture p113: page 9]

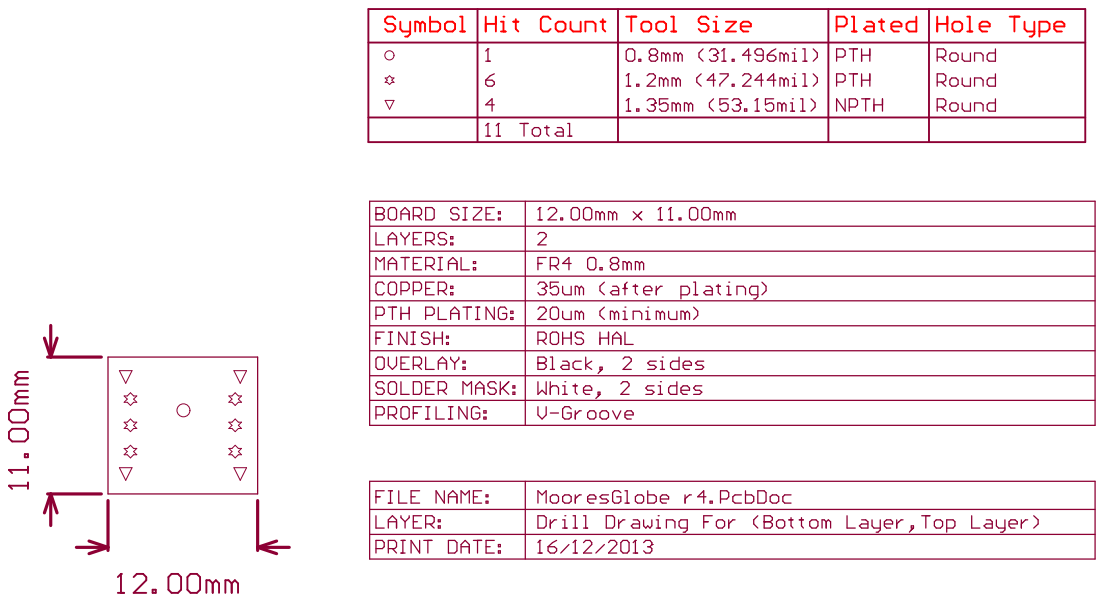
[picture p114: page 10]
