moorescloud/holiday-hardware/Holiday r2 PCB 3D.pdf

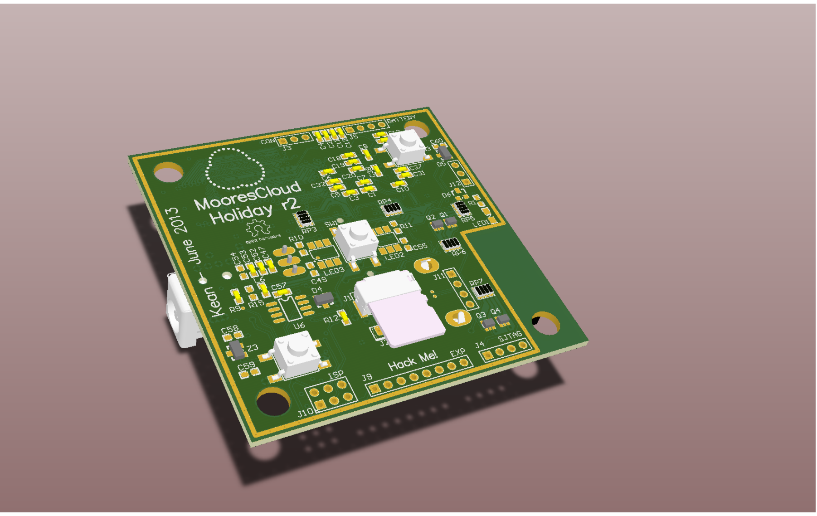
[picture p115: page 1]

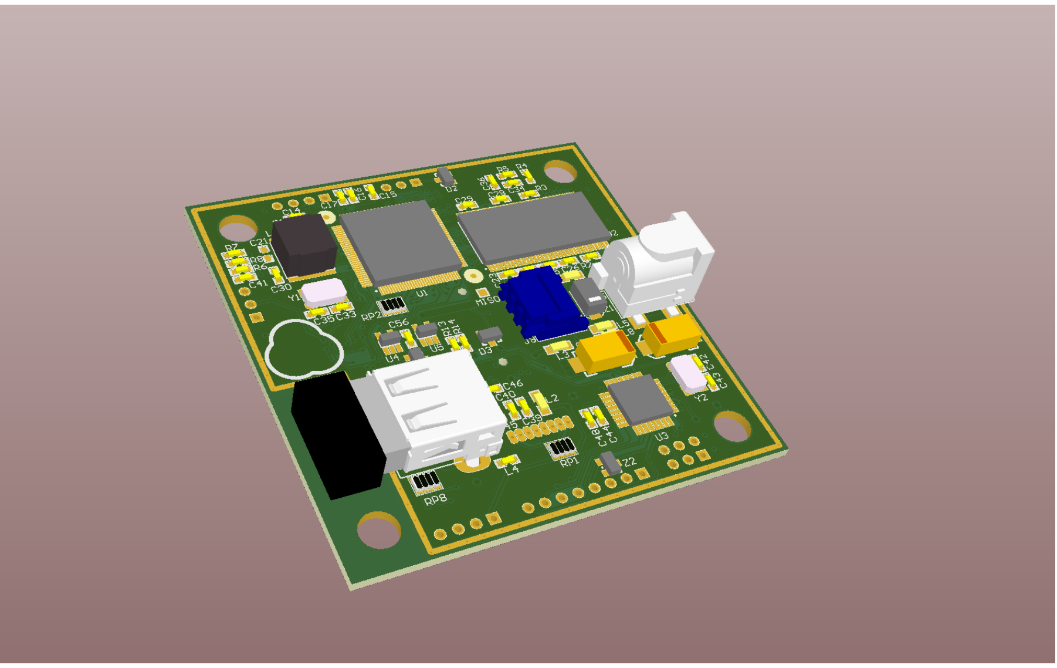
[picture p116: page 2]

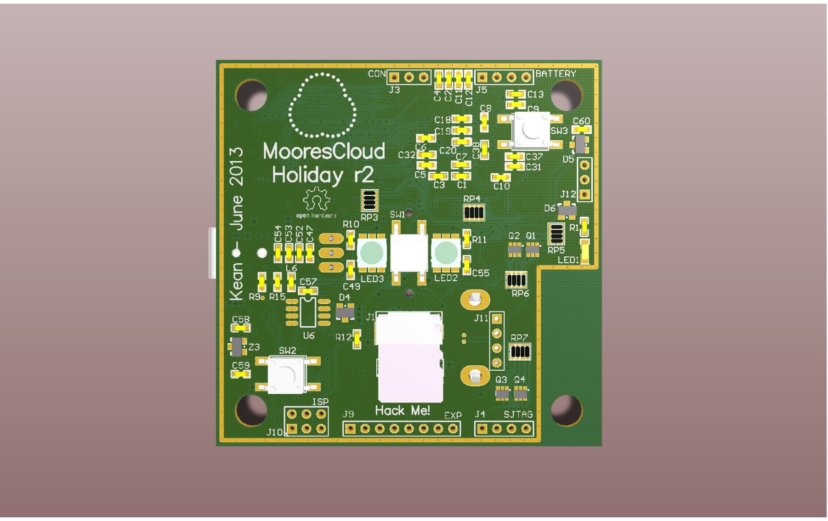
[picture p117: page 3]

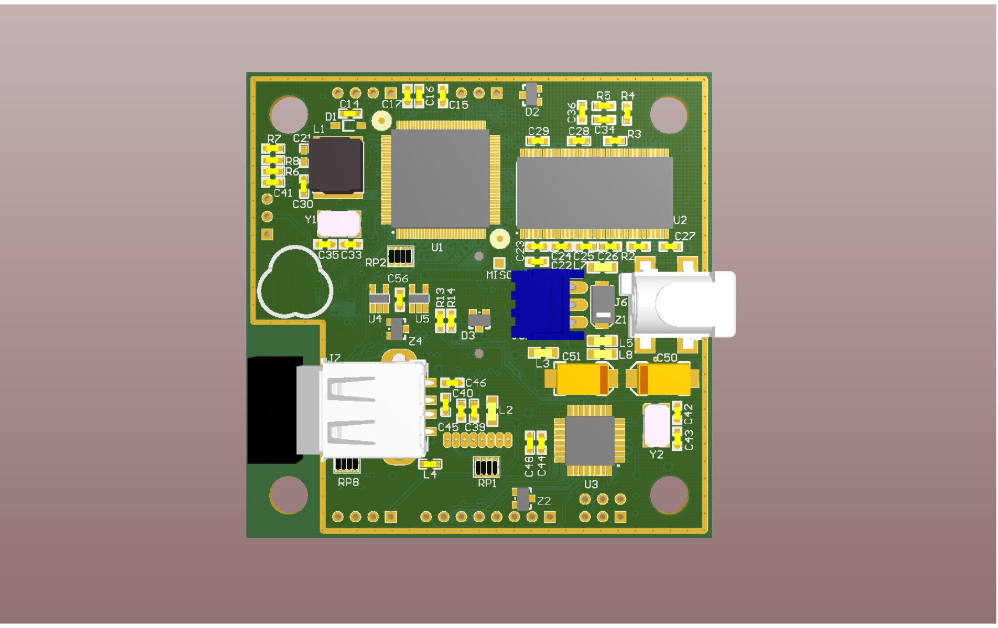
[picture p118: page 4]
